lab11/signpost/case/media/solar_panel_on_signpost_ann_arbor.JPG

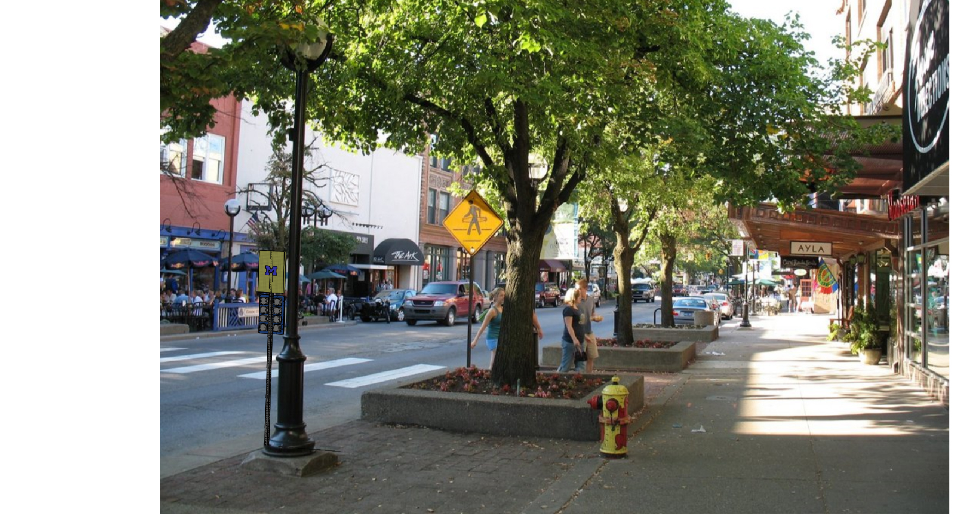
case/media/solar_panel_on_signpost_ann_arbor.JPG
