lab11/signpost/case/quotes/back_panel_quote_proto.JPG

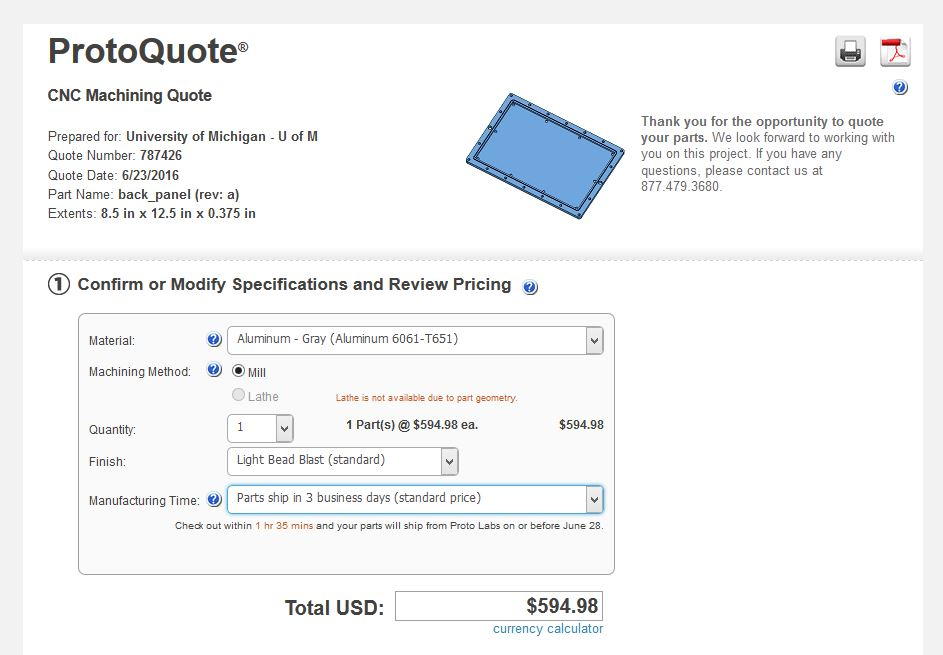
case/quotes/back_panel_quote_proto.JPG
