lab11/signpost/case/quotes/emachineshop.JPG

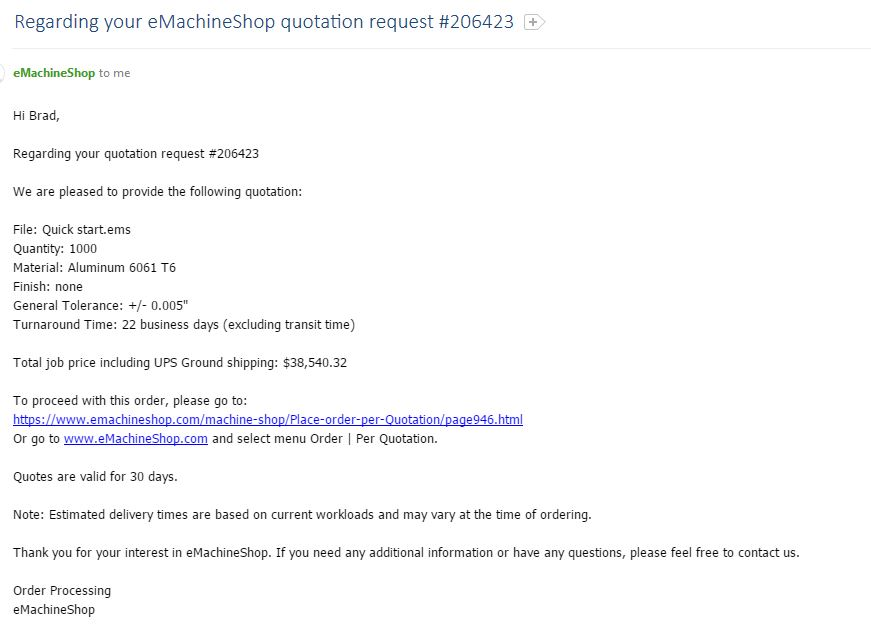
case/quotes/emachineshop.JPG
