lab11/signpost/case/quotes/quick_cut_gasket_oring_quote.jpg

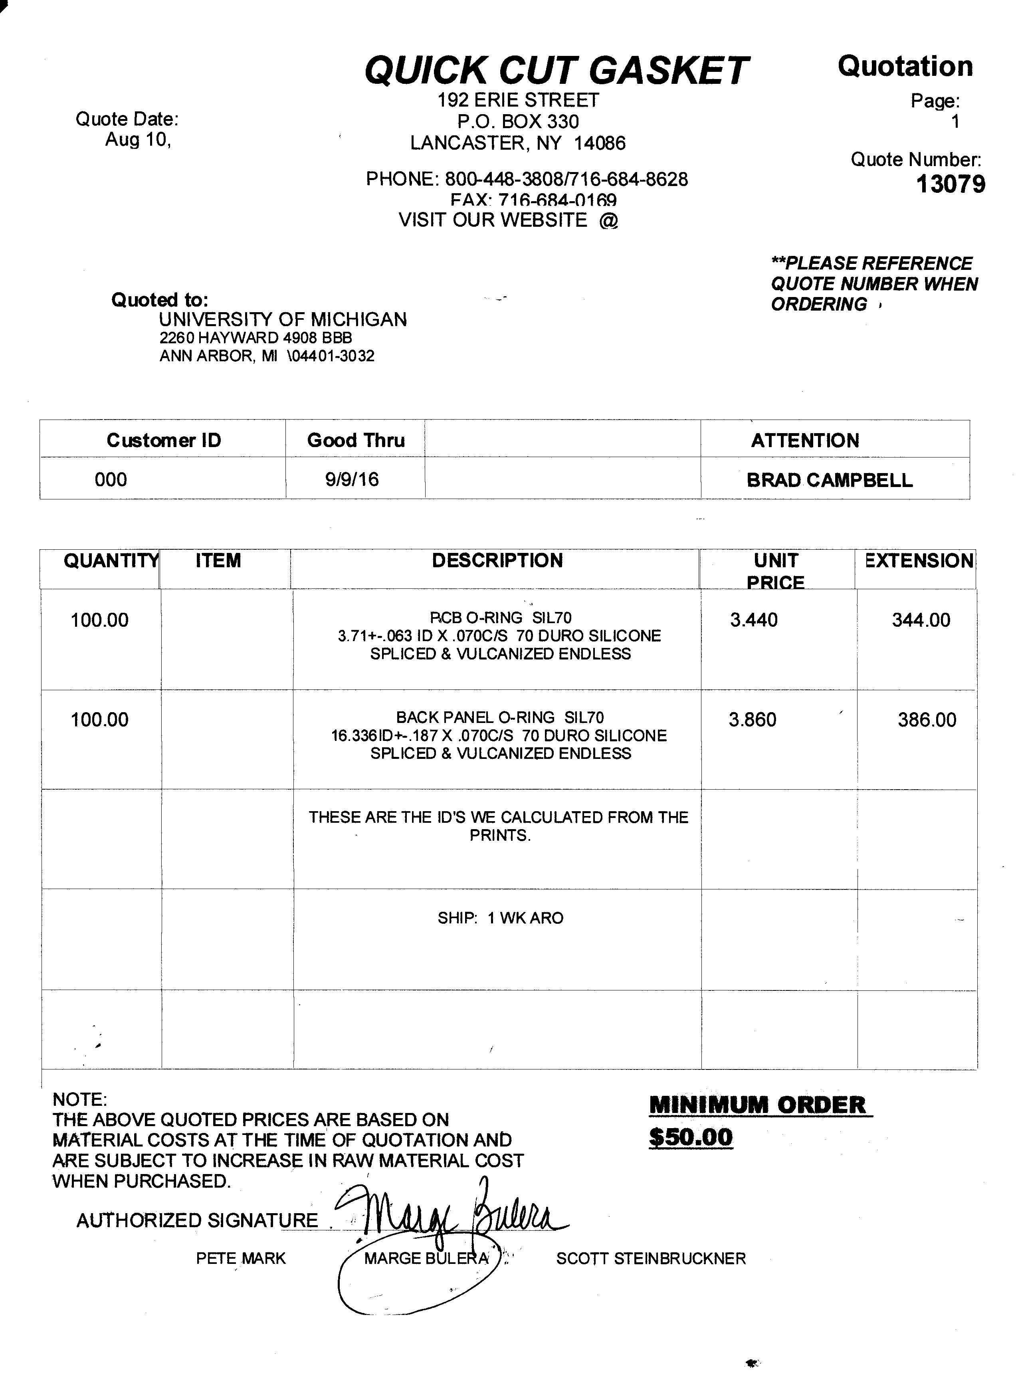
case/quotes/quick_cut_gasket_oring_quote.jpg
