lab11/signpost/case/quotes/xcentric.JPG

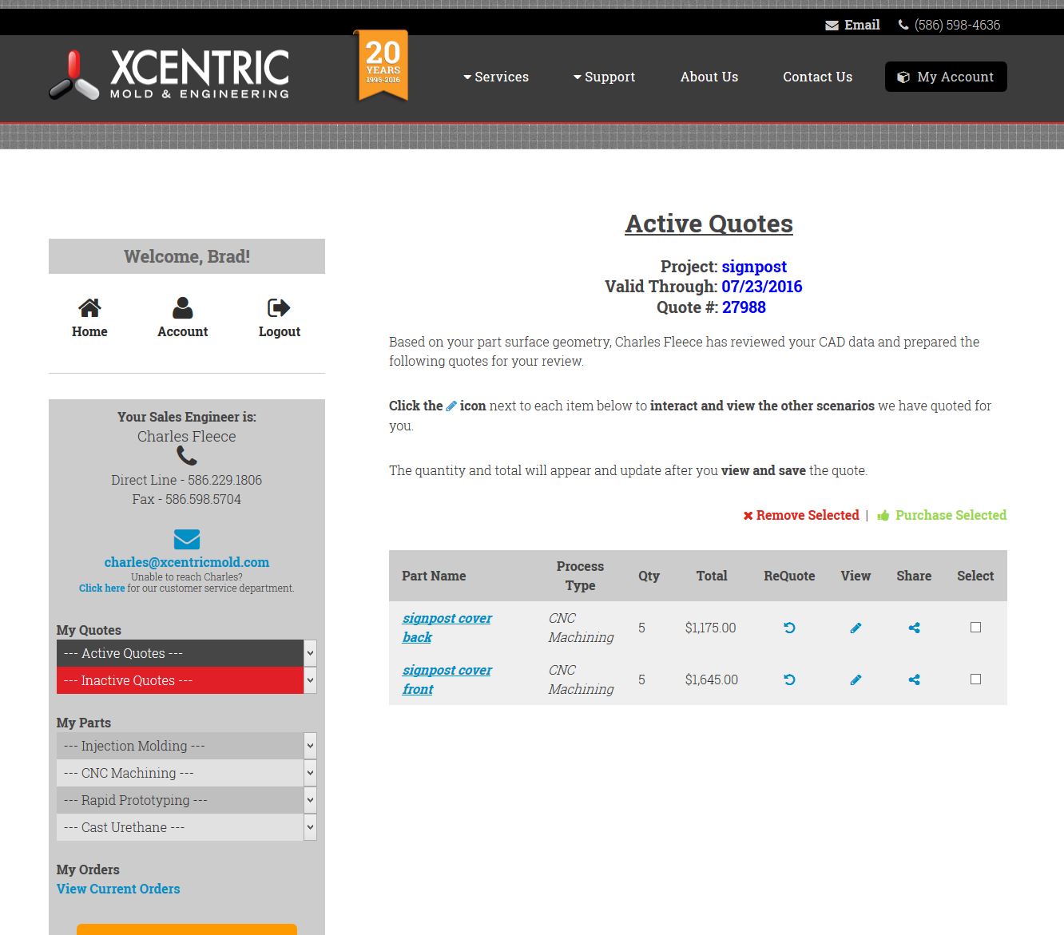
case/quotes/xcentric.JPG
