lab11/signpost/case/quotes/xometry_quote.JPG

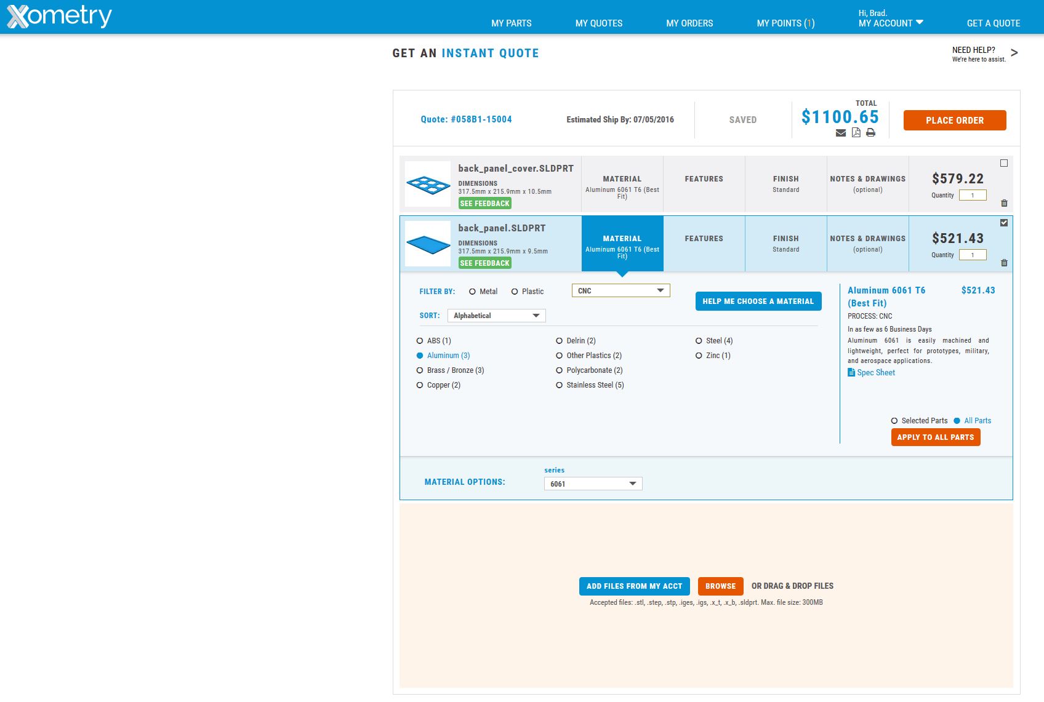
case/quotes/xometry_quote.JPG
