lab11/signpost/media/IntelDeployment.jpg

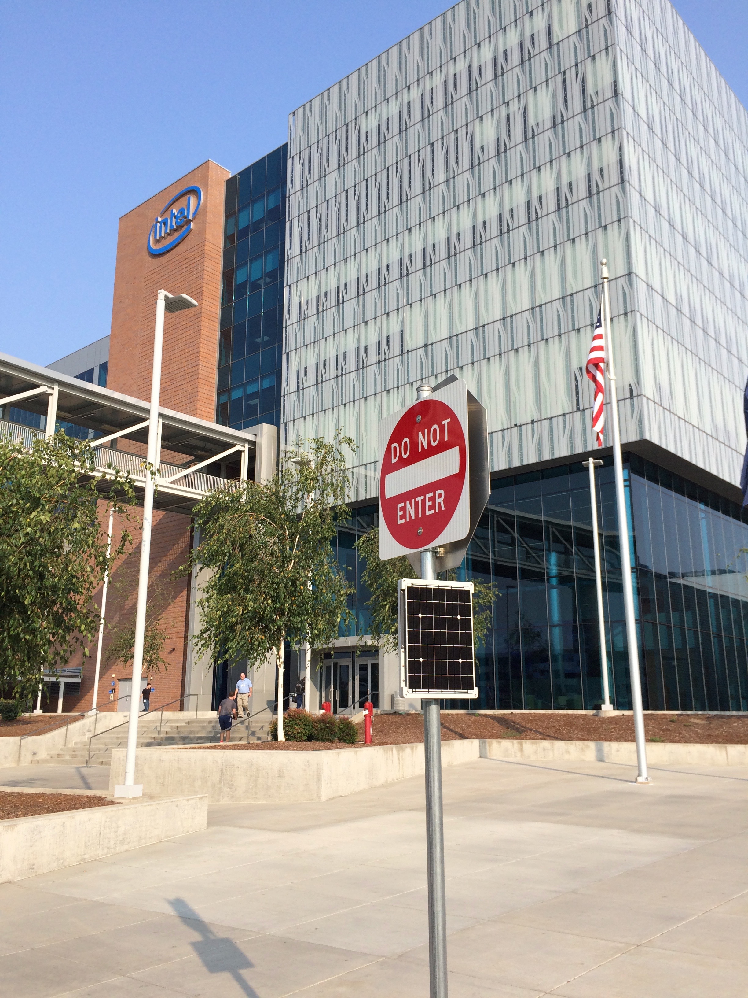
media/IntelDeployment.jpg
