lab11/signpost/media/signpost_case_cad_side_cutout.png

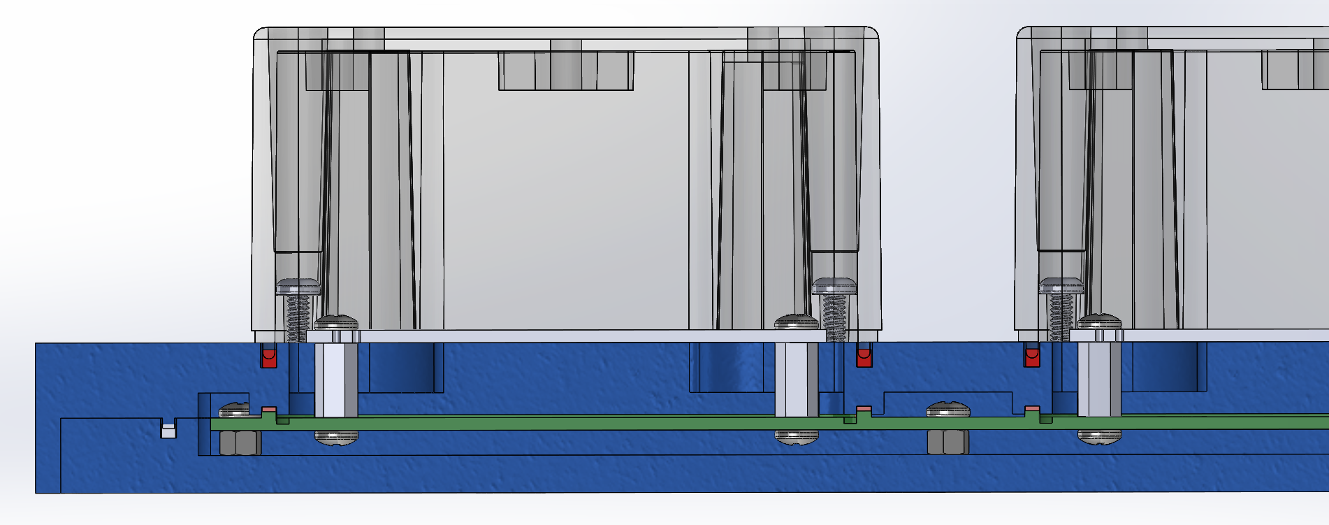
media/signpost_case_cad_side_cutout.png
