lab11/signpost/media/signpost_in_ann_arbor.jpg

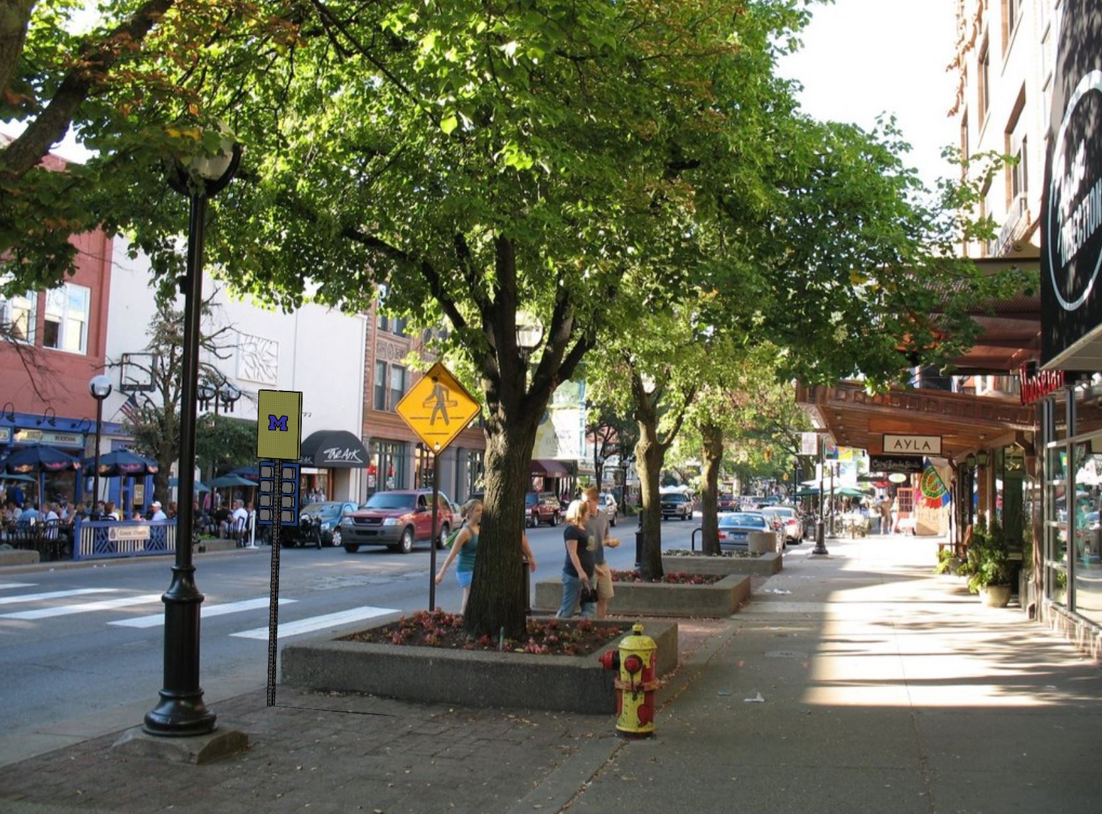
media/signpost_in_ann_arbor.jpg
