lab11/signpost/media/solar_panel_on_signpost6_cropped.jpg

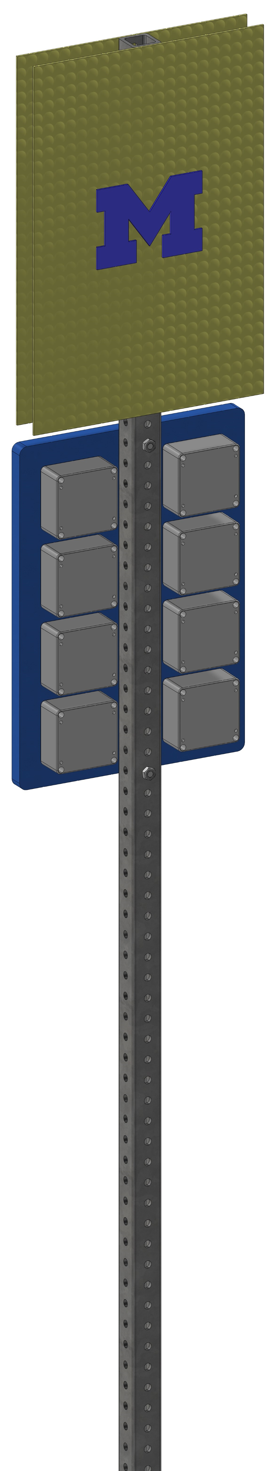
media/solar_panel_on_signpost6_cropped.jpg
