lab11/signpost/modules/ambient/rev_d/ambient.jpg

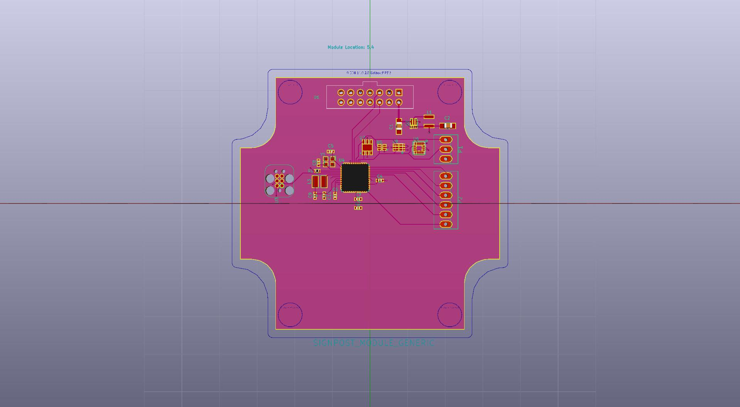
modules/ambient/rev_d/ambient.jpg
