lab11/signpost/hardware/debug_backplane/rev_b/debug_backplane_bom.txt

# Bill of Materials
# Converted from debug_backplane_bom.xlsx
# Generated by bom_to_text.py
#
Part               Value                              Device                             Package                             Description                                                                   DIGIKEY                    DIGIKEY2  DIGIKEY3  DIGIKEY4  DNP  Notes
C1                 8pF                                CAPACITOR0603_CAP                  0603_CAP                            0402 Capacitor                                                                1276-2141-1-ND                                                
C2                 8pF                                CAPACITOR0603_CAP                  0603_CAP                            0402 Capacitor                                                                1276-2141-1-ND                                                
C3                 22pF                               CAPACITOR0603_CAP                  0603_CAP                            0402 Capacitor                                                                478-1167-1-ND                                                 
C4                 22pF                               CAPACITOR0603_CAP                  0603_CAP                            0402 Capacitor                                                                478-1167-1-ND                                                 
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
D5                 LED0603                            LED0603                            LED-0603                            LED                                                                           160-1446-1-ND                                                 
D6                 LED0603                            LED0603                            LED-0603                            LED                                                                           160-1446-1-ND                                                 
D7                 SN75240-TSSOP                      SN75240-TSSOP                      TSSOP-8                             TVS Diodes [suggested for TI USB Hub] (2 array)                               296-6596-1-ND                                                 
D8                 SN75240-TSSOP                      SN75240-TSSOP                      TSSOP-8                             TVS Diodes [suggested for TI USB Hub] (2 array)                               296-6596-1-ND                                                 
D9                 LED0603                            LED0603                            LED-0603                            LED                                                                           160-1446-1-ND                                                 
FB1                600R                               FERRITE_BEAD0603                   0603_CAP                                                                                                          732-1593-1-ND                                                 
FB2                600R                               FERRITE_BEAD0603                   0603_CAP                                                                                                          732-1593-1-ND                                                 
FB3                600R                               FERRITE_BEAD0603                   0603_CAP                                                                                                          732-1593-1-ND                                                 
FB4                600R                               FERRITE_BEAD0603                   0603_CAP                                                                                                          732-1593-1-ND                                                 
FB5                600R                               FERRITE_BEAD0603                   0603_CAP                                                                                                          732-1593-1-ND                                                 
FB6                1.5kR                              FERRITE_BEAD0603                   0603_CAP                                                                                                          490-5216-1-ND                                                 
J1                 BACKPLANE_CONTROLLER_MODULE_DEBUG  BACKPLANE_CONTROLLER_MODULE_DEBUG  BACKPLANE_MODULE_20PIN_10PIN_DEBUG  Control module for signpost, with debug headers                               S9197-ND                   S9194-ND  S7072-ND  S7072-ND       
J2                 BACKPLANE_GENERIC_MODULE_DEBUG     BACKPLANE_GENERIC_MODULE_DEBUG     BACKPLANE_MODULE_14PIN_8PIN         A backplane header for the debug module                                       S9195-ND                   S7072-ND                           
J3                 BACKPLANE_GENERIC_MODULE_DEBUG     BACKPLANE_GENERIC_MODULE_DEBUG     BACKPLANE_MODULE_14PIN_8PIN         A backplane header for the debug module                                       S9195-ND                   S7072-ND                           
J4                 MICRO_USB_B_HIROSE_ZX62R-B-5P      MICRO_USB_B_HIROSE_ZX62R-B-5P      USB_MICRO_B-HIROSE-ZX62R-B-5P       USB Micro B Connector                                                         H11574CT-ND                                                   
J5                 MICRO_USB_B_HIROSE_ZX62R-B-5P      MICRO_USB_B_HIROSE_ZX62R-B-5P      USB_MICRO_B-HIROSE-ZX62R-B-5P       USB Micro B Connector                                                         H11574CT-ND                                                   
J6                 MICRO_USB_B_HIROSE_ZX62R-B-5P      MICRO_USB_B_HIROSE_ZX62R-B-5P      USB_MICRO_B-HIROSE-ZX62R-B-5P       USB Micro B Connector                                                         H11574CT-ND                                                   
J7                 MICRO_USB_B_HIROSE_ZX62R-B-5P      MICRO_USB_B_HIROSE_ZX62R-B-5P      USB_MICRO_B-HIROSE-ZX62R-B-5P       USB Micro B Connector                                                         H11574CT-ND                                                   
J8                 MICRO_USB_B_HIROSE_ZX62R-B-5P      MICRO_USB_B_HIROSE_ZX62R-B-5P      USB_MICRO_B-HIROSE-ZX62R-B-5P       USB Micro B Connector                                                         H11574CT-ND                                                   
J9                 MICRO_USB_B_HIROSE_ZX62R-B-5P      MICRO_USB_B_HIROSE_ZX62R-B-5P      USB_MICRO_B-HIROSE-ZX62R-B-5P       USB Micro B Connector                                                         H11574CT-ND                                                   
J10                                                   ML20                               ML20                                HARTING                                                                       S9172-ND                                                      
J11                PJ-102AH                           PJ-102AH                           PJ-102AH                            DC Power Jack                                                                 CP-102AH-ND                                                   
J12                Debug Header                       2x5 - 0.1" header                  2x5 - 0.1" header                                                                                                 609-3243-ND                                                   
J13                Debug Header                       2x5 - 0.1" header                  2x5 - 0.1" header                                                                                                 609-3243-ND                                                   
J14                Debug Header                       2x5 - 0.1" header                  2x5 - 0.1" header                                                                                                 609-3243-ND                                                   
J15                Debug Header                       2x5 - 0.1" header                  2x5 - 0.1" header                                                                                                 609-3243-ND                                                   
J16                Debug Header                       1x3 - 0.1" Header                  1x3 - 0.1" Header                                                                                                 3M9448-ND                                                     
J17                Debug Header                       1x3 - 0.1" Header                  1x3 - 0.1" Header                                                                                                 3M9448-ND                                                     
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
S8                 B3U-1000P                          B3U-1000P                          B3U-1000P                           Switch                                                                        SW1020CT-ND                                                   
S9                 NC7SZ157                           NC7SZ157                           SC70-6                              MUX                                                                           NC7SZ157P6XCT-ND                                              
S10                NC7SZ157                           NC7SZ157                           SC70-6                              MUX                                                                           NC7SZ157P6XCT-ND                                              
S11                RM106772BCB                        RM106772BCB                        RM-SWITCH                           Rotary Switch 6 Position SP6T 500mA (DC) 24VDC Through Hole                   CKN10703-ND                                                   
S12                SIP3240X                           SIP3240X                           TDFN4                               High power (2.4 A) high-side switch                                           SIP32402ADNP-T1GE4CT-ND                                       
S13                SIP3240X                           SIP3240X                           TDFN4                               High power (2.4 A) high-side switch                                           SIP32402ADNP-T1GE4CT-ND                                       
S14                SN74AHC4066-RGY                    SN74AHC4066-RGY                    S-PVQFN-N14-3.5MM                                                                                                 296-15258-1-ND                                                
S15                SN74AHC4066-RGY                    SN74AHC4066-RGY                    S-PVQFN-N14-3.5MM                                                                                                 296-15258-1-ND                                                
S16                SN74AHC4066-RGY                    SN74AHC4066-RGY                    S-PVQFN-N14-3.5MM                                                                                                 296-15258-1-ND                                                
S17                SN74AHC4066-RGY                    SN74AHC4066-RGY                    S-PVQFN-N14-3.5MM                                                                                                 296-15258-1-ND                                                
S18                SN74AHC4066-RGY                    SN74AHC4066-RGY                    S-PVQFN-N14-3.5MM                                                                                                 296-15258-1-ND                                                
S19                TE_SSA12/SPDT                      TE_SSA12/SPDT                      TE_SSA12/SPDT                       SWITCH SLIDE SPDT 2POS SSA SER                                                450-1602-ND                                                   
TP_GND             TEST_POINT_0.040IN                 TEST_POINT_0.040IN                 TESTPOINT_0.040IN                   0.040in Test Point                                                            36-5001-ND                                                    As Labeled on board - under J11
TP_5V              TEST_POINT_0.040IN                 TEST_POINT_0.040IN                 TESTPOINT_0.040IN                   0.040in Test Point                                                            36-5000-ND                                                    As Labeled on board - under J12
TP_3V3             TEST_POINT_0.040IN                 TEST_POINT_0.040IN                 TESTPOINT_0.040IN                   0.040in Test Point                                                            36-5000-ND                                                    As Labeled on board - under J13
TP_Mod0_VCC        TEST_POINT_0.040IN                 TEST_POINT_0.040IN                 TESTPOINT_0.040IN                   0.040in Test Point                                                            36-5003-ND                                                    As Labeled on board - under J14
TP_Mod1_VCC        TEST_POINT_0.040IN                 TEST_POINT_0.040IN                 TESTPOINT_0.040IN                   0.040in Test Point                                                            36-5003-ND                                                    As Labeled on board - under J15
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
U5                 FT232RQ                            FT232RQ                            QFN32                               Source: http://www.ftdichip.com/Documents/DataSheets/DS_FT232R_v104.pdf       768-1307-ND                                                   
U6                 FXMA2102                           FXMA2102                           UMLP-8                              Dual Supply, 2-Bit Voltage Translator / Buffer / Repeater / Isolator for I2C  FXMA2102UMXCT-ND                                              
U7                 FXMA2102                           FXMA2102                           UMLP-8                              Dual Supply, 2-Bit Voltage Translator / Buffer / Repeater / Isolator for I2C  FXMA2102UMXCT-ND                                              
U8                 LTC2941                            LTC2941                            DFN-6-2MMX3MM                       I2C Battery Gas Gauge                                                         LTC2941IDCB#TRMPBFCT-ND                                       
U9                 LTC2941                            LTC2941                            DFN-6-2MMX3MM                       I2C Battery Gas Gauge                                                         LTC2941IDCB#TRMPBFCT-ND                                       
U10                LTC2941                            LTC2941                            DFN-6-2MMX3MM                       I2C Battery Gas Gauge                                                         LTC2941IDCB#TRMPBFCT-ND                                       
U11                LTC2941                            LTC2941                            DFN-6-2MMX3MM                       I2C Battery Gas Gauge                                                         LTC2941IDCB#TRMPBFCT-ND                                       
U12                MAX8887EZK33+T                     MAX8887EZK33+T                     SOT-23-5                            IC REG LDO 3.3V 0.3A TSOT23-5                                                 MAX8887EZK33+TCT-ND                                           
U13                MCP23008QFN                        MCP23008QFN                        QFN-20-4MM                          GPIO Extender via I2C - 8 Pin                                                 MCP23008-E/ML-ND                                              
U14                MCP23008QFN                        MCP23008QFN                        QFN-20-4MM                          GPIO Extender via I2C - 8 Pin                                                 MCP23008-E/ML-ND                                              
U15                PCA9544AQFN-N20                    PCA9544AQFN-N20                    QFN-N20                             1-4 I2C/SMBUS Multiplexer with interrupt for power supply coulomb counters    296-20960-1-ND                                                
U16                SAM4LC8AA                          SAM4LC8AA                          QFN-48-7MM                          Atmel SAM4L microcontroller. ARM Cortex M4 with 512 KB Flash and 64 KB RAM    ATSAM4LC8AA-MU-ND                                             
U17                SN74LVC2T45                        SN74LVC2T45                        VFSOP-8                             Bidirectional Buffer / Level Converter 2 Circuits                             296-17014-1-ND                                                
U18                SN74LVC2T45                        SN74LVC2T45                        VFSOP-8                             Bidirectional Buffer / Level Converter 2 Circuits                             296-17014-1-ND                                                
U19                SN74LVC2T45                        SN74LVC2T45                        VFSOP-8                             Bidirectional Buffer / Level Converter 2 Circuits                             296-17014-1-ND                                                
U20                SN74LVC2T45                        SN74LVC2T45                        VFSOP-8                             Bidirectional Buffer / Level Converter 2 Circuits                             296-17014-1-ND                                                
U21                TS3USB30E                          TS3USB30E                          UQFN-10                             USB Mux with OE control and ESD                                               296-24684-1-ND                                                
U22                TS3USB30E                          TS3USB30E                          UQFN-10                             USB Mux with OE control and ESD                                               296-24684-1-ND                                                
U23                TS3USB30E                          TS3USB30E                          UQFN-10                             USB Mux with OE control and ESD                                               296-24684-1-ND                                                
U24                TUSB2077A                          TUSB2077A                          LQFP-48                             Full Speed USB Hub - 7 Port                                                   296-37871-1-ND                                                
U25                LTC4360                            LTC4360                            SC70-8                              An overvoltage protection IC. Clamps at 5.5V                                  LTC4360CSC8-1#TRMPBFCT-ND                                     
X1                 16MHz                              FH1600015                          FHXXX                               Pericom Type FH 16 MHz 2.5 x 2.0 mm                                           FH1600015CT-ND                                                
Y1                 ABMM                               ABMM                               ABMM                                Low-Profile SMD crystal                                                       535-10156-1-ND
