lab11/signpost/hardware/debug_backplane/rev_b/debug_backplane_bom_digikey.txt

# Bill of Materials
# Converted from debug_backplane_bom_digikey.xlsx
# Generated by bom_to_text.py
#
# Part List           Digikey Part Number        QTY
C1-2                 1276-2141-1-ND             2
C11                  490-1313-1-ND              1
C12-15 45            478-1129-1-ND              5
C16-44 46-61         490-1532-1-ND              45
C3-4                 478-1167-1-ND              2
C5-10                399-8827-1-ND              6
C62-63               490-3296-1-ND              2
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
