lab11/signpost/case/parts/For_UM_Machine_Shop/back_panel_cover/2D/back_panel_cover.JPG

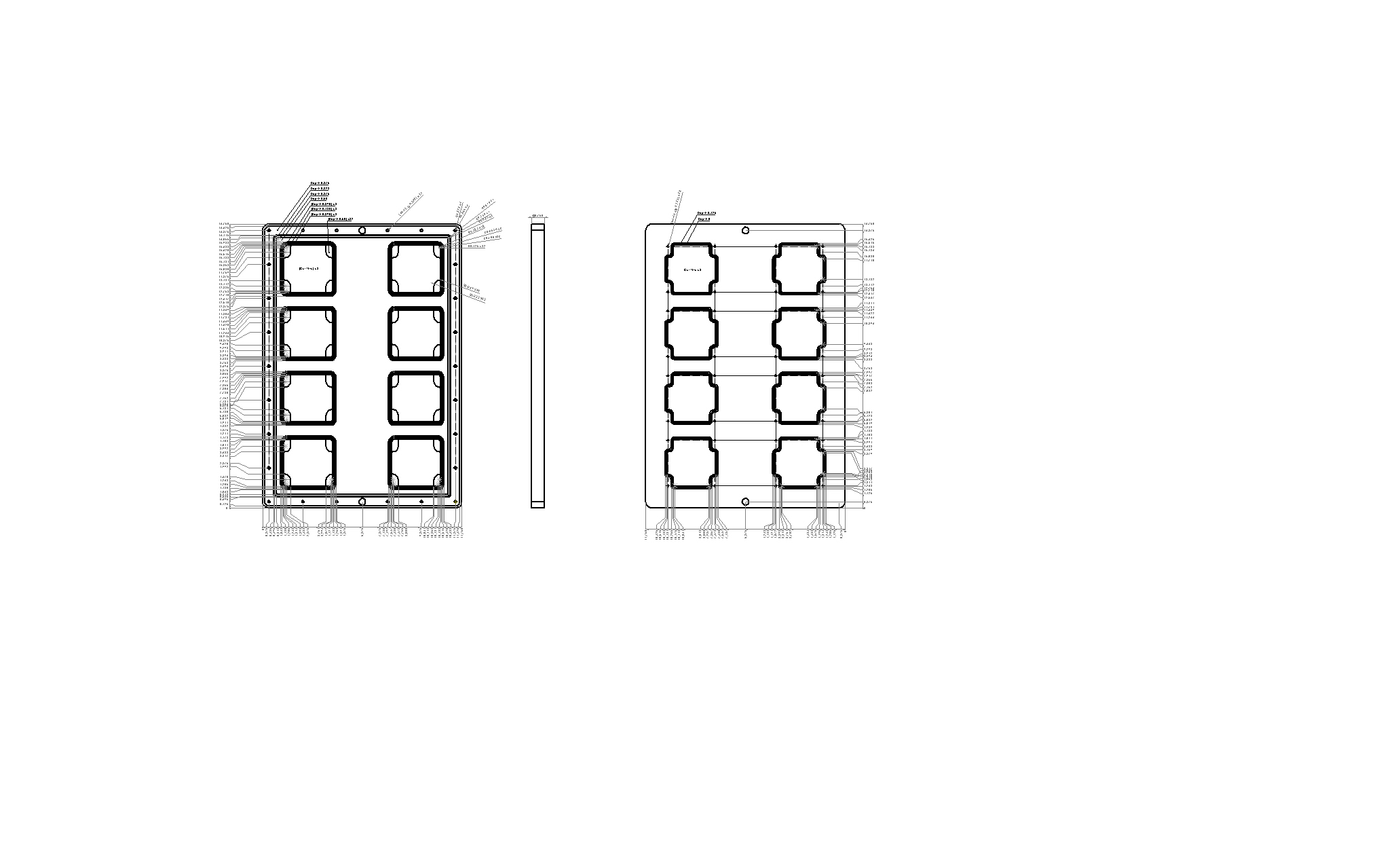
case/parts/For_UM_Machine_Shop/back_panel_cover/2D/back_panel_cover.JPG
