lab11/signpost/case/parts/For_UM_Machine_Shop/solar_mount/2D/solar_mount.JPG

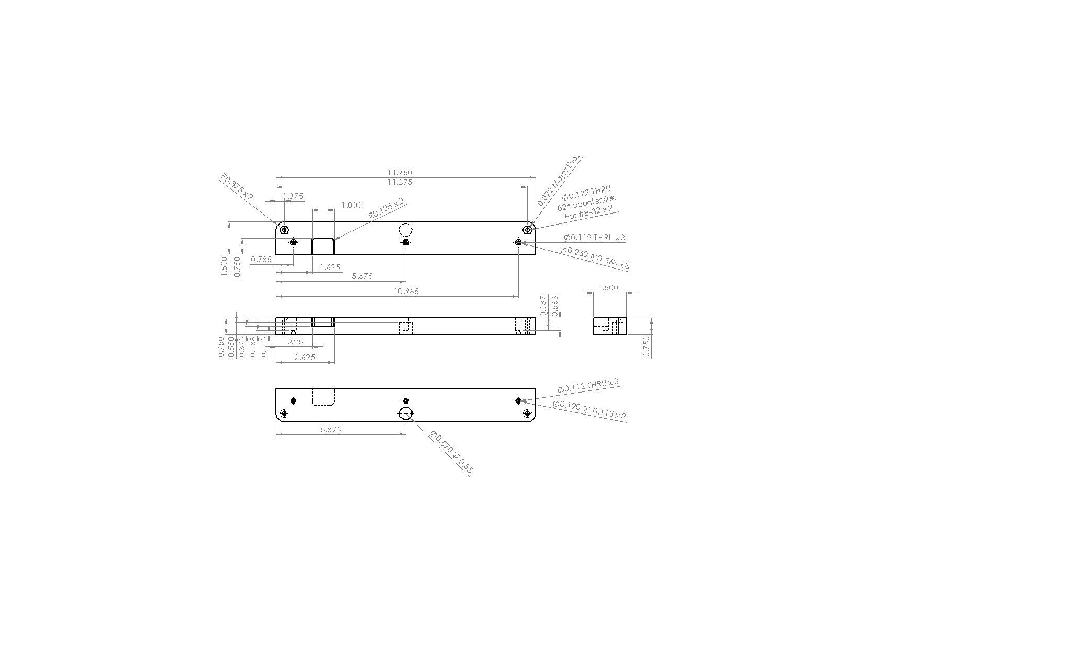
case/parts/For_UM_Machine_Shop/solar_mount/2D/solar_mount.JPG
