lab11/signpost/case/parts/Product_files/sunpe_04_28_2017/battery_case_top.STEP

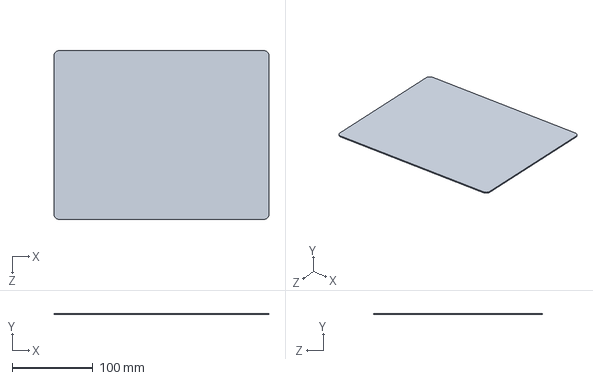
[picture p40: CAD file, 2017-05-03]
case/parts/Product_files/sunpe_04_28_2017/battery_case_top.STEP
266.7 x 1.59 x 209.4 mm
