lab11/signpost/case/parts/back_panel_cover.SLDPRT

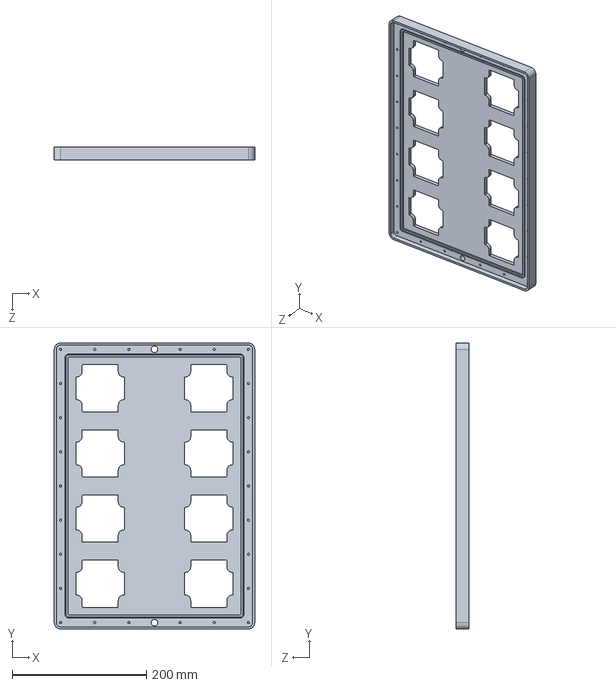
[picture p41: CAD file, 2017-04-20]
case/parts/back_panel_cover.SLDPRT
298.5 x 425.5 x 19.1 mm
