lab11/signpost/case/parts/battery_case_back.STEP

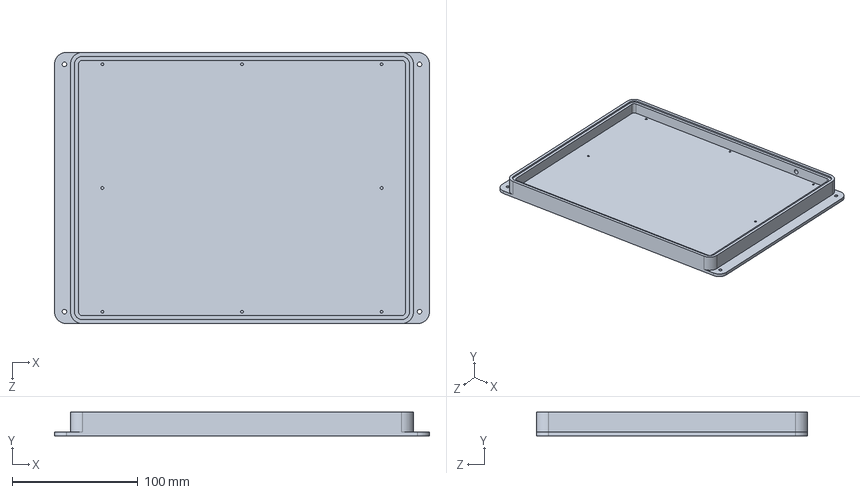
[picture p42: CAD file, 2017-02-01]
case/parts/battery_case_back.STEP
298.4 x 19.1 x 215.9 mm
