lab11/signpost/case/parts/COTS_hardware/round_sign_bracket.SLDPRT

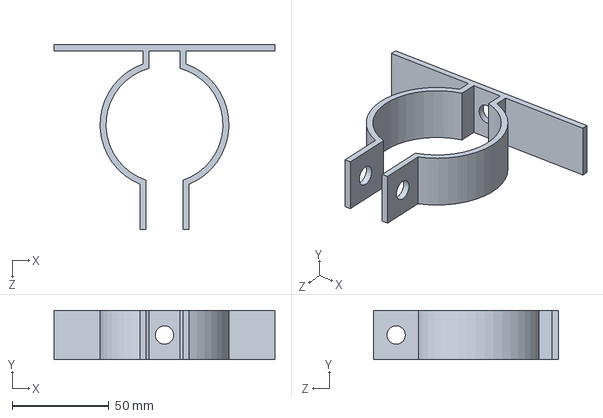
[picture p43: CAD file, 2017-01-26]
case/parts/COTS_hardware/round_sign_bracket.SLDPRT
114.3 x 25.4 x 95.5 mm
