lab11/signpost/case/parts/round_post.SLDPRT

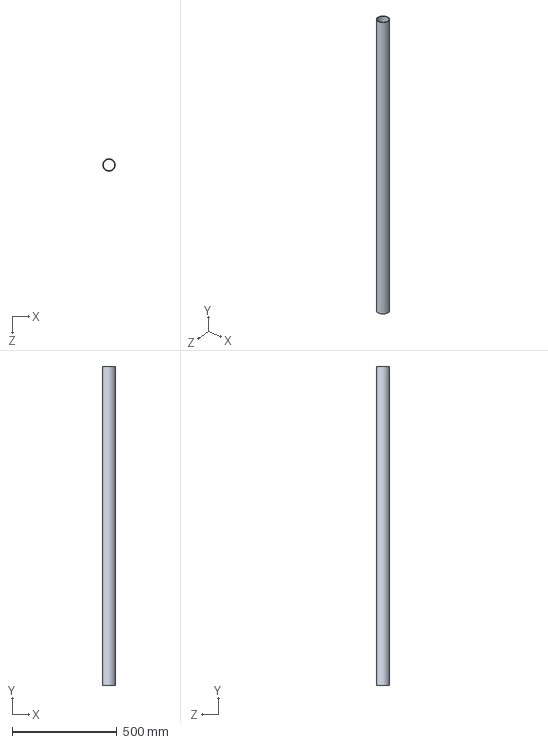
[picture p44: CAD file, 2017-01-26]
case/parts/round_post.SLDPRT
60.5 x 1524.0 x 60.5 mm
