lab11/signpost/case/parts/module_pcb.SLDPRT

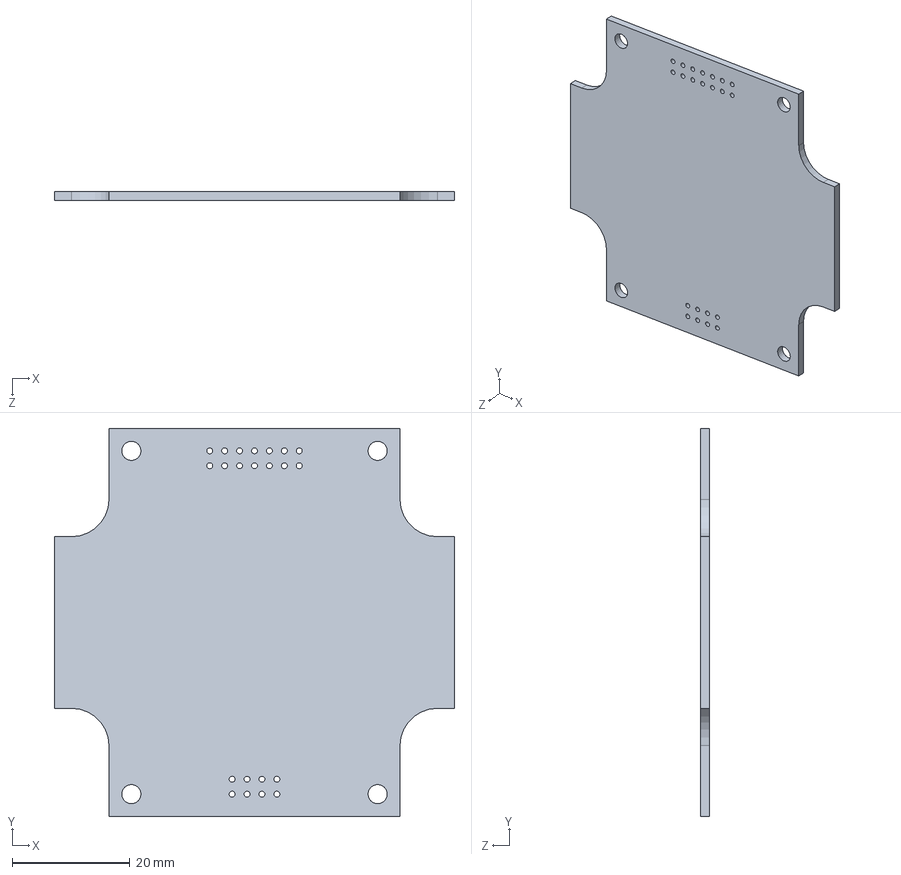
[picture p45: CAD file, 2017-01-19]
case/parts/module_pcb.SLDPRT
68.1 x 66.0 x 1.59 mm
