lab11/signpost/case/parts/batter_pack_pcb.SLDPRT

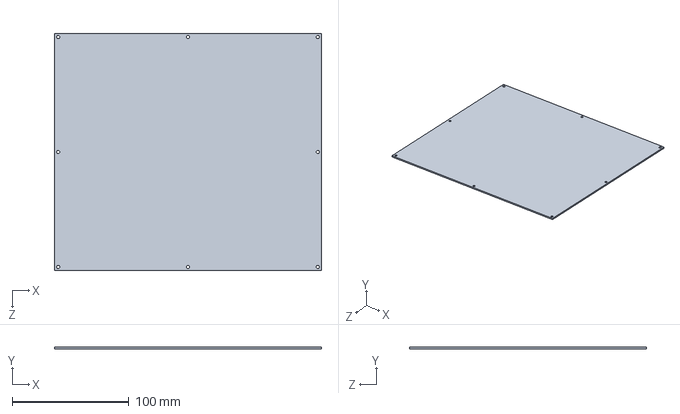
[picture p46: CAD file, 2017-01-08]
case/parts/batter_pack_pcb.SLDPRT
228.6 x 1.59 x 203.2 mm
