lab11/signpost/case/parts/battery_cell.SLDPRT

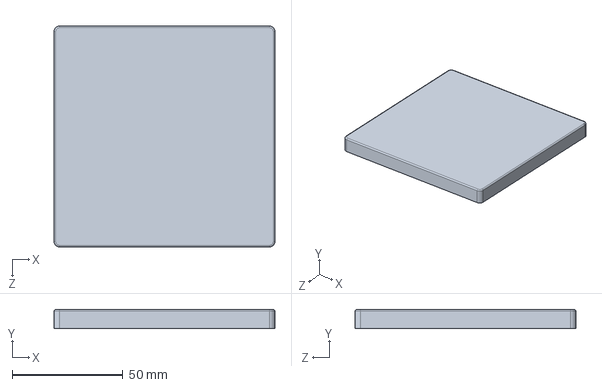
[picture p47: CAD file, 2017-01-08]
case/parts/battery_cell.SLDPRT
100.0 x 8.60 x 100.0 mm
