lab11/signpost/case/parts/battery_case_front.SLDPRT

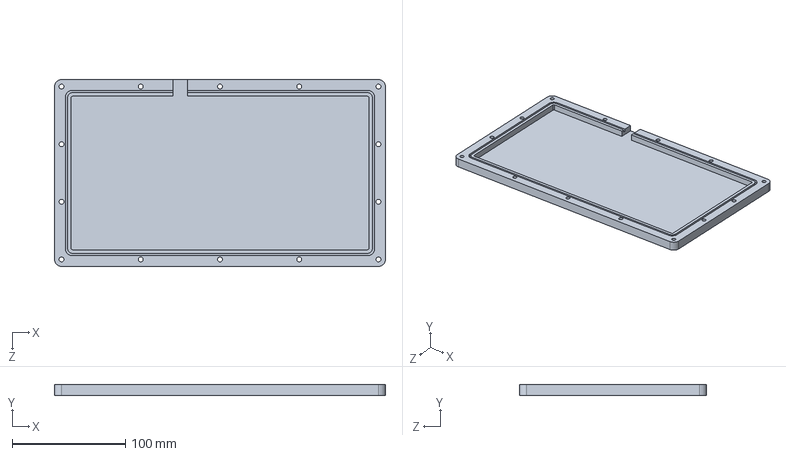
[picture p48: CAD file, 2016-09-11]
case/parts/battery_case_front.SLDPRT
291.8 x 9.53 x 164.8 mm
