lab11/signpost/case/parts/17W Panel.SLDPRT

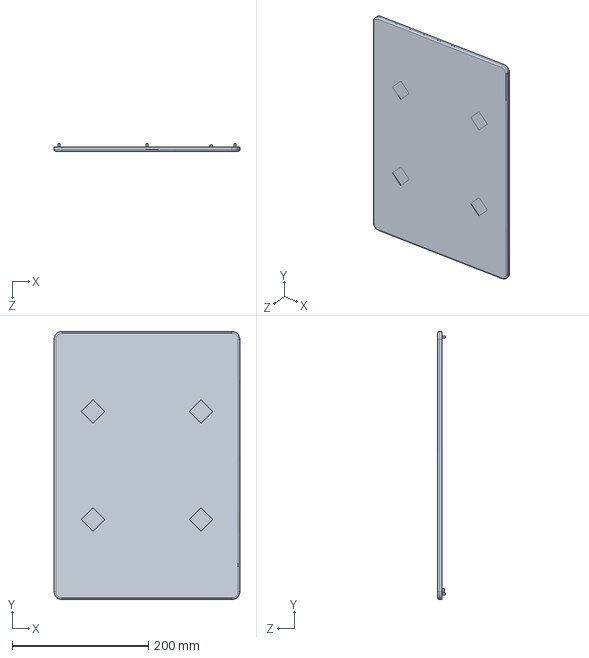
[picture p49: CAD file, 2016-09-11]
case/parts/17W Panel.SLDPRT
273.1 x 393.7 x 11.0 mm
