lab11/signpost/case/parts/gold_sign.SLDPRT

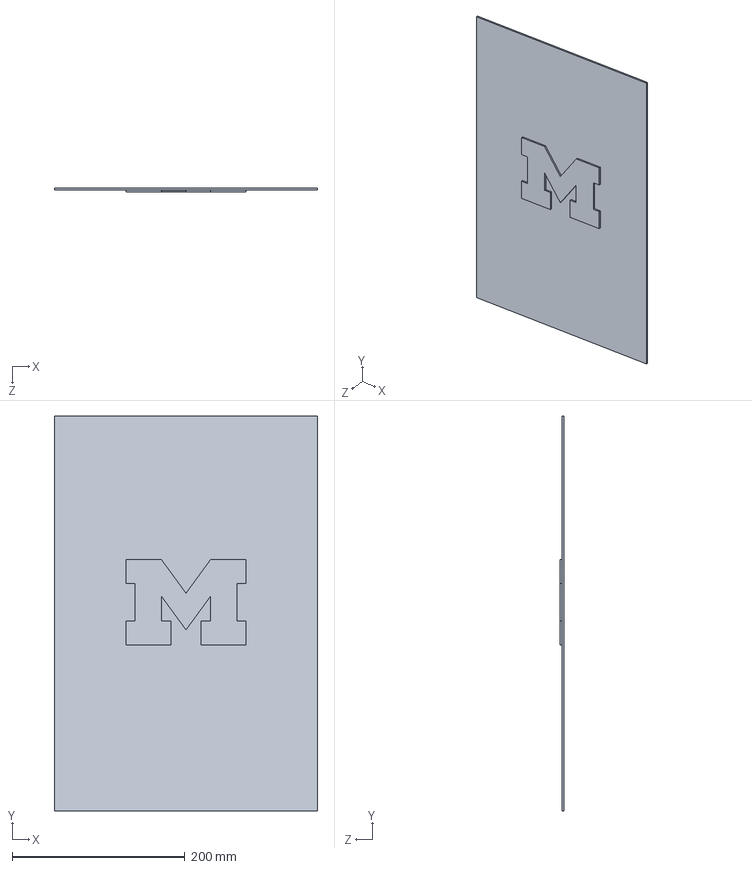
[picture p50: CAD file, 2016-08-11]
case/parts/gold_sign.SLDPRT
304.8 x 457.2 x 5.08 mm
