lab11/signpost/case/parts/SFH11-P_ _C-D07-ST-_ _.SLDPRT

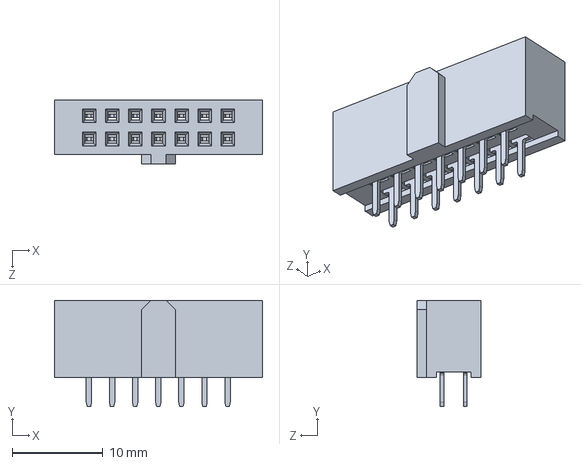
[picture p51: CAD file, 2016-08-09]
case/parts/SFH11-P_ _C-D07-ST-_ _.SLDPRT
22.9 x 11.7 x 7.00 mm
