lab11/signpost/case/parts/COTS_hardware/1-8-ips-3-4-long.SLDPRT

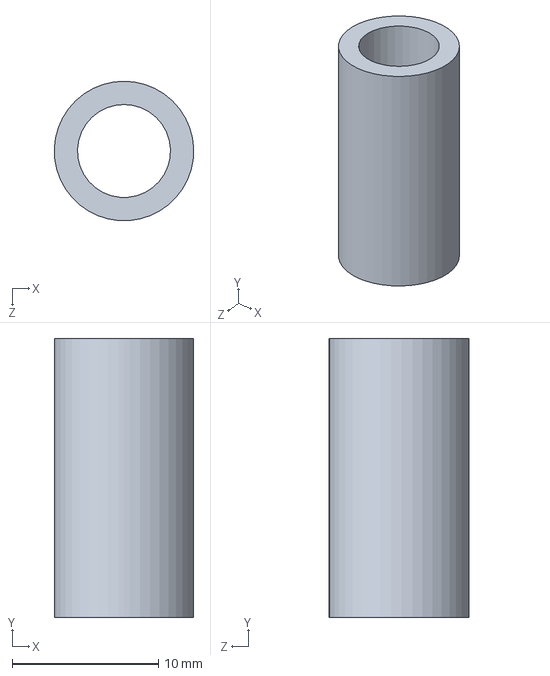
[picture p52: CAD file, 2016-09-11]
case/parts/COTS_hardware/1-8-ips-3-4-long.SLDPRT
9.52 x 19.1 x 9.53 mm
