lab11/signpost/case/parts/voltaic_17w_solar_panel_mount.SLDPRT

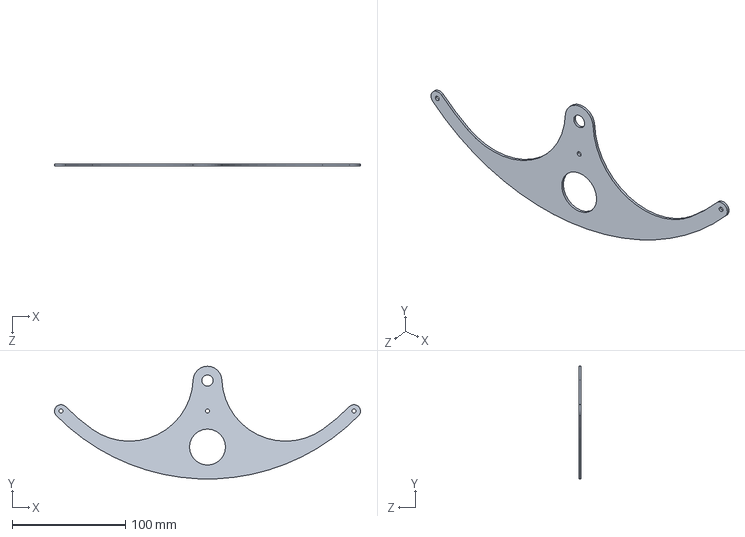
[picture p53: CAD file, 2016-08-08]
case/parts/voltaic_17w_solar_panel_mount.SLDPRT
270.0 x 99.4 x 1.90 mm
