lab11/signpost/case/parts/back_panel_oring.SLDPRT

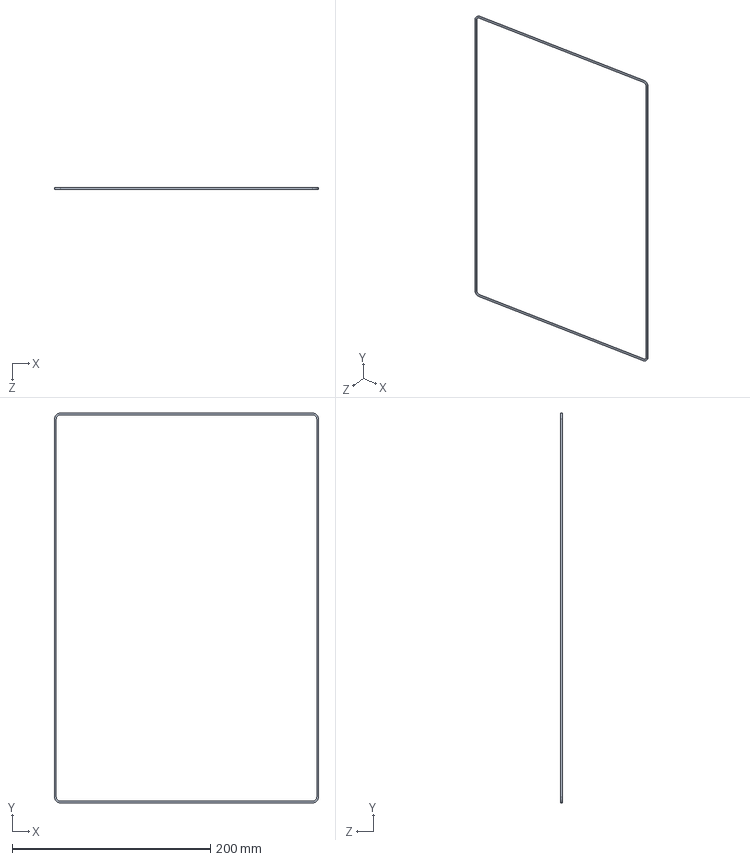
[picture p54: CAD file, 2016-08-08]
case/parts/back_panel_oring.SLDPRT
266.4 x 393.4 x 1.78 mm
