lab11/signpost/case/parts/module_pcb_oring.SLDPRT

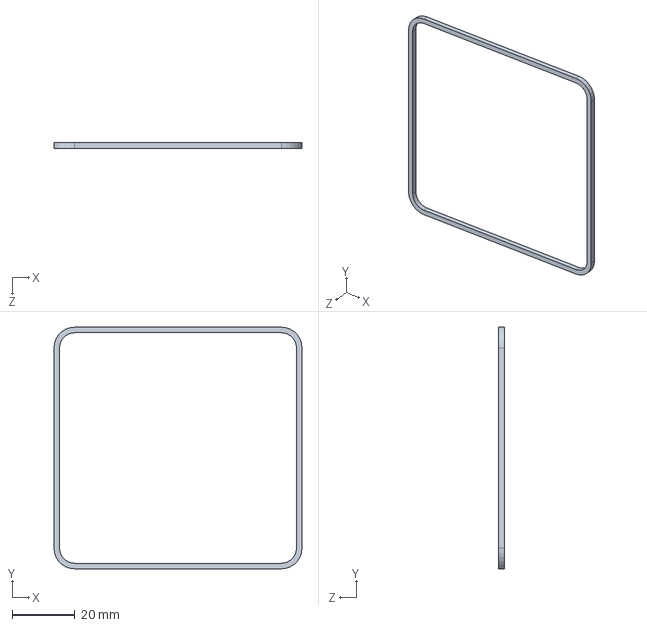
[picture p55: CAD file, 2016-08-08]
case/parts/module_pcb_oring.SLDPRT
79.3 x 77.3 x 1.78 mm
