lab11/signpost/case/parts/post.SLDPRT

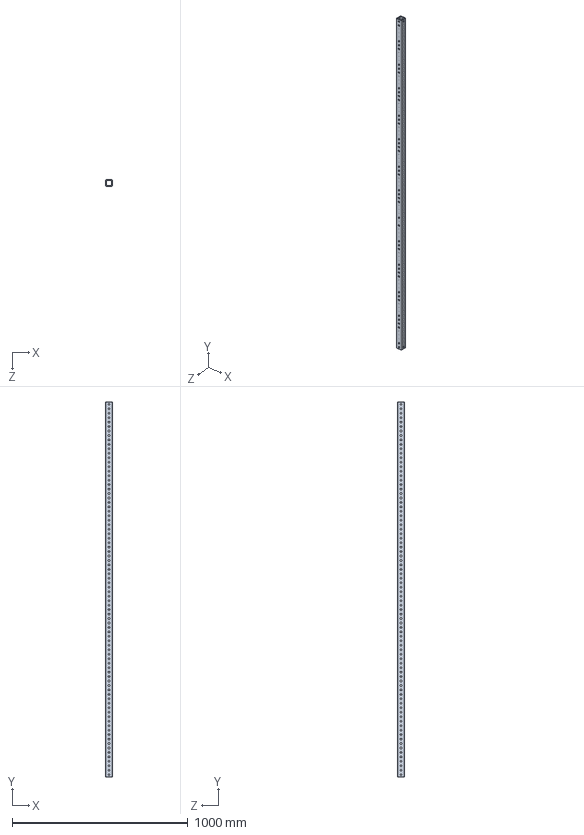
[picture p56: CAD file, 2016-07-01]
case/parts/post.SLDPRT
38.1 x 2133.6 x 38.1 mm
