lab11/signpost/case/parts/COTS_hardware/plug.SLDPRT

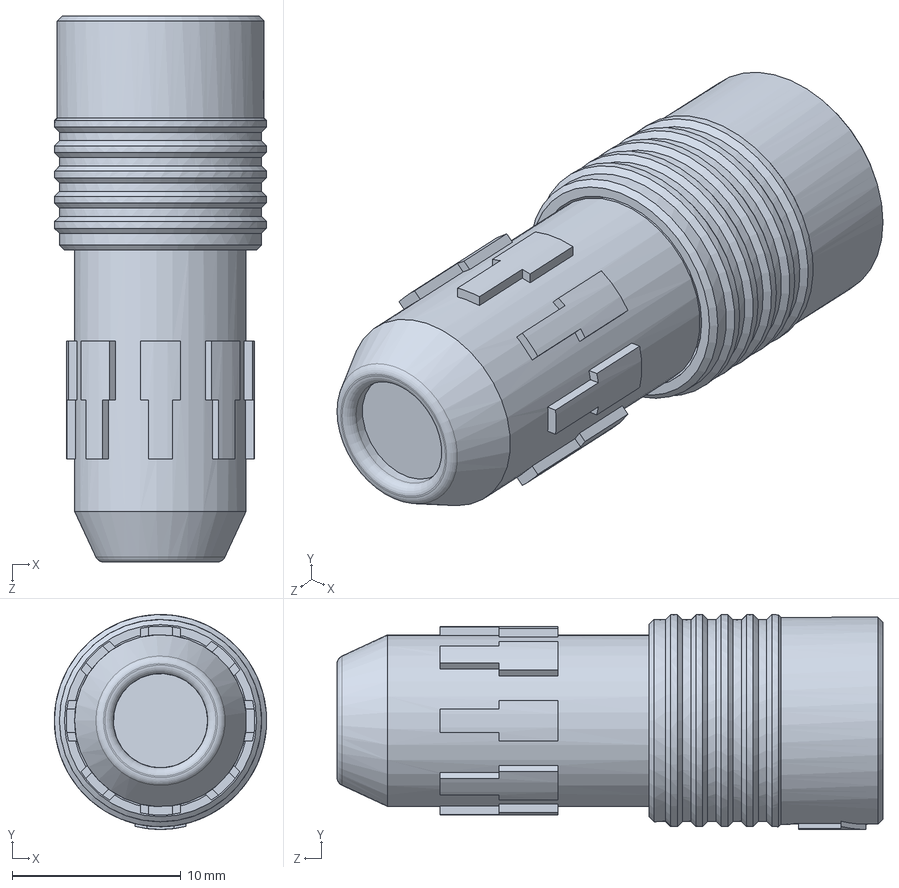
[picture p57: CAD file, 2016-09-11]
case/parts/COTS_hardware/plug.SLDPRT
12.6 x 12.8 x 32.4 mm
