lab11/signpost/case/parts/o_ring.SLDPRT

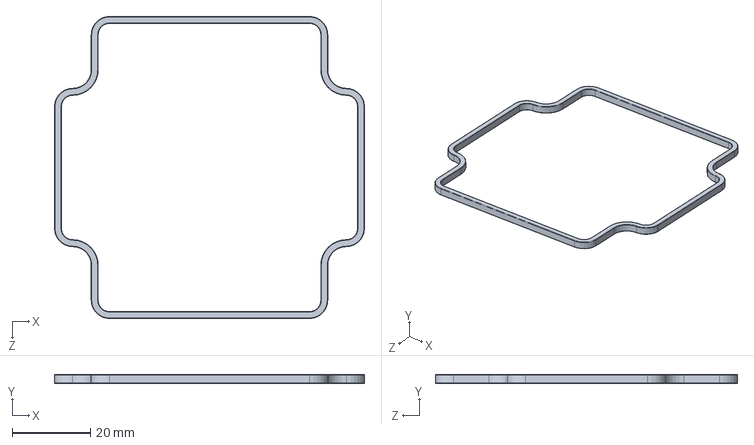
[picture p58: CAD file, 2016-06-20]
case/parts/o_ring.SLDPRT
79.3 x 2.29 x 77.3 mm
