lab11/signpost/case/parts/voltaic_9w_solar_panel_mount.SLDPRT

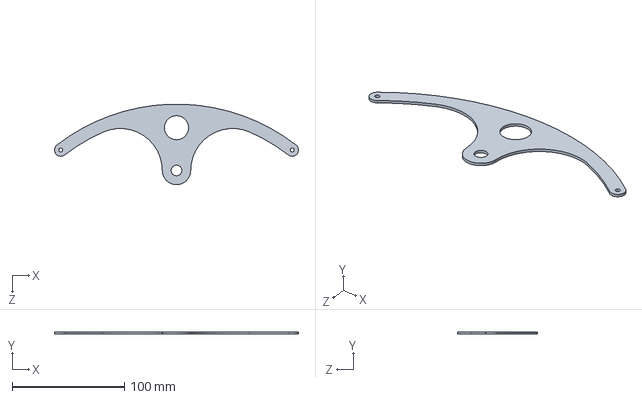
[picture p59: CAD file, 2016-06-20]
case/parts/voltaic_9w_solar_panel_mount.SLDPRT
217.5 x 1.90 x 71.7 mm
