lab11/signpost/case/parts/COTS_hardware/recepticale.SLDPRT

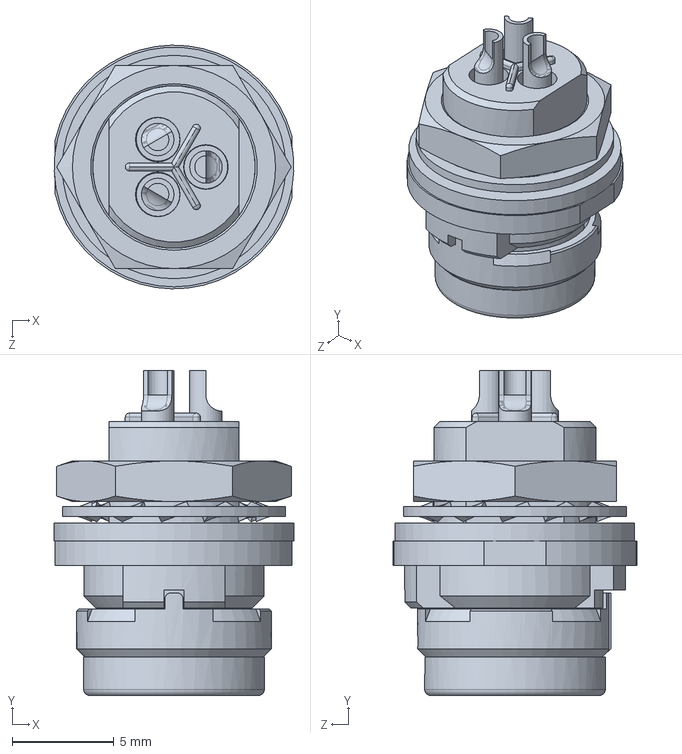
[picture p60: CAD file, 2016-09-11]
case/parts/COTS_hardware/recepticale.SLDPRT
11.8 x 16.0 x 12.0 mm
