lab11/signpost/case/parts/solar_panel.SLDPRT

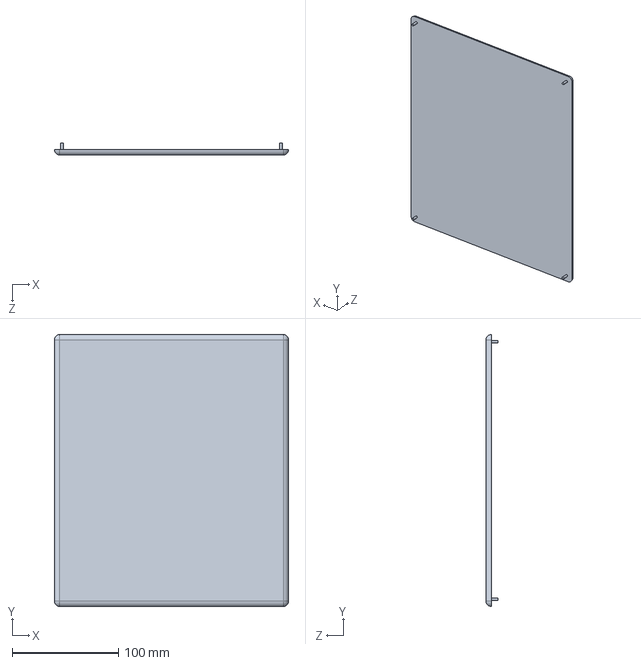
[picture p61: CAD file, 2016-06-20]
case/parts/solar_panel.SLDPRT
221.0 x 256.5 x 11.4 mm
