lab11/signpost/case/parts/box_top.SLDPRT

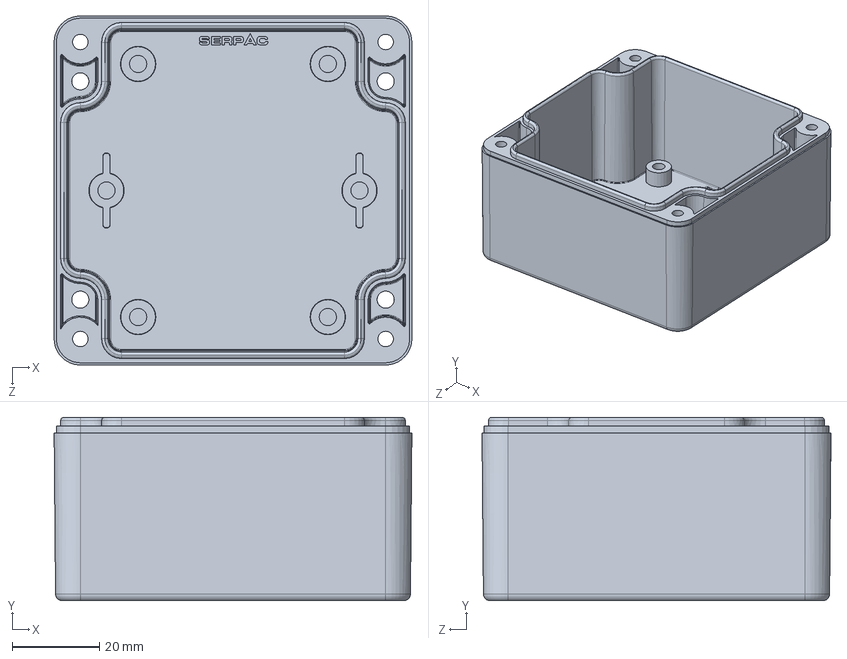
[picture p62: CAD file, 2016-06-20]
case/parts/box_top.SLDPRT
82.0 x 42.0 x 80.0 mm
