lab11/signpost/case/parts/COTS_hardware/keystone_1892_0375_#4_standoff.SLDPRT

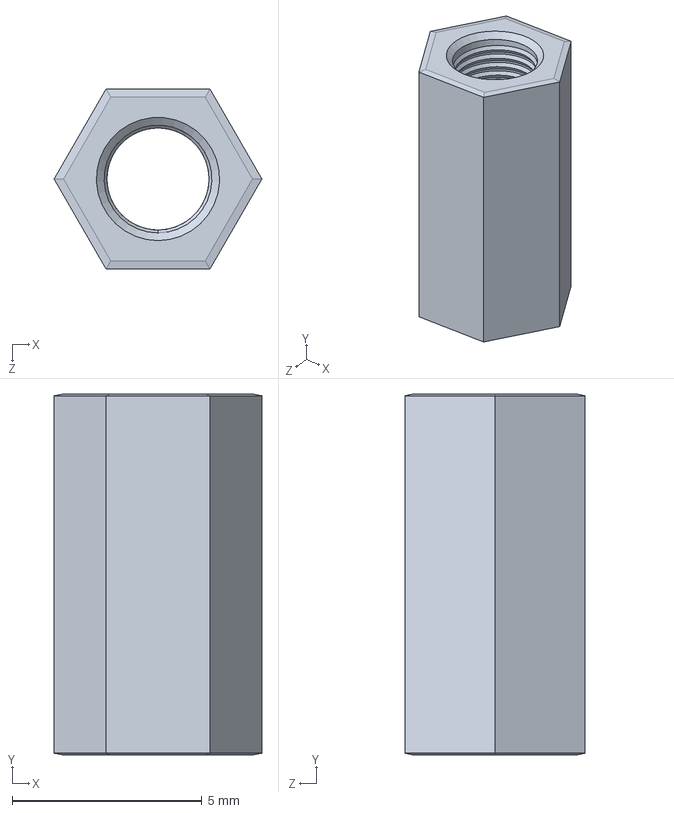
[picture p63: CAD file, 2016-08-08]
case/parts/COTS_hardware/keystone_1892_0375_#4_standoff.SLDPRT
5.48 x 9.53 x 4.75 mm
