lab11/signpost/case/parts/COTS_hardware/8-32_press_in.SLDPRT

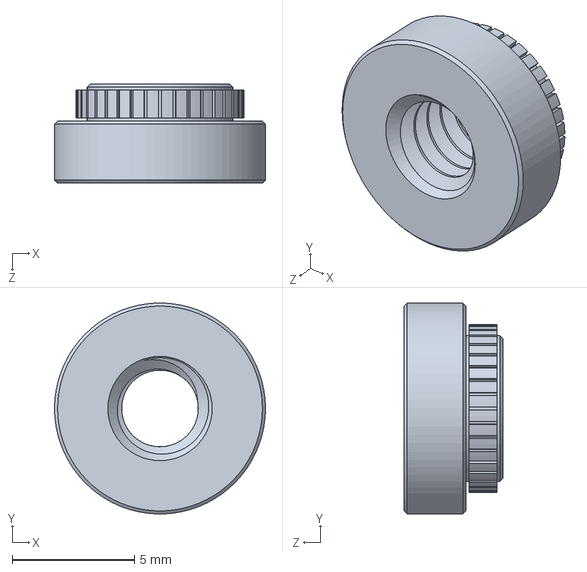
[picture p64: CAD file, 2016-06-20]
case/parts/COTS_hardware/8-32_press_in.SLDPRT
8.64 x 8.63 x 4.06 mm
