lab11/signpost/case/parts/COTS_hardware/10-32_heat_set.SLDPRT

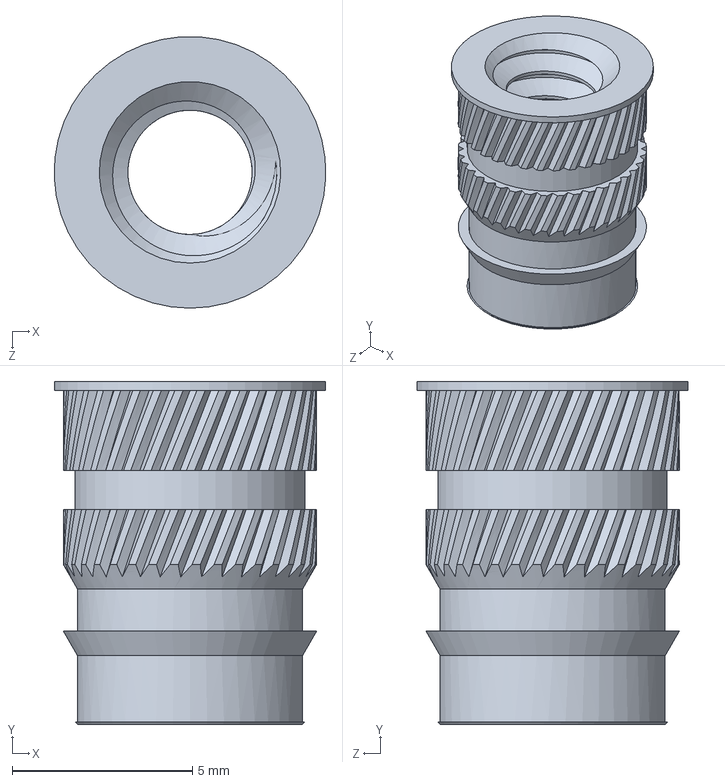
[picture p65: CAD file, 2016-06-20]
case/parts/COTS_hardware/10-32_heat_set.SLDPRT
7.54 x 9.53 x 7.53 mm
