lab11/signpost/modules/spectrum154/ieee802154_grafana_channel11usage.csv

Time | channel_11 | channel_12 | channel_13 | channel_14 | channel_15 | channel_16 | channel_17 | channel_18 | channel_19 | channel_20 | channel_21 | channel_22 | channel_23 | channel_24 | channel_25 | channel_26
2016-08-08T17:42:36.340Z | -95 | -87 | -96 | -96 | -94 | -89 | -83 | -96 | -97 | -102 | -99 | -95 | -95 | -97 | -100 | -100
2016-08-08T17:42:38.987Z | -88 | -83 | -93 | -91 | -95 | -86 | -94 | -94 | -99 | -100 | -98 | -97 | -98 | -97 | -100 | -98
2016-08-08T17:42:41.636Z | -95 | -51 | -51 | -94 | -97 | -100 | -98 | -98 | -95 | -102 | -98 | -100 | -100 | -100 | -101 | -100
2016-08-08T17:42:44.284Z | -95 | -94 | -90 | -93 | -94 | -98 | -97 | -91 | -99 | -102 | -94 | -94 | -98 | -101 | -99 | -99
2016-08-08T17:42:46.932Z | -98 | -93 | -89 | -96 | -90 | -94 | -89 | -94 | -98 | -100 | -99 | -96 | -94 | -99 | -101 | -96
2016-08-08T17:42:49.581Z | -94 | -86 | -90 | -86 | -98 | -85 | -97 | -98 | -91 | -97 | -99 | -99 | -96 | -94 | -100 | -99
2016-08-08T17:42:52.229Z | -94 | -90 | -95 | -99 | -95 | -94 | -99 | -100 | -101 | -100 | -97 | -98 | -99 | -102 | -100 | -98
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
