lab11/signpost/modules/spectrum154/ieee802154_grafana_channel11usage.jpg

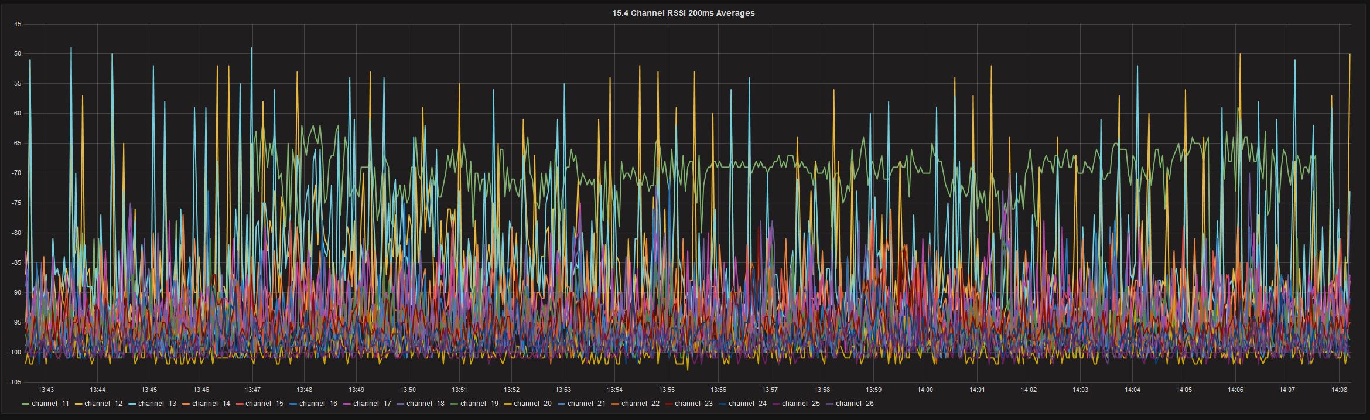
modules/spectrum154/ieee802154_grafana_channel11usage.jpg
