lab11/signpost/test/edison_crypto_test/data/raw/ecdsa_384/ECDHE-ECDSA-AES128-GCM-SHA256.CSV

Model | DPO2024B
Firmware Version | 1.56
Point Format | Y
Horizontal Units | S
Horizontal Scale | 1
Sample Interval | 8e-05
Filter Frequency | 2e+08
Record Length | 125000
Gating | 0.0% to 100.0%
Probe Attenuation | 10
Vertical Units | V
Vertical Offset | 0
Vertical Scale | 0.5
Label
TIME | CH1 | CH1 Peak Detect
-5.00000e+00 | 0.32 | 0.38
-4.99992e+00 | 0.32 | 0.26
-4.99984e+00 | 0.28 | 0.4
-4.99976e+00 | 0.3 | 0.26
-4.99968e+00 | 0.3 | 0.38
-4.99960e+00 | 0.32 | 0.26
-4.99952e+00 | 0.3 | 0.36
-4.99944e+00 | 0.3 | 0.24
-4.99936e+00 | 0.3 | 0.36
-4.99928e+00 | 0.3 | 0.24
-4.99920e+00 | 0.32 | 0.38
-4.99912e+00 | 0.3 | 0.24
-4.99904e+00 | 0.32 | 0.36
-4.99896e+00 | 0.32 | 0.24
-4.99888e+00 | 0.32 | 0.38
-4.99880e+00 | 0.32 | 0.24
-4.99872e+00 | 0.36 | 0.36
-4.99864e+00 | 0.34 | 0.26
-4.99856e+00 | 0.3 | 0.4
-4.99848e+00 | 0.3 | 0.26
-4.99840e+00 | 0.34 | 0.4
-4.99832e+00 | 0.32 | 0.26
-4.99824e+00 | 0.3 | 0.38
-4.99816e+00 | 0.34 | 0.26
-4.99808e+00 | 0.34 | 0.4
-4.99800e+00 | 0.3 | 0.24
-4.99792e+00 | 0.3 | 0.38
-4.99784e+00 | 0.32 | 0.26
-4.99776e+00 | 0.32 | 0.4
-4.99768e+00 | 0.32 | 0.26
-4.99760e+00 | 0.36 | 0.38
-4.99752e+00 | 0.32 | 0.26
-4.99744e+00 | 0.32 | 0.4
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
