lab11/signpost/media/module_debug_pcb_dim.PNG

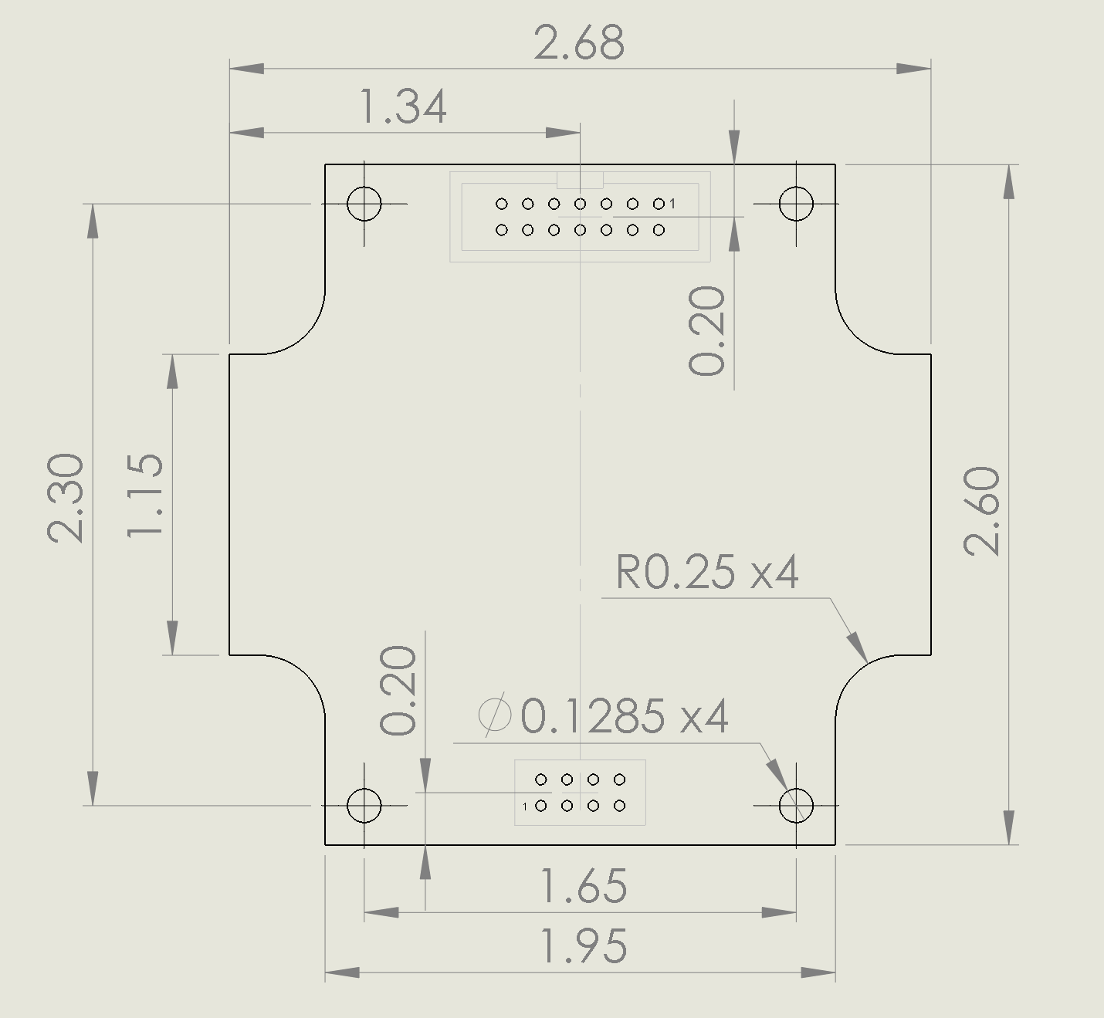
media/module_debug_pcb_dim.PNG
