lab11/signpost/test/solar_panel_test/data/plots/6-15-2016-6-15-2016-16deg-south.pdf

8 06/15

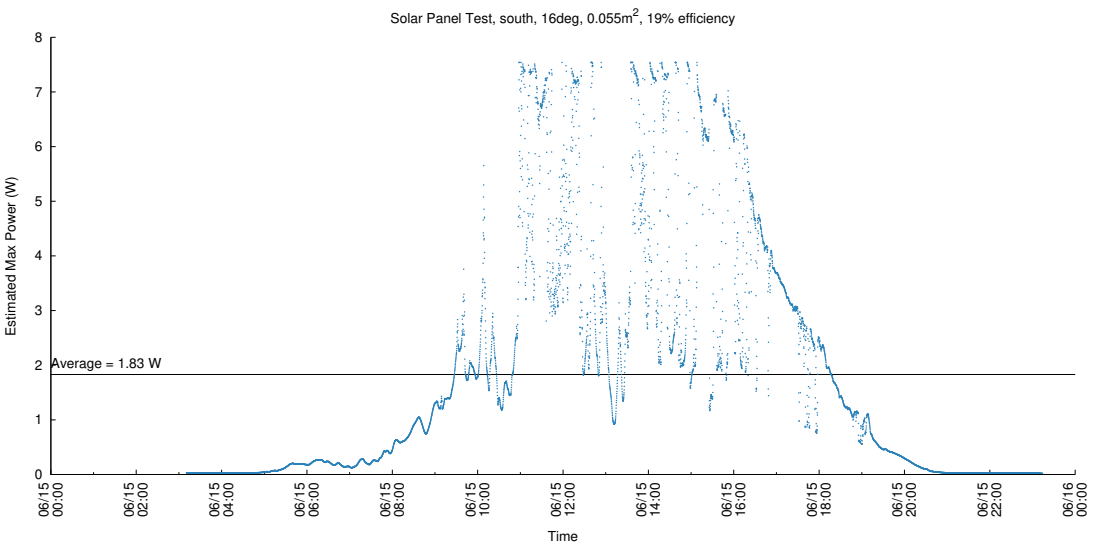
[picture p115: page 1]
Average = 1.83 W; Time; , 19% efficiency

Solar Panel Test, south, 16deg, 0.055m²

Estimated Max Power (W)
