lab11/signpost/test/solar_panel_test/data/plots/6-16-2016-6-16-2016-vertical-east.pdf

7 06/16

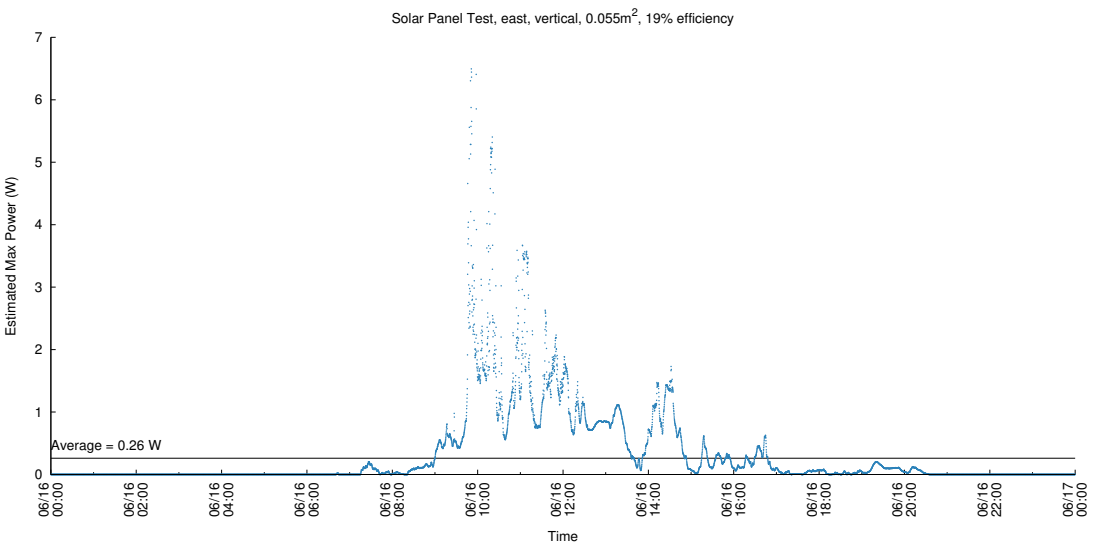
[picture p116: page 1]
Average = 0.26 W; Time; , 19% efficiency

Solar Panel Test, east, vertical, 0.055m²

Estimated Max Power (W)
