lab11/signpost/test/solar_panel_test/data/plots/6-16-2016-6-16-2016-vertical-south.pdf

3 06/16

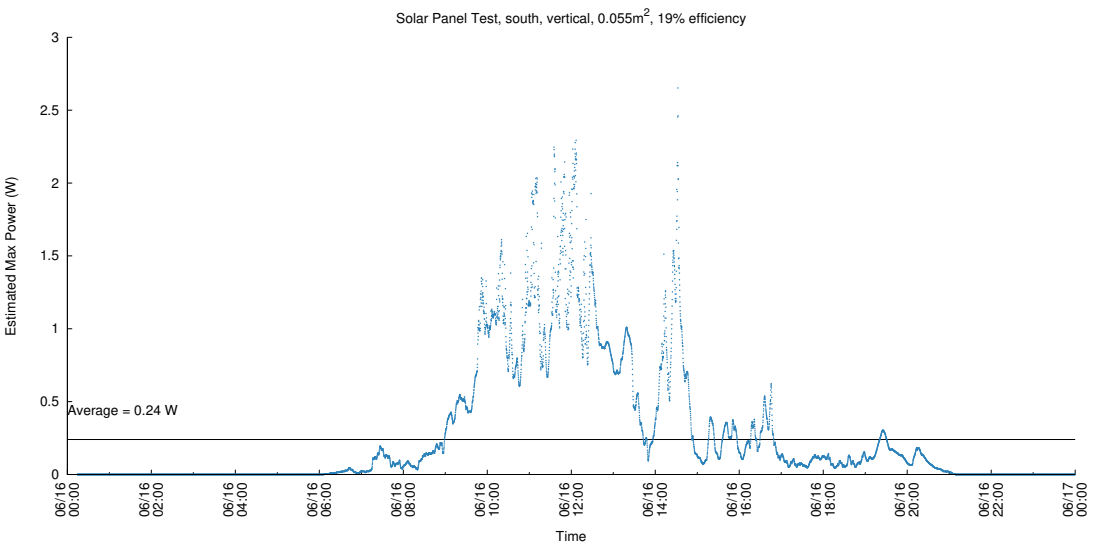
[picture p117: page 1]
Average = 0.24 W; Time; , 19% efficiency

Solar Panel Test, south, vertical, 0.055m²

Estimated Max Power (W)
