lab11/signpost/test/solar_panel_test/data/plots/6-16-2016-6-16-2016-vertical-west.pdf

2.5 06/16

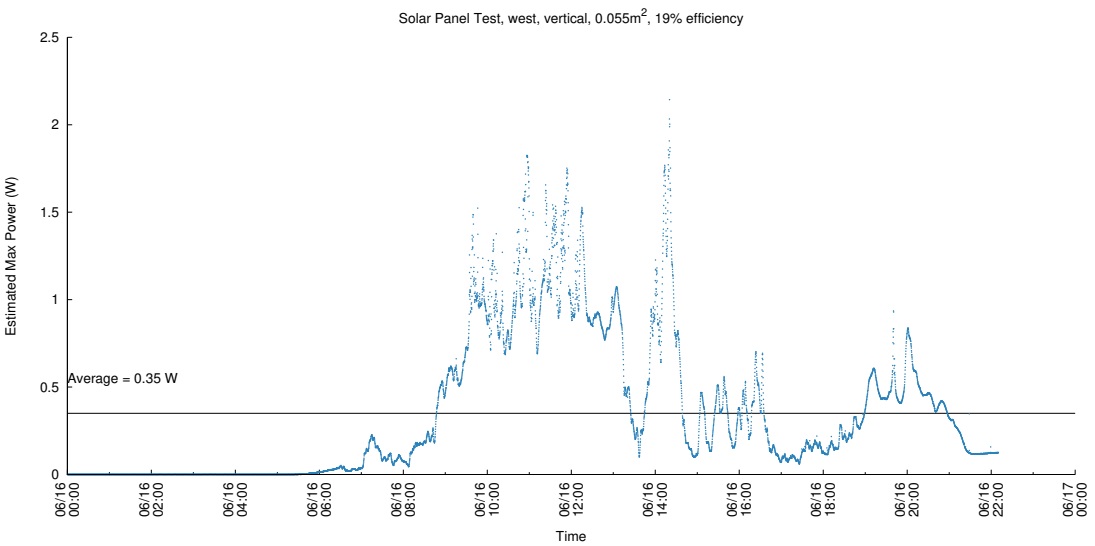
[picture p118: page 1]
Average = 0.35 W; Time; , 19% efficiency

Solar Panel Test, west, vertical, 0.055m²

Estimated Max Power (W)
