lab11/signpost/test/solar_panel_test/data/plots/6-23-2016-6-24-2016-vertical-west.pdf

6 06/23

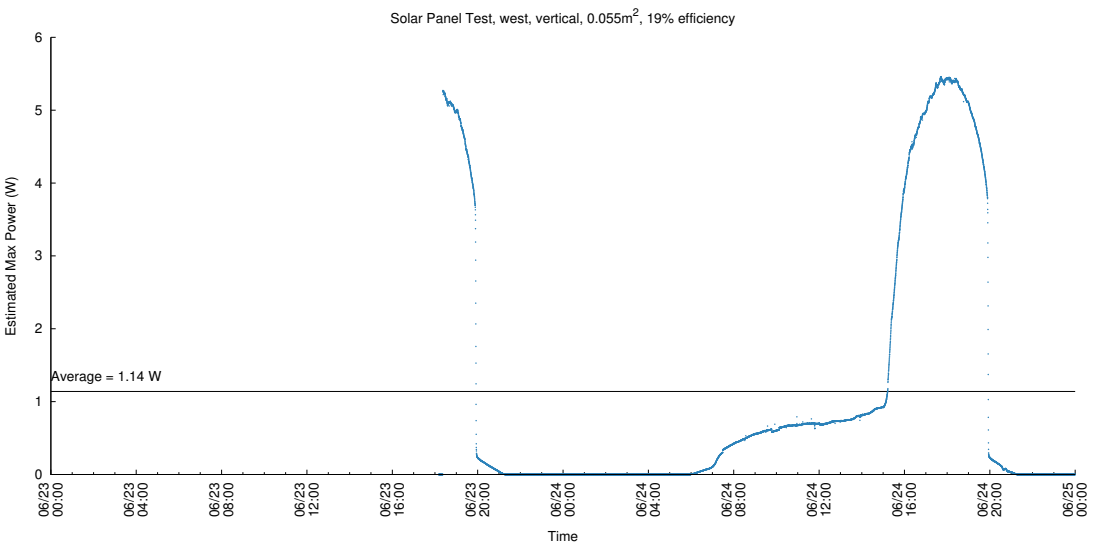
[picture p119: page 1]
Average = 1.14 W; Time; , 19% efficiency

Solar Panel Test, west, vertical, 0.055m²

Estimated Max Power (W)
