lab11/signpost/test/solar_panel_test/data/plots/6-24-2016-6-24-2016-vertical-east.pdf

6 06/24

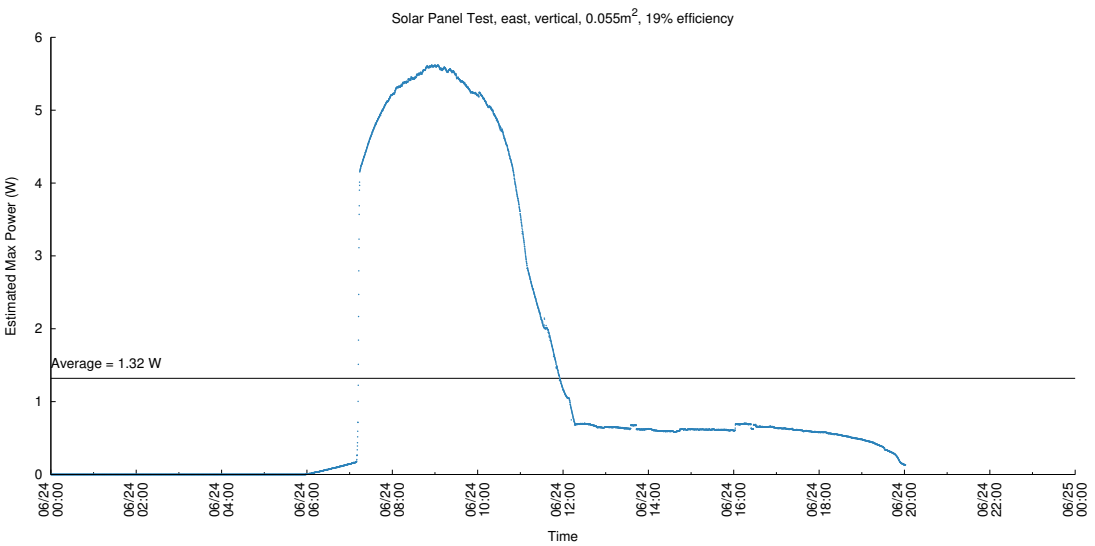
[picture p120: page 1]
Average = 1.32 W; Time; , 19% efficiency

Solar Panel Test, east, vertical, 0.055m²

Estimated Max Power (W)
