lab11/signpost/test/solar_panel_test/data/plots/6-29-2016-6-30-2016-vertical-south.pdf

2.5 06/29

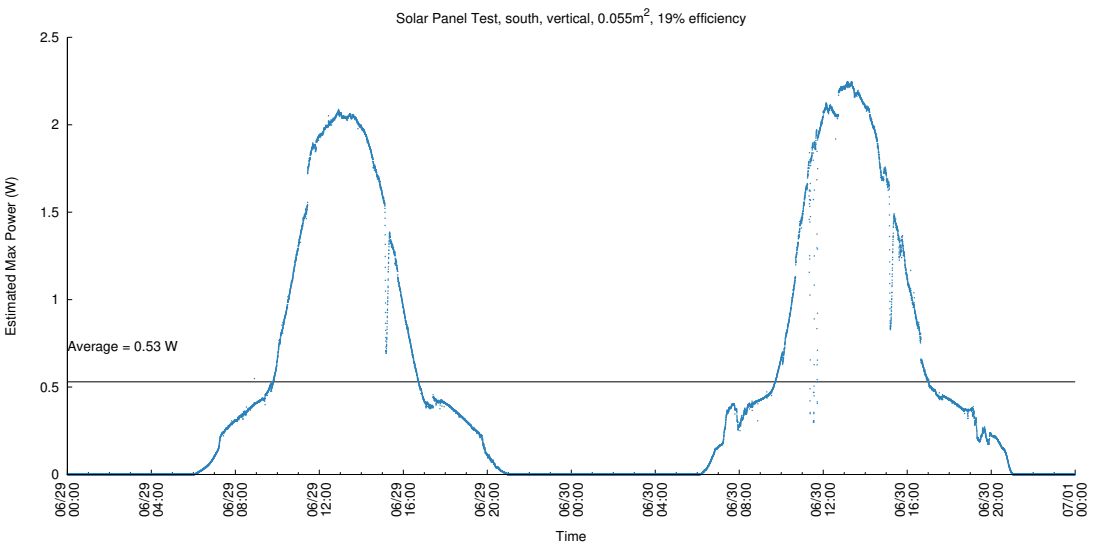
[picture p121: page 1]
Average = 0.53 W; Time; , 19% efficiency

Solar Panel Test, south, vertical, 0.055m²

Estimated Max Power (W)
