lab11/signpost/case/parts/For_UM_Machine_Shop/back_panel_cover/2D/back_panel_cover.PDF

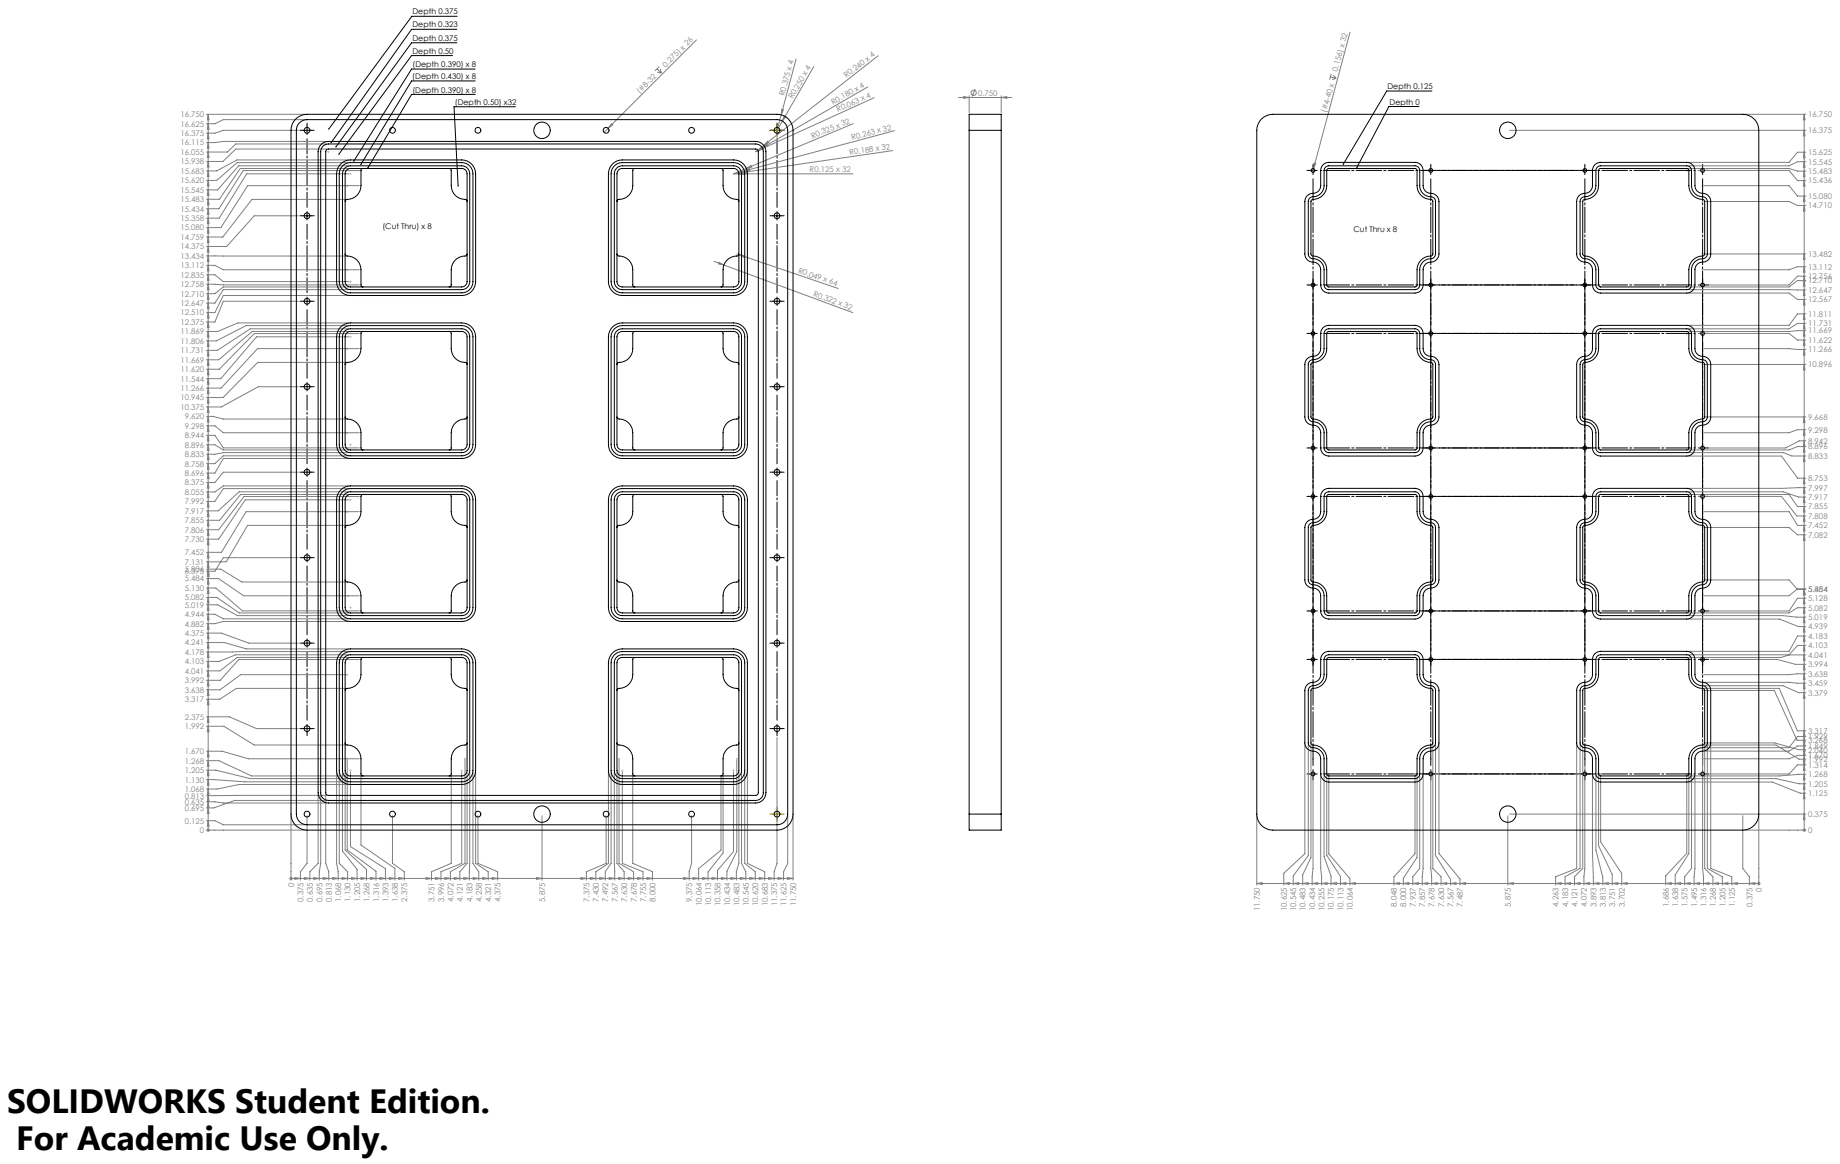
[picture p122: page 1]
Depth 0.375 Depth 0.323 Depth 0.375 Depth 0.50 (Depth 0.390) x 8 (Depth 0.430) x 8 (Depth 0.390) x 8 (Depth 0.50) x32; (Cut Thru) x 8; Depth 0.125 Depth 0; Cut Thru x 8

SOLIDWORKS Student Edition.
For Academic Use Only.
