lab11/signpost/case/parts/For_UM_Machine_Shop/solar_mount/2D/solar_mount.PDF

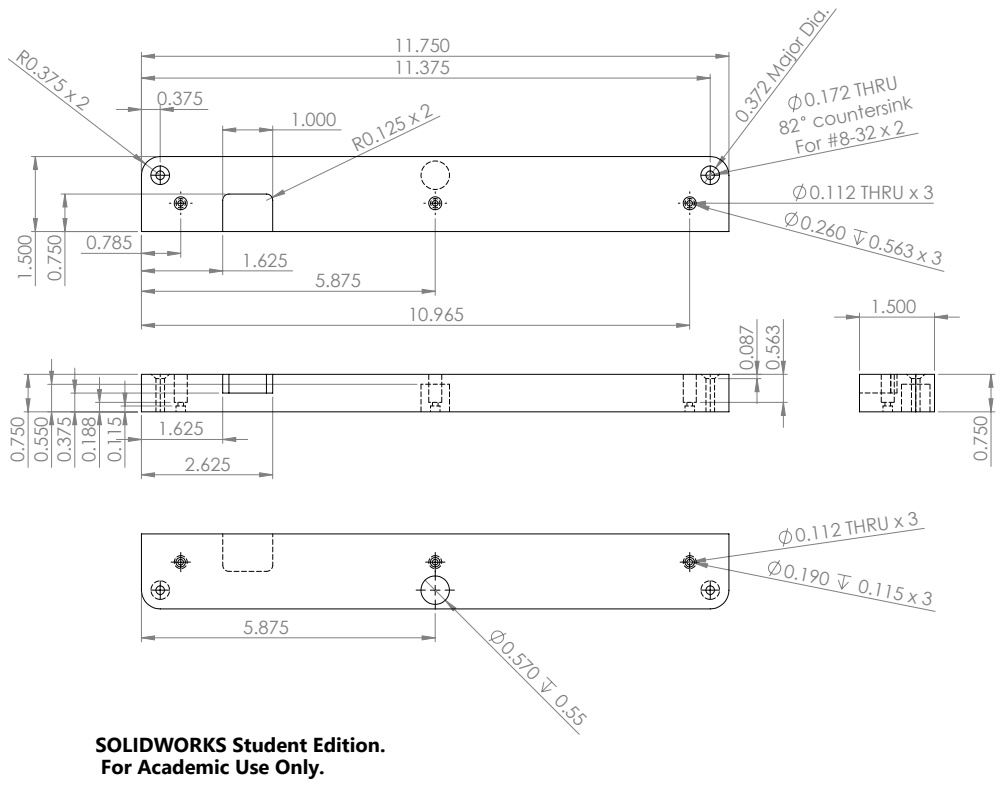
[picture p129: page 1]
0.112 THRU x 3 0.260 0.563 x 3; 0.172 THRU 82 countersink For #8-32 x 2; 0.372 Major Dia.; 0.112 THRU x 3

SOLIDWORKS Student Edition.
For Academic Use Only.
