lab11/signpost/case/parts/For_UM_Machine_Shop/back_panel/2D/back_panel.PDF

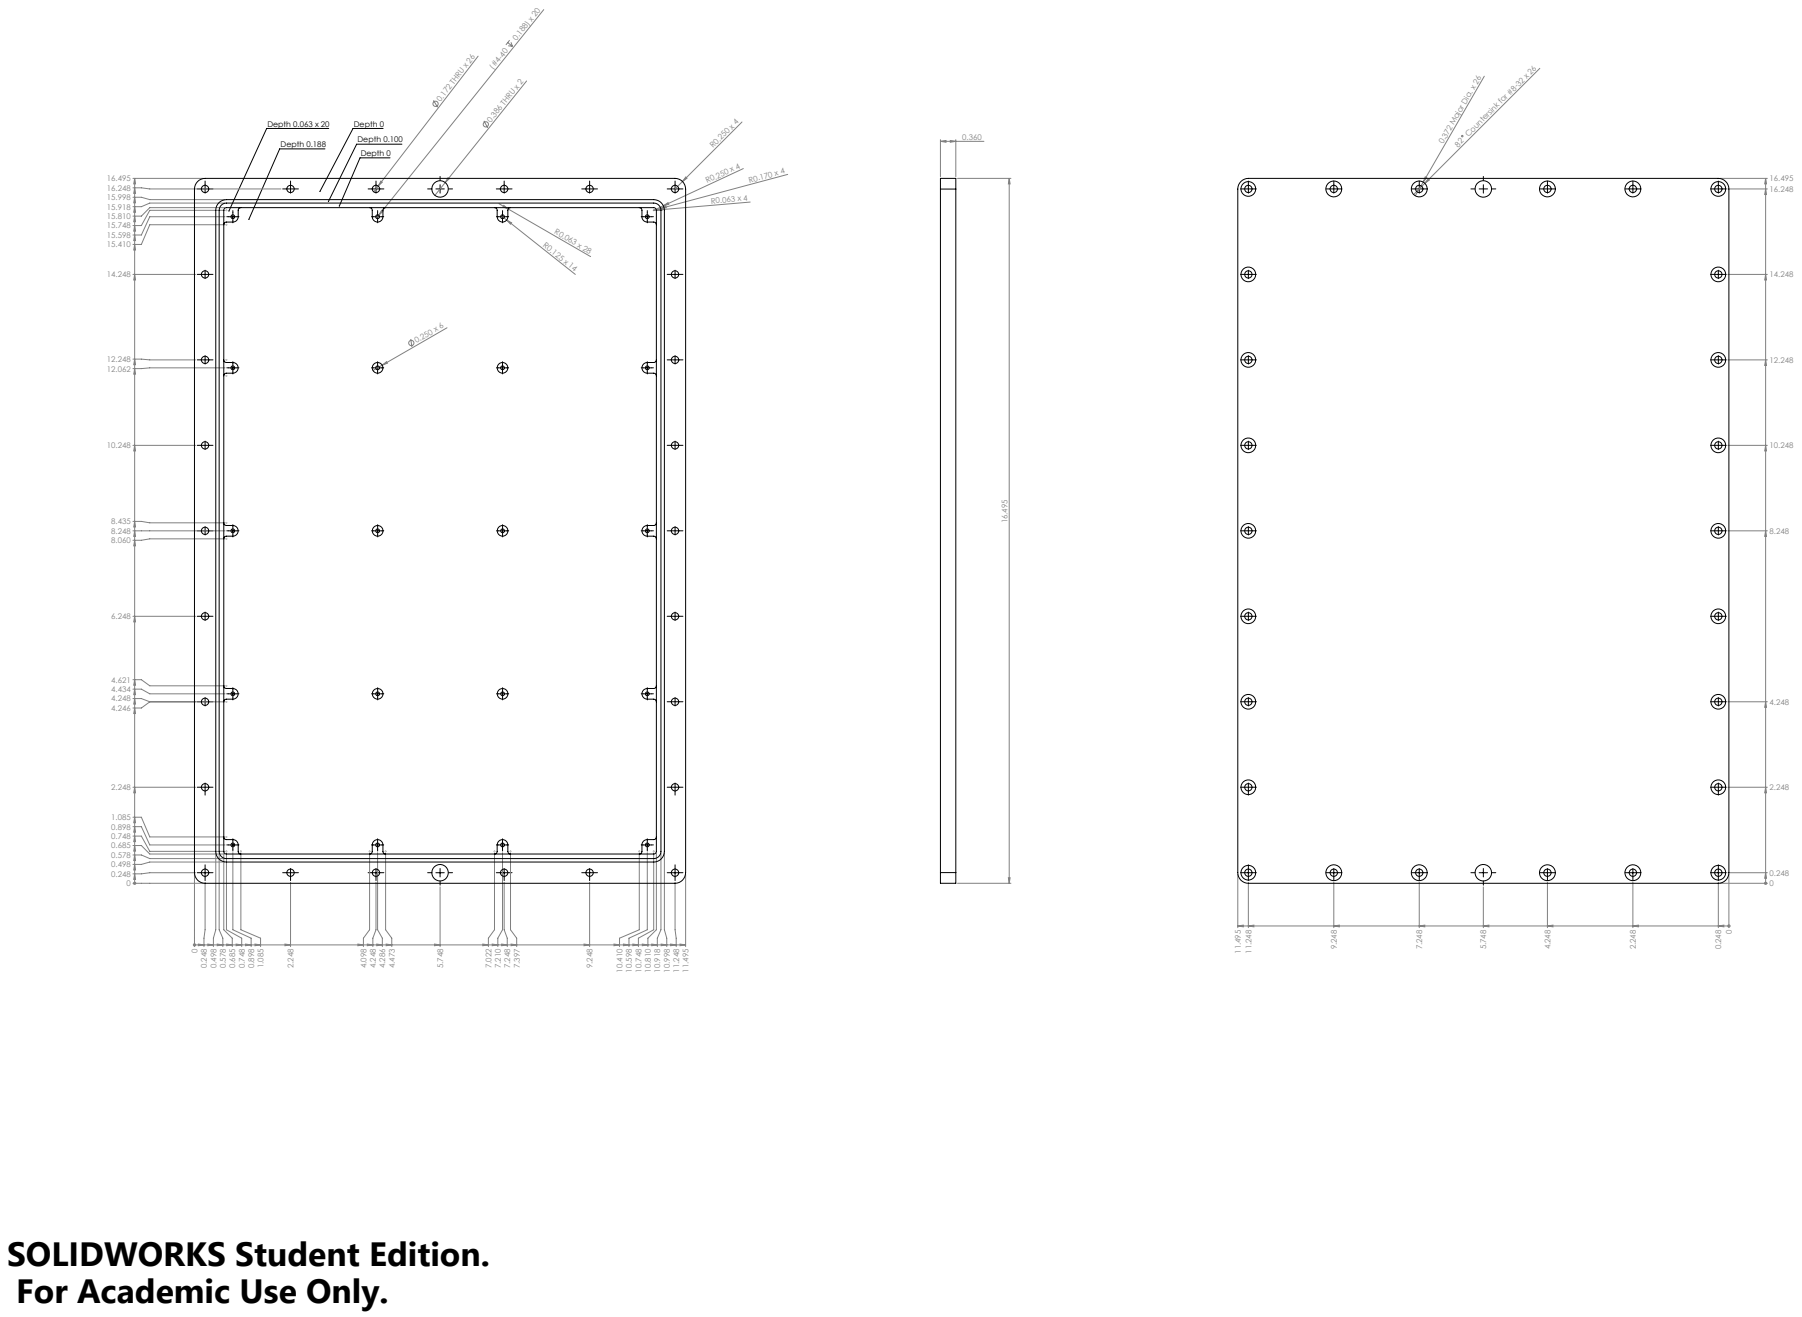
[picture p130: page 1]
0.386 THRU x 2; 0.172 THRU x 26; Depth 0 Depth 0.100 Depth 0; Depth 0.063 x 20; Depth 0.188; 82 Countersink for #8-32 x 26 0.372 Major Dia. x 26

SOLIDWORKS Student Edition.
For Academic Use Only.
