lab11/signpost/modules/ambient/rev_d/pdfs/board.pdf

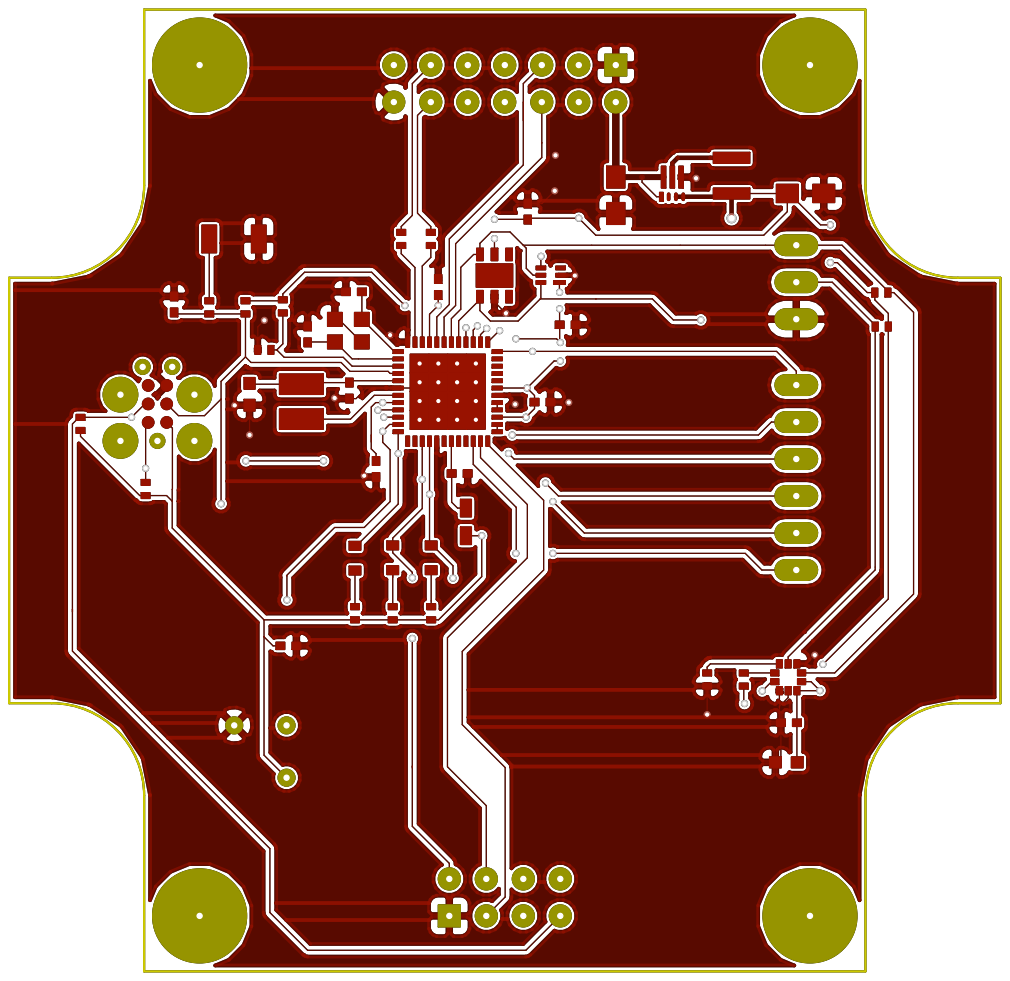
[picture p131: page 1]

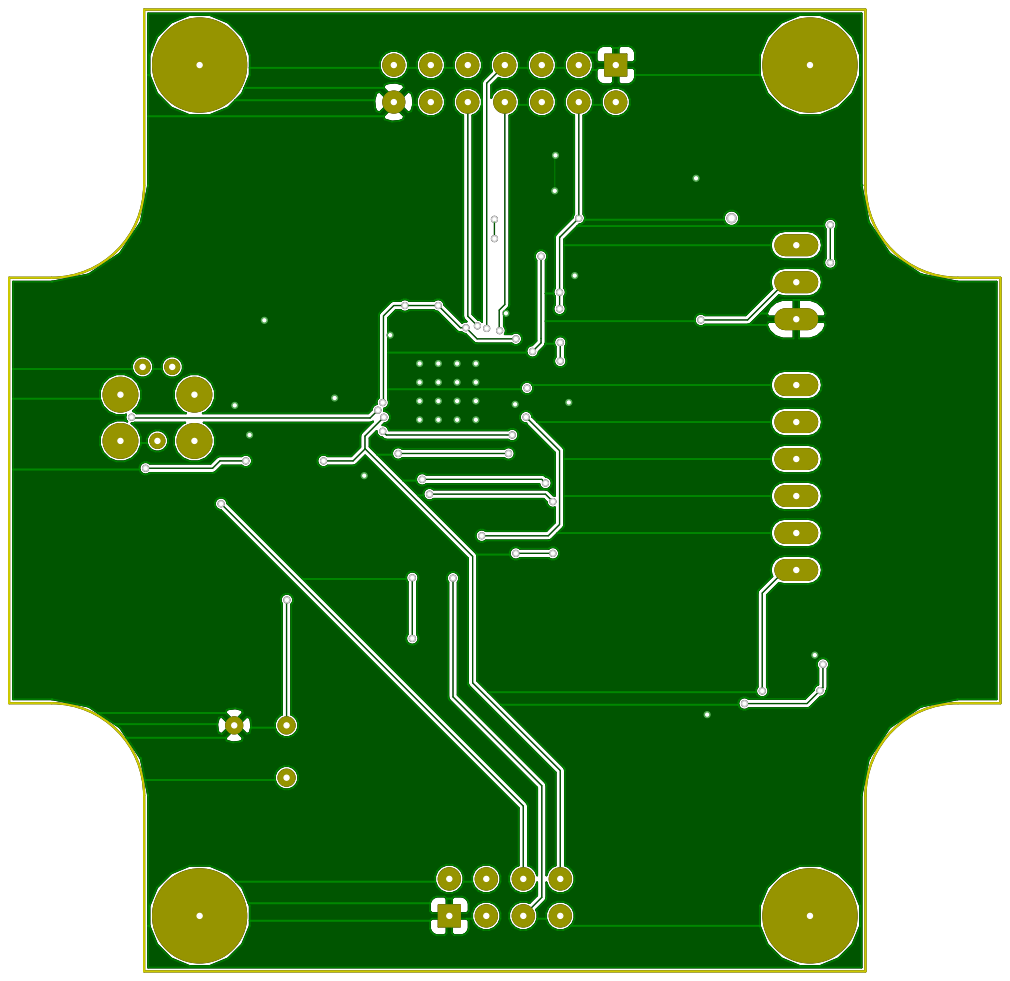
[picture p132: page 2]

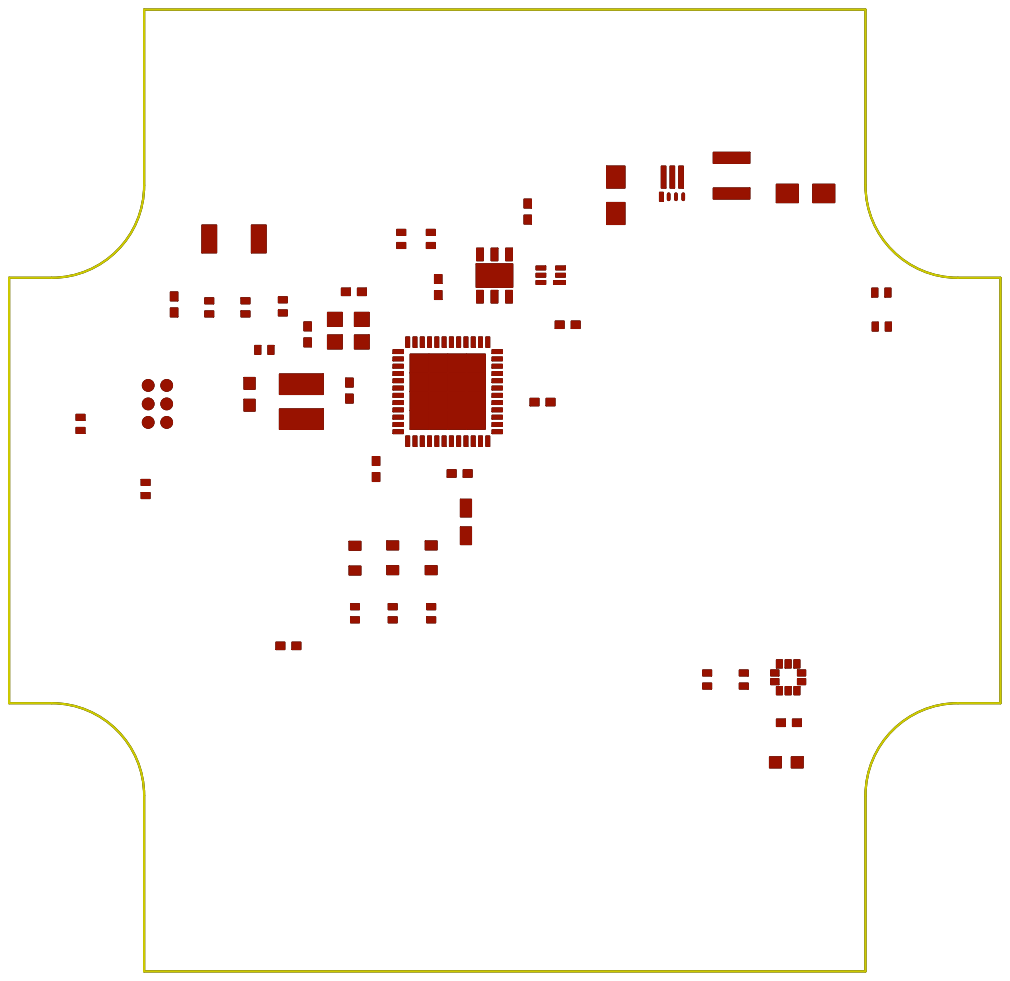
[picture p133: page 3]

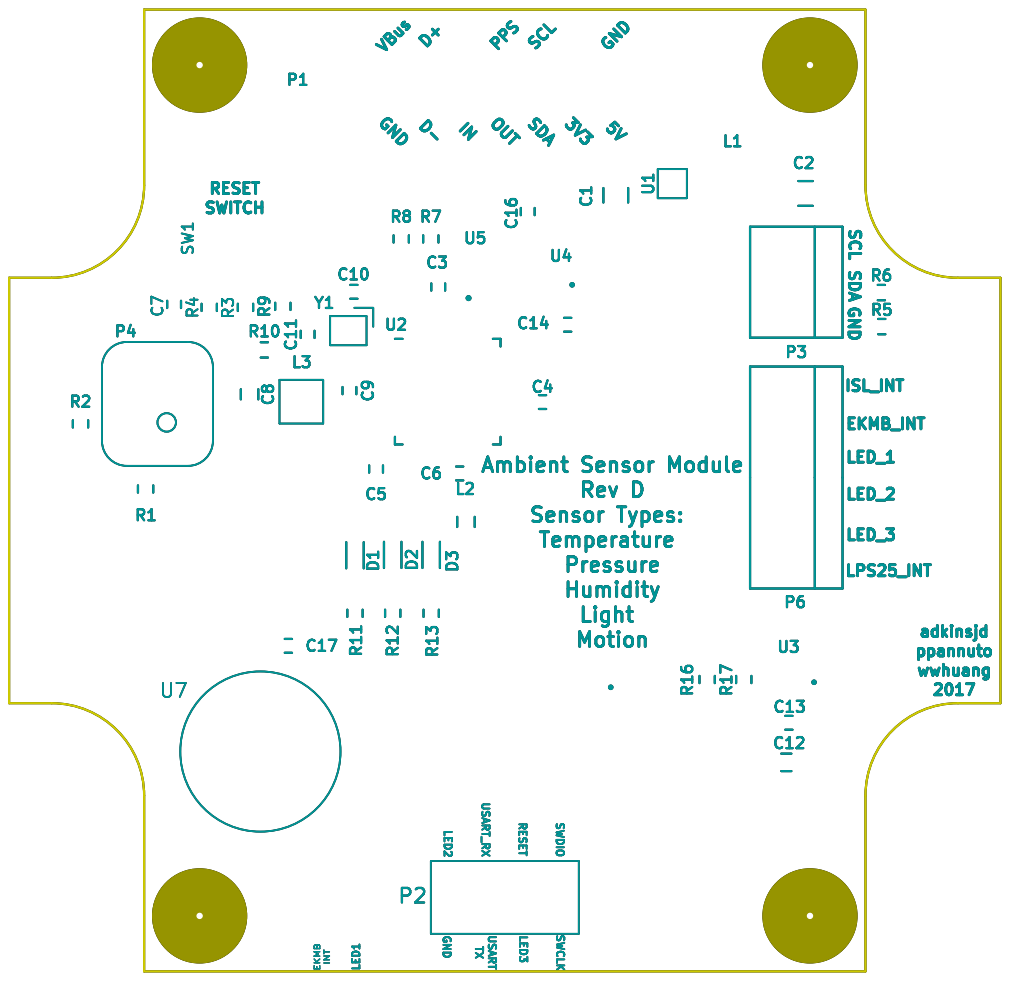
[picture p134: page 4]

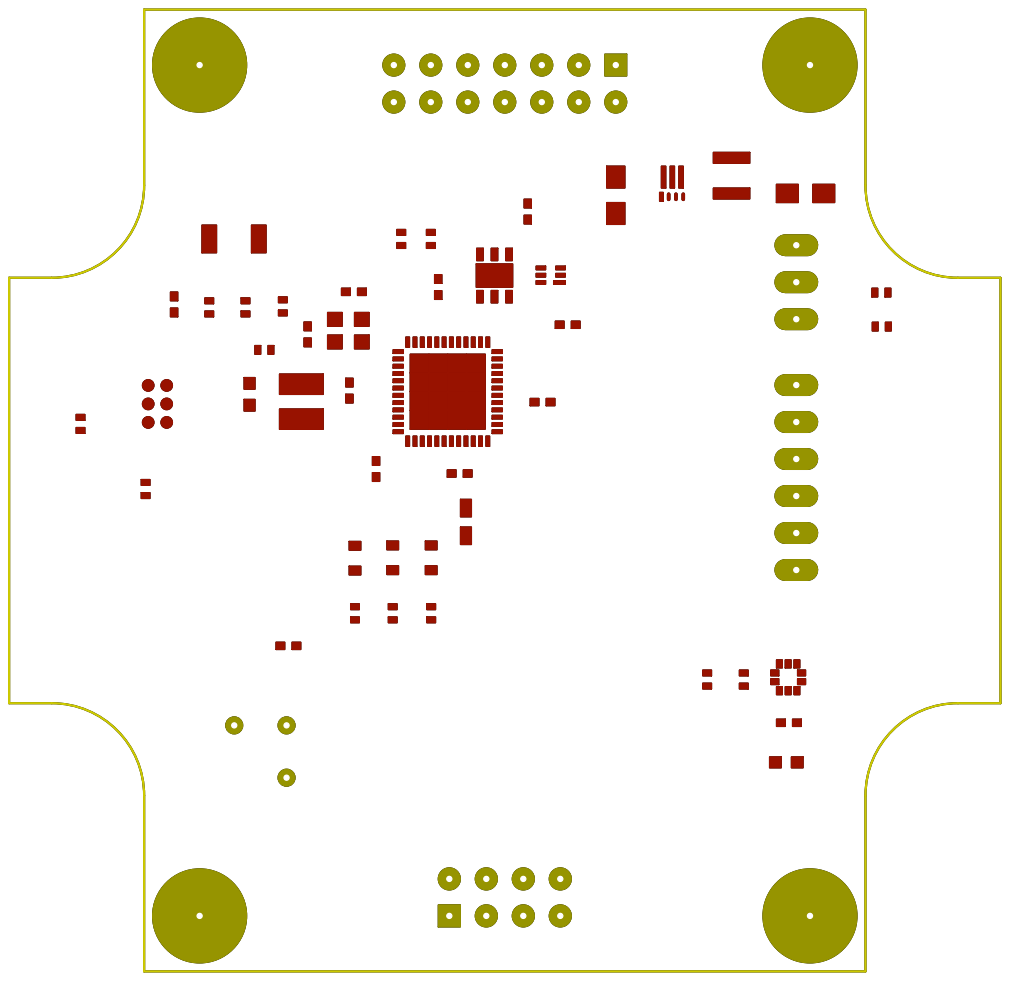
[picture p135: page 5]

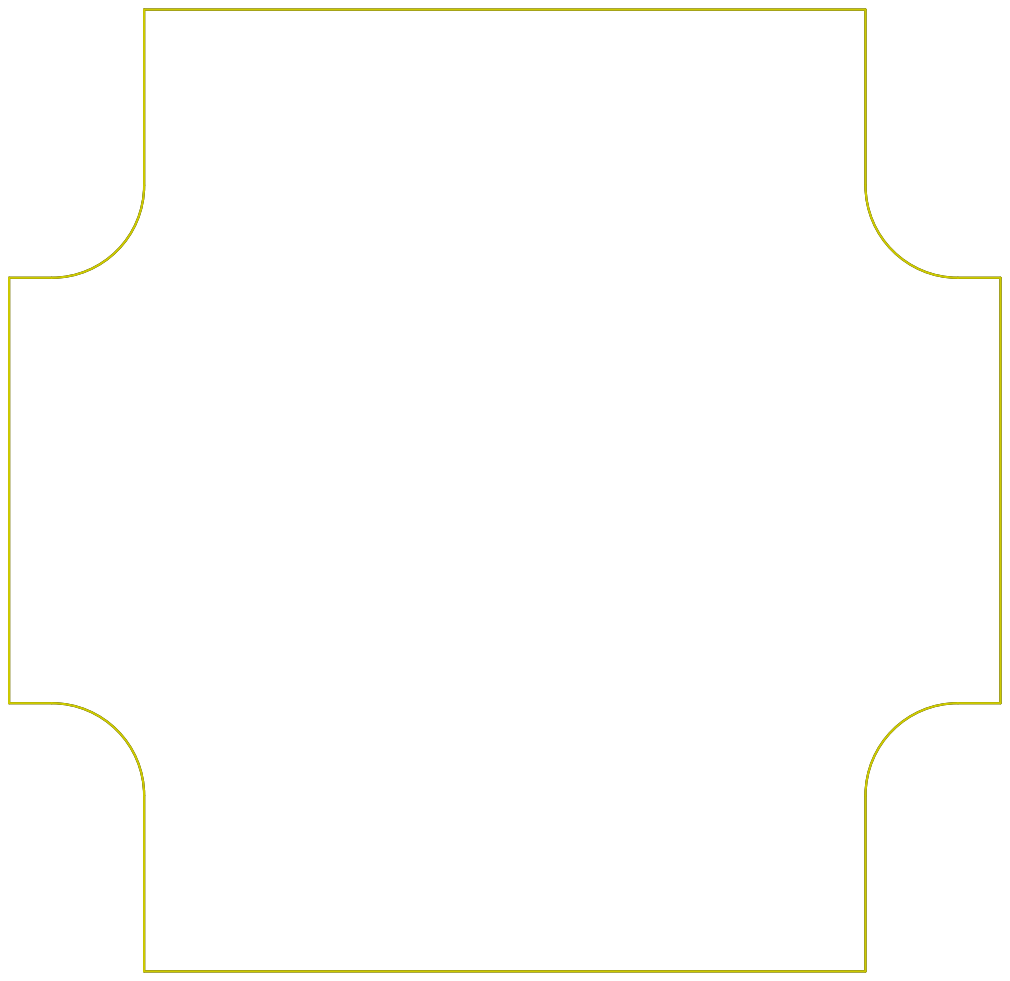
[picture p136: page 6]
