lab11/signpost/hardware/debug_backplane/rev_c/quotes/Quickturn U&I.pdf

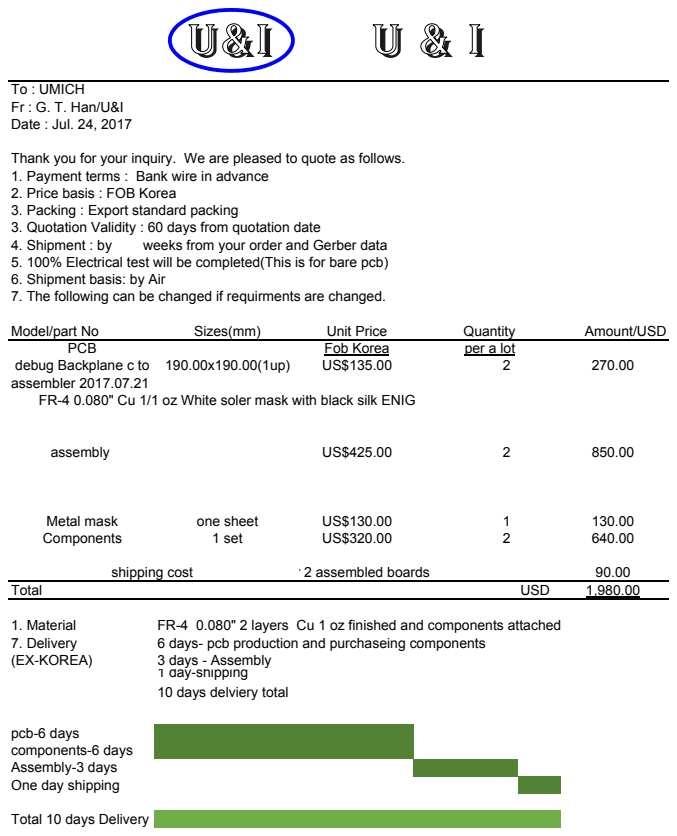
[picture p137: page 1]
To : UMICH Fr : G. T. Han/U&I Date : Jul. 24, 2017; 4. Shipment : by; weeks from your order and Gerber data; Model/part No; Sizes(mm); Unit Price; Quantity; Amount/USD; PCB; Fob Korea; per a lot; debug Backplane c to 190.00x190.00(1up); assembly; Metal mask; one sheet; Components; 1 set; for 2 assembled boards; Total; USD; 1. Material 7. Delivery; (EX-KOREA); 3 days - Assembly; shipping cost

Thank you for your inquiry. We are pleased to quote as follows.
1. Payment terms : Bank wire in advance
2. Price basis : FOB Korea
3. Packing : Export standard packing
3. Quotation Validity : 60 days from quotation date
5. 100% Electrical test will be completed(This is for bare pcb)
6. Shipment basis: by Air
7. The following can be changed if requirments are changed.

assembler 2017.07.21
FR-4 0.080" Cu 1/1 oz White soler mask with black silk ENIG

FR-4 0.080" 2 layers Cu 1 oz finished and components attached
6 days- pcb production and purchaseing components

1 day-shipping
10 days delviery total

pcb-6 days
components-6 days
Assembly-3 days
One day shipping

Total 10 days Delivery
