lab11/signpost/hardware/power_supply_module/rev_e/power_supply_module.pdf

# Power Module Header

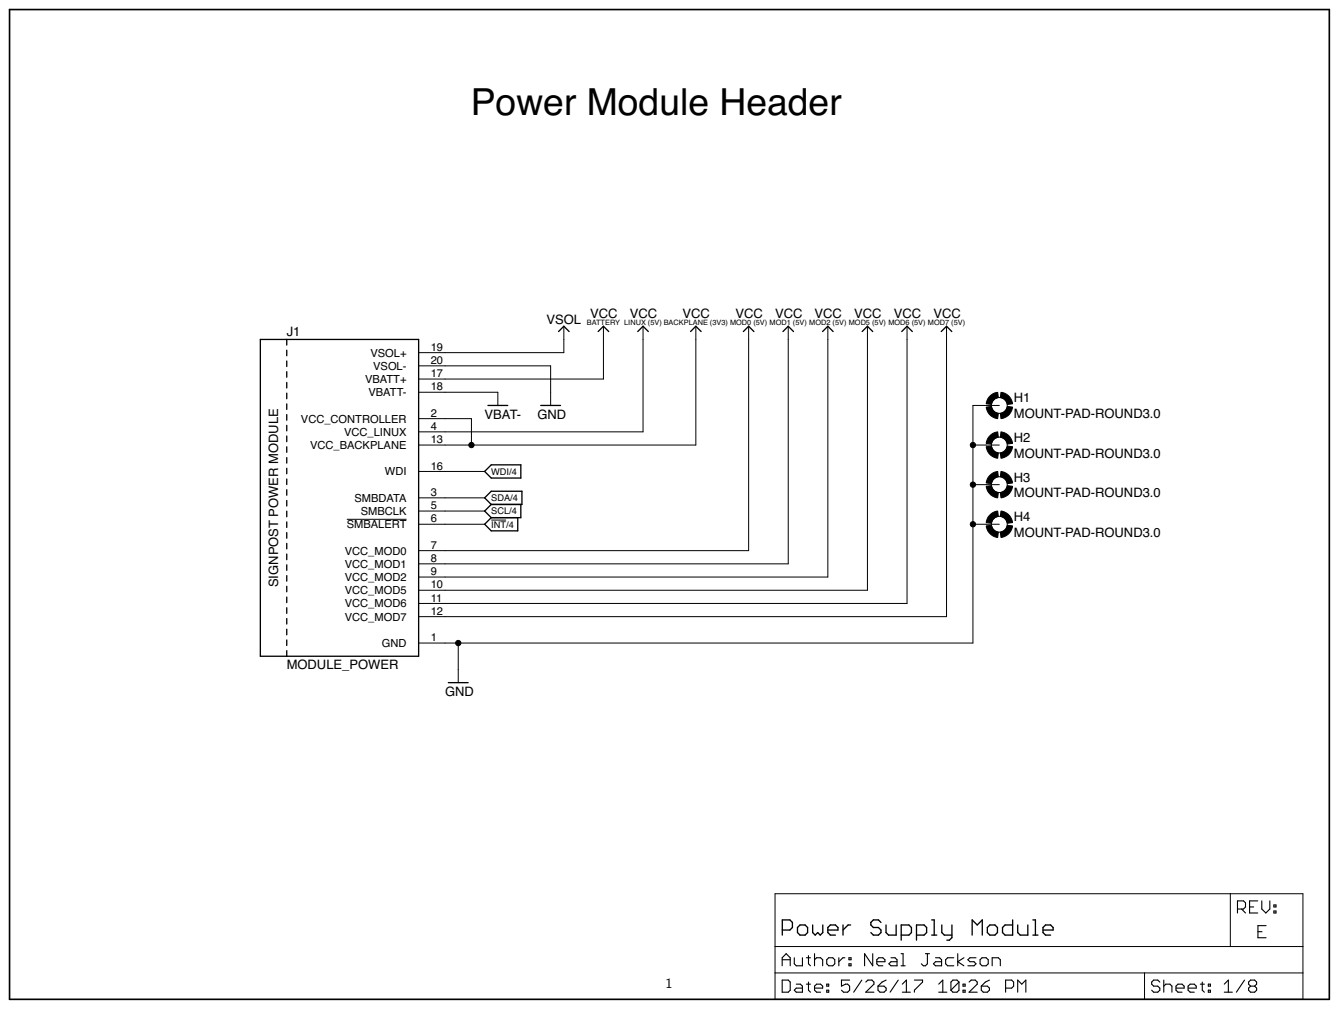
[picture p138: page 1]
SIGNPOST PO; WER M; ODULE; GND; MODULE_POWER; MOUNT-PAD-ROUND3.0; VBAT-; VSOL+; 19 VSOL-; 20 VBATT+; 17 VBATT-; VCC_CONTROLLER; 2 VCC_LINUX 4 VCC_BACKPLANE 13 SMBDATA; 3 SMBCLK 5 SMBALERT 6 VCC_MOD0; 7 VCC_MOD1 8 VCC_MOD2 9 VCC_MOD5 10 VCC_MOD6 11 VCC_MOD7 12; WDI; VCC MOD0 (5V) VCC MOD1 (5V) VCC MOD2 (5V) VCC MOD5 (5V) VCC MOD6 (5V) VCC VSOL; MOD7 (5V) VCC BATTERY; VCC BACKPLANE (3V3) VCC LINUX (5V); SDA/4 SCL/4; INT/4 WDI/4

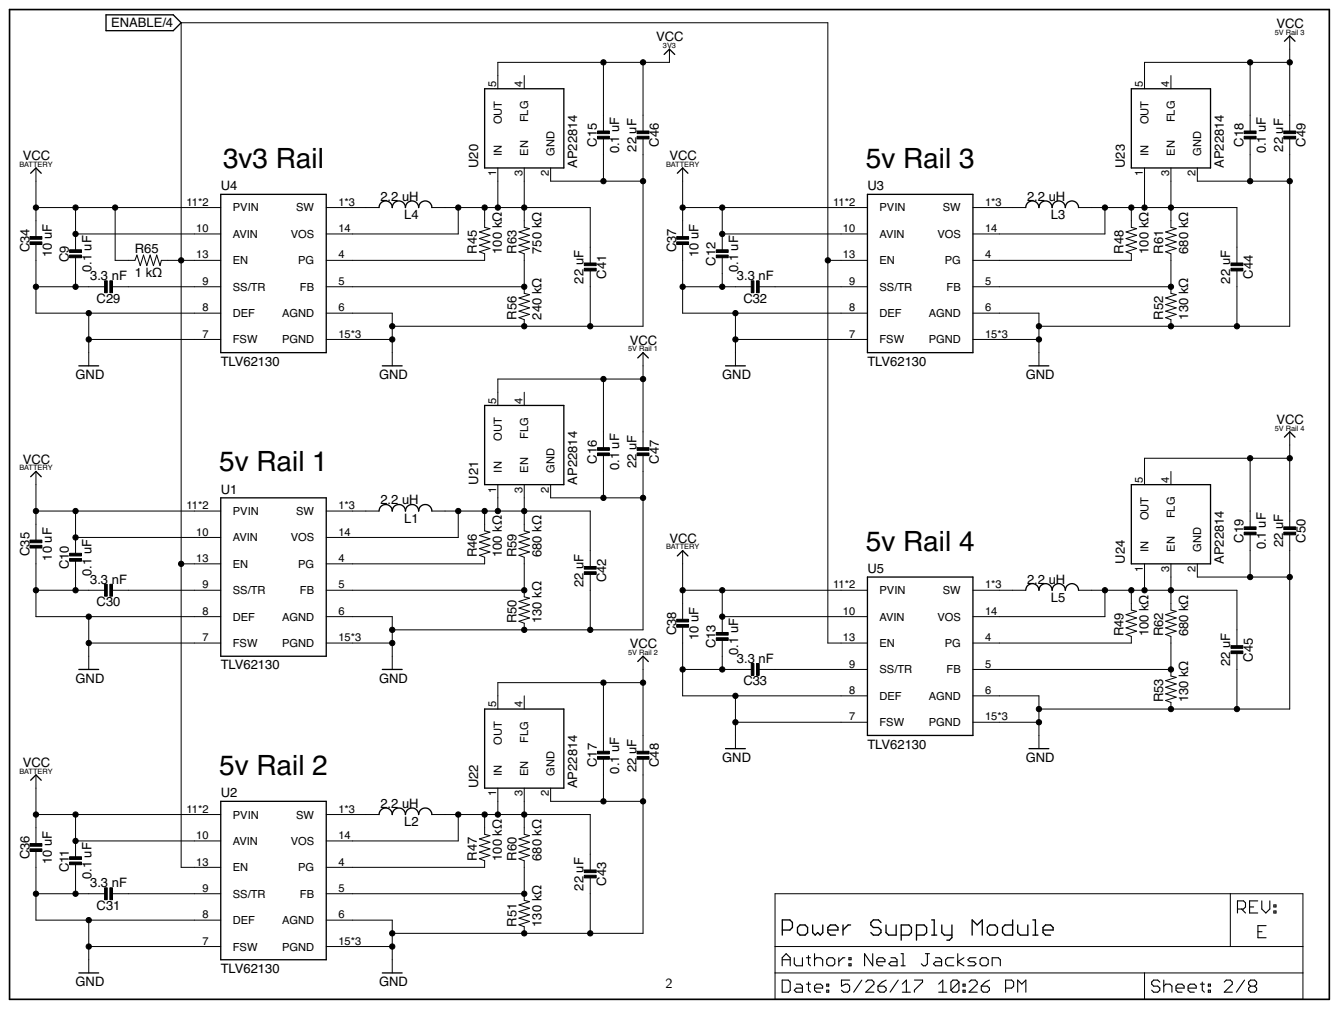
[picture p139: page 2]

# Solar Charger

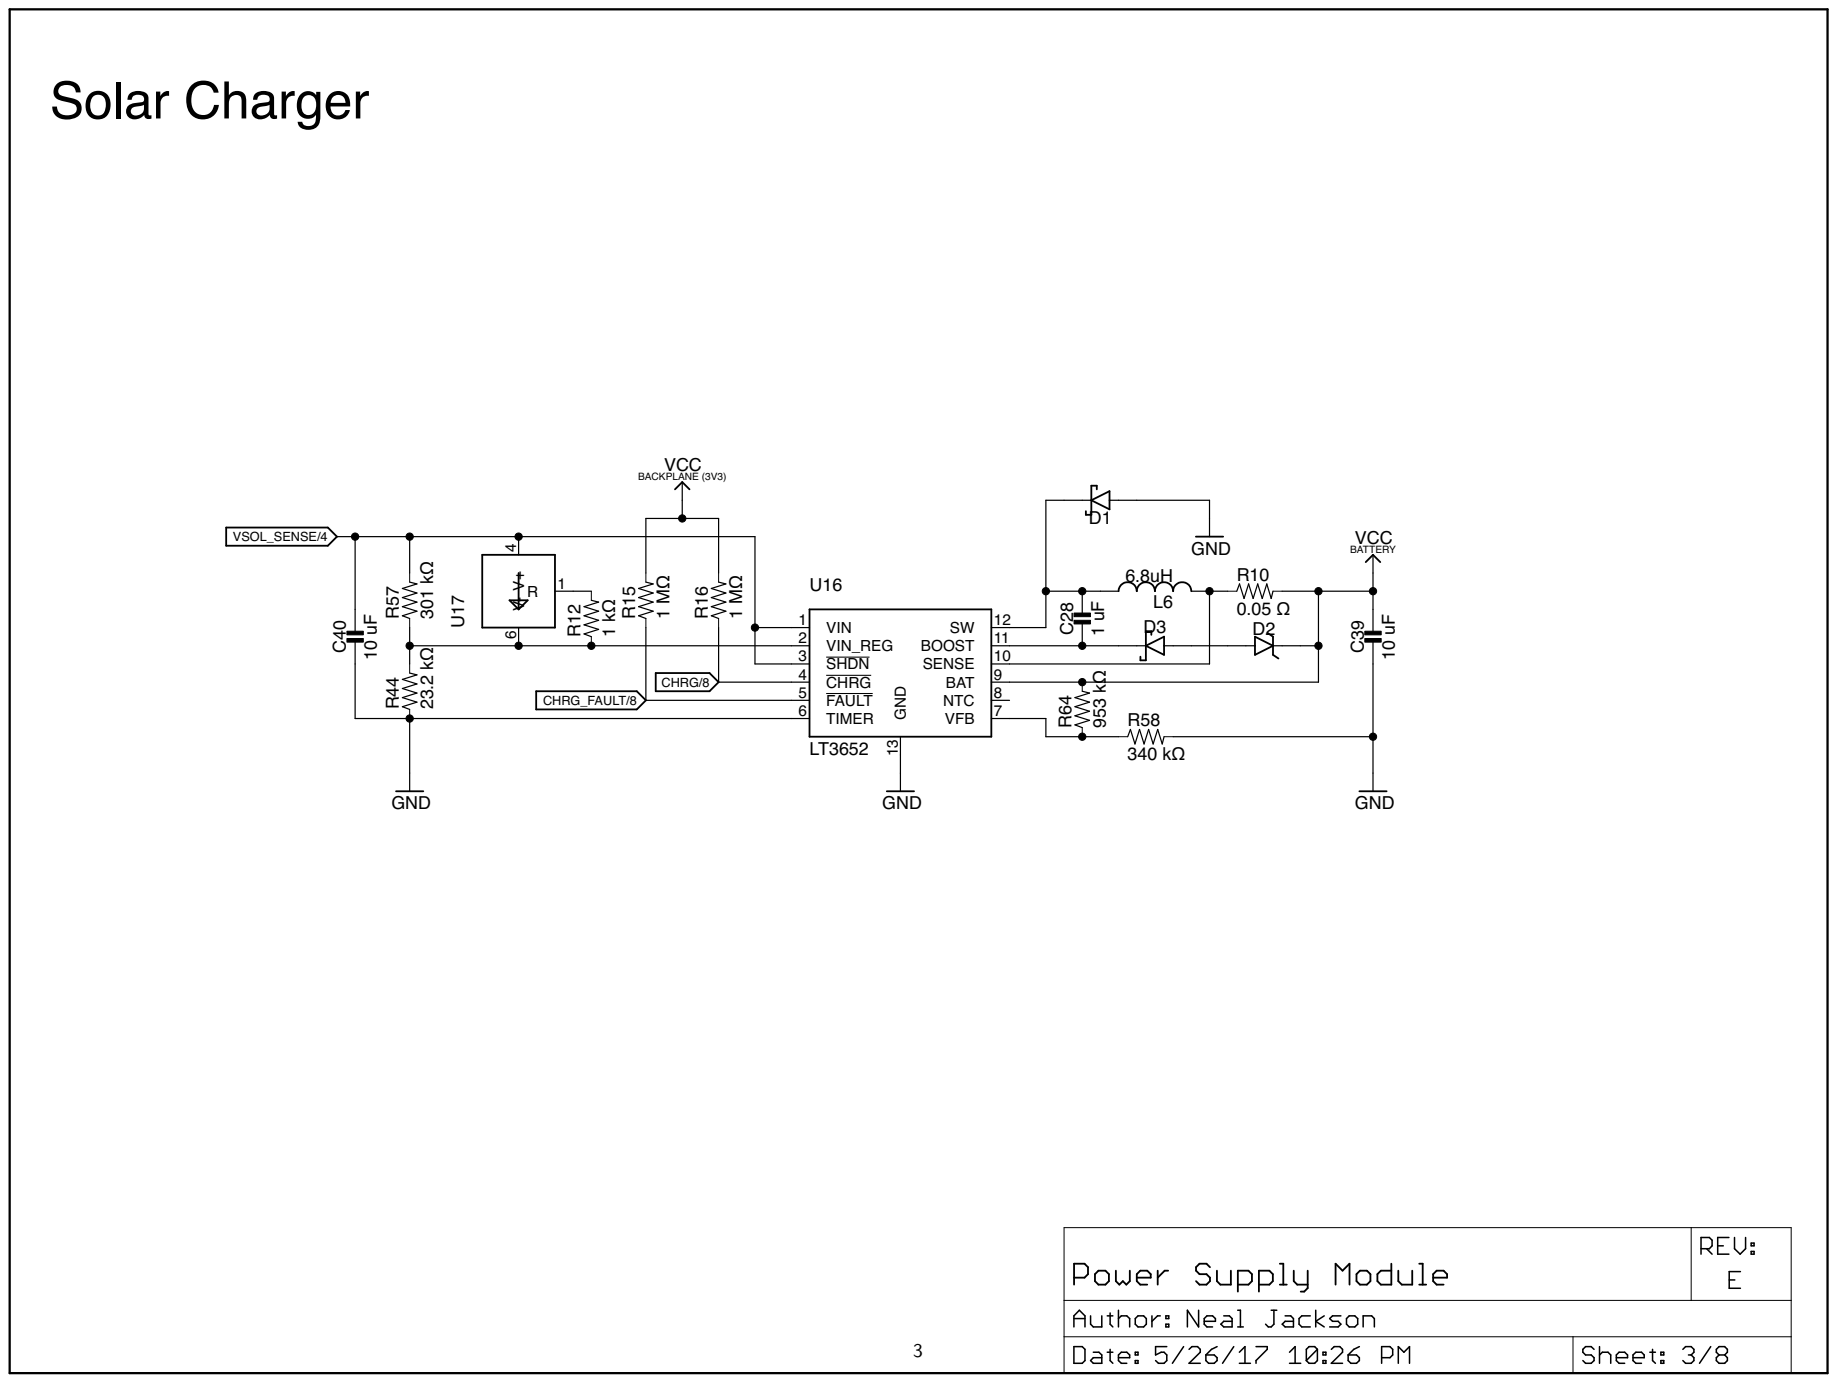
[picture p140: page 3]

# Monitors and Watchdog

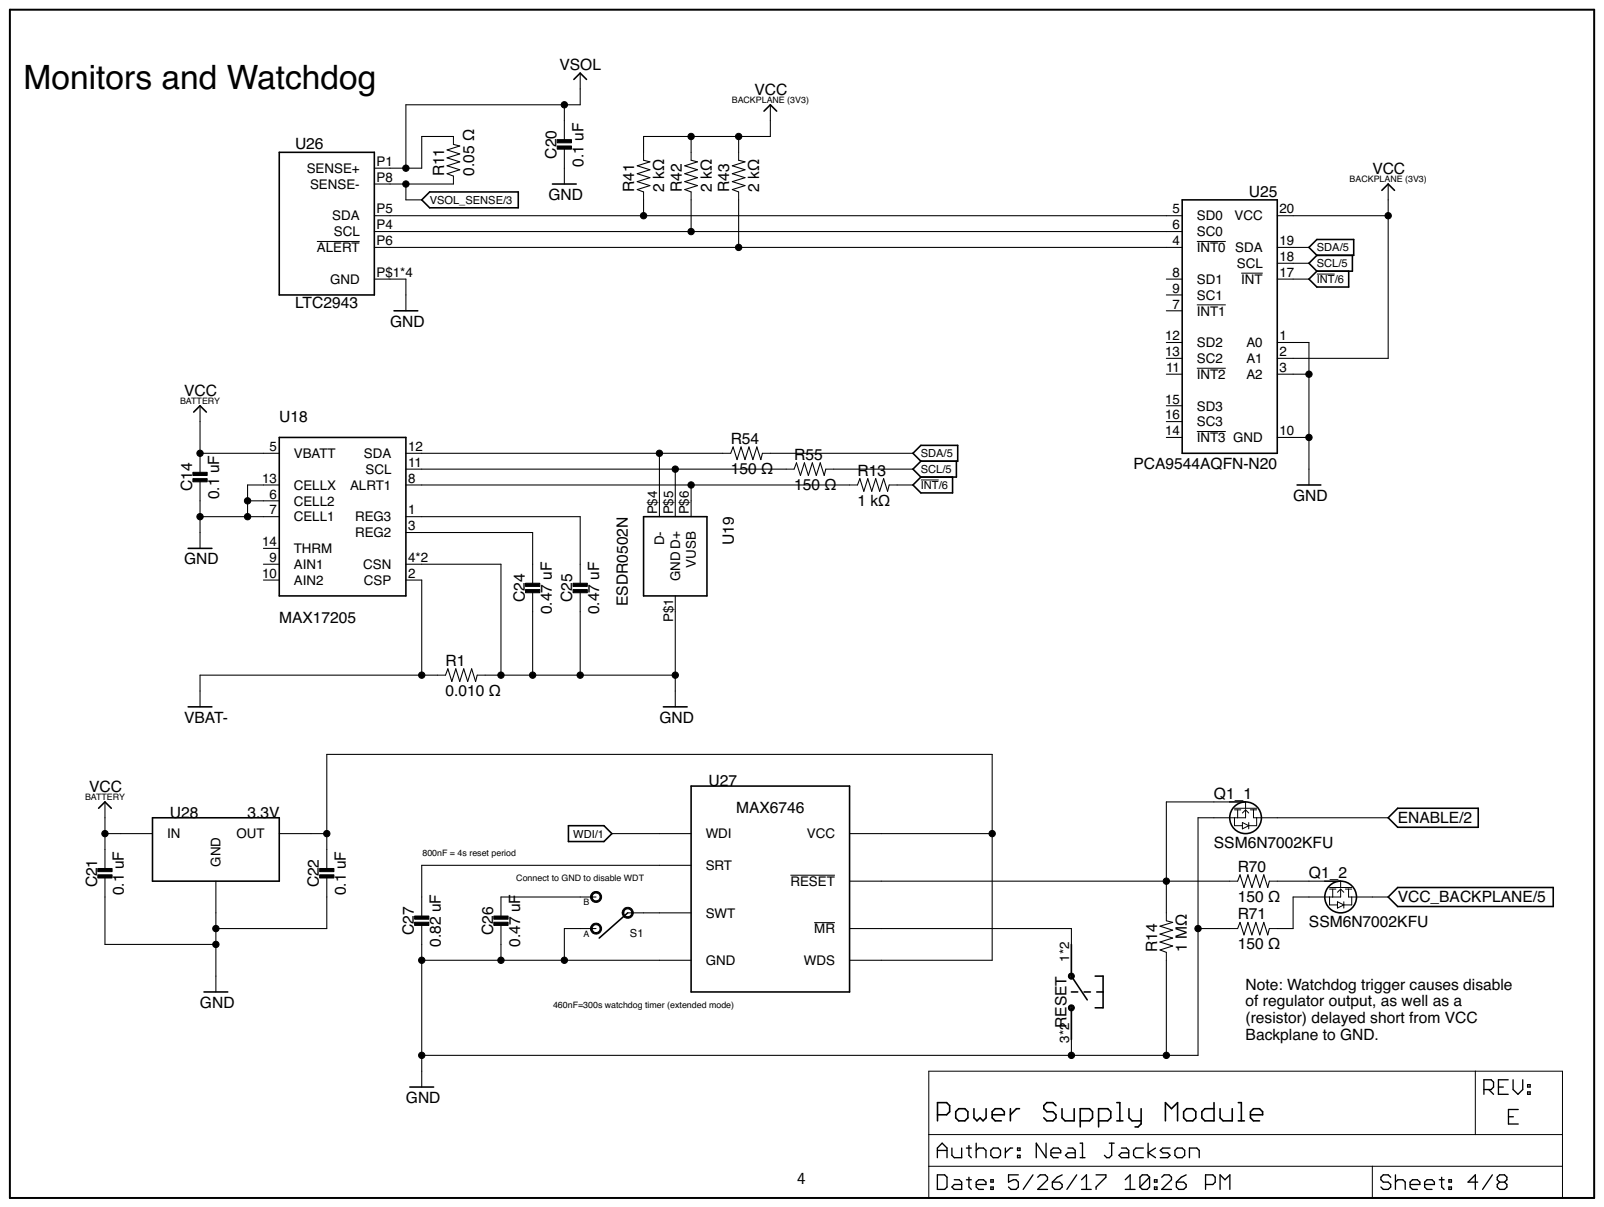
[picture p141: page 4]

of regulator output, as well as a
(resistor) delayed short from VCC
Backplane to GND.

460nF=300s watchdog timer (extended mode)

# EEPROM ID

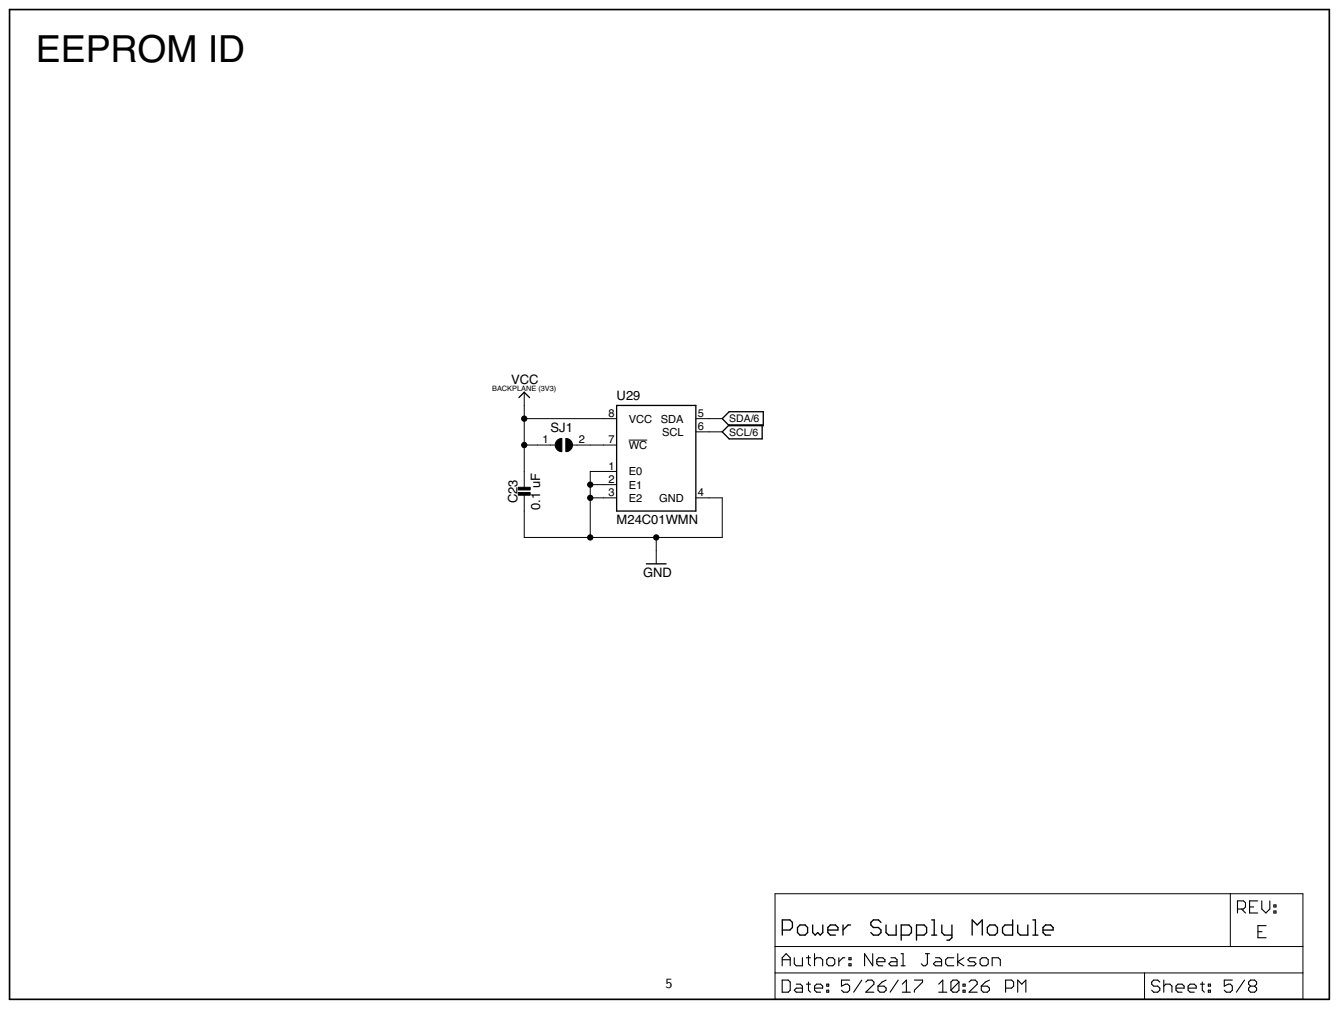
[picture p142: page 5]
M24C01WMN; GND; SDA; 5 SCL 6 VCC; 2 C²³ VCC BACKPLANE (3V3); SDA/6 SCL/6

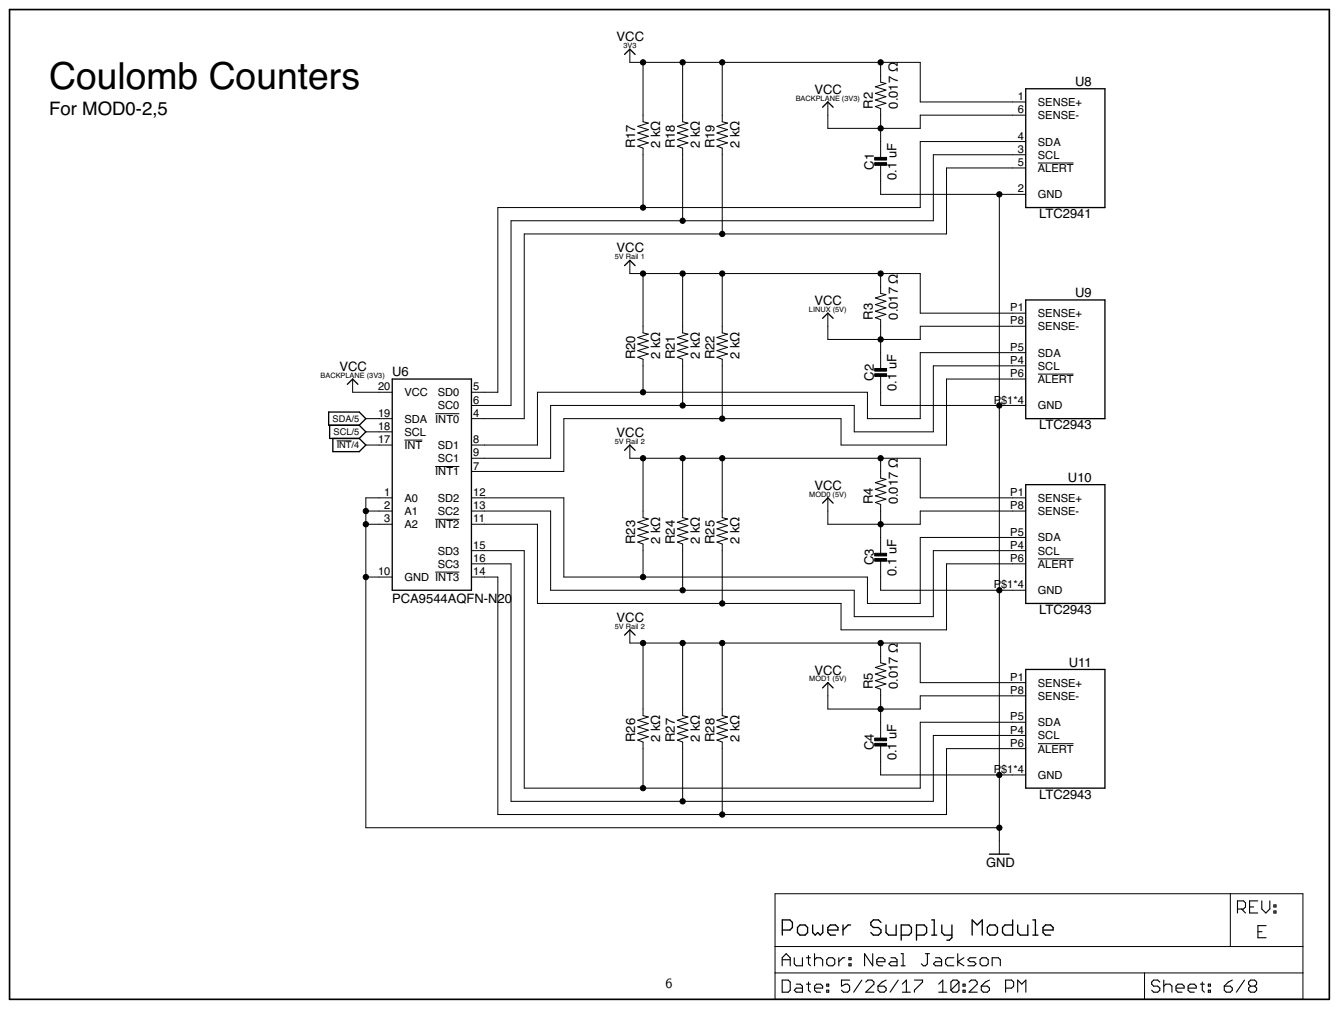
[picture p143: page 6]

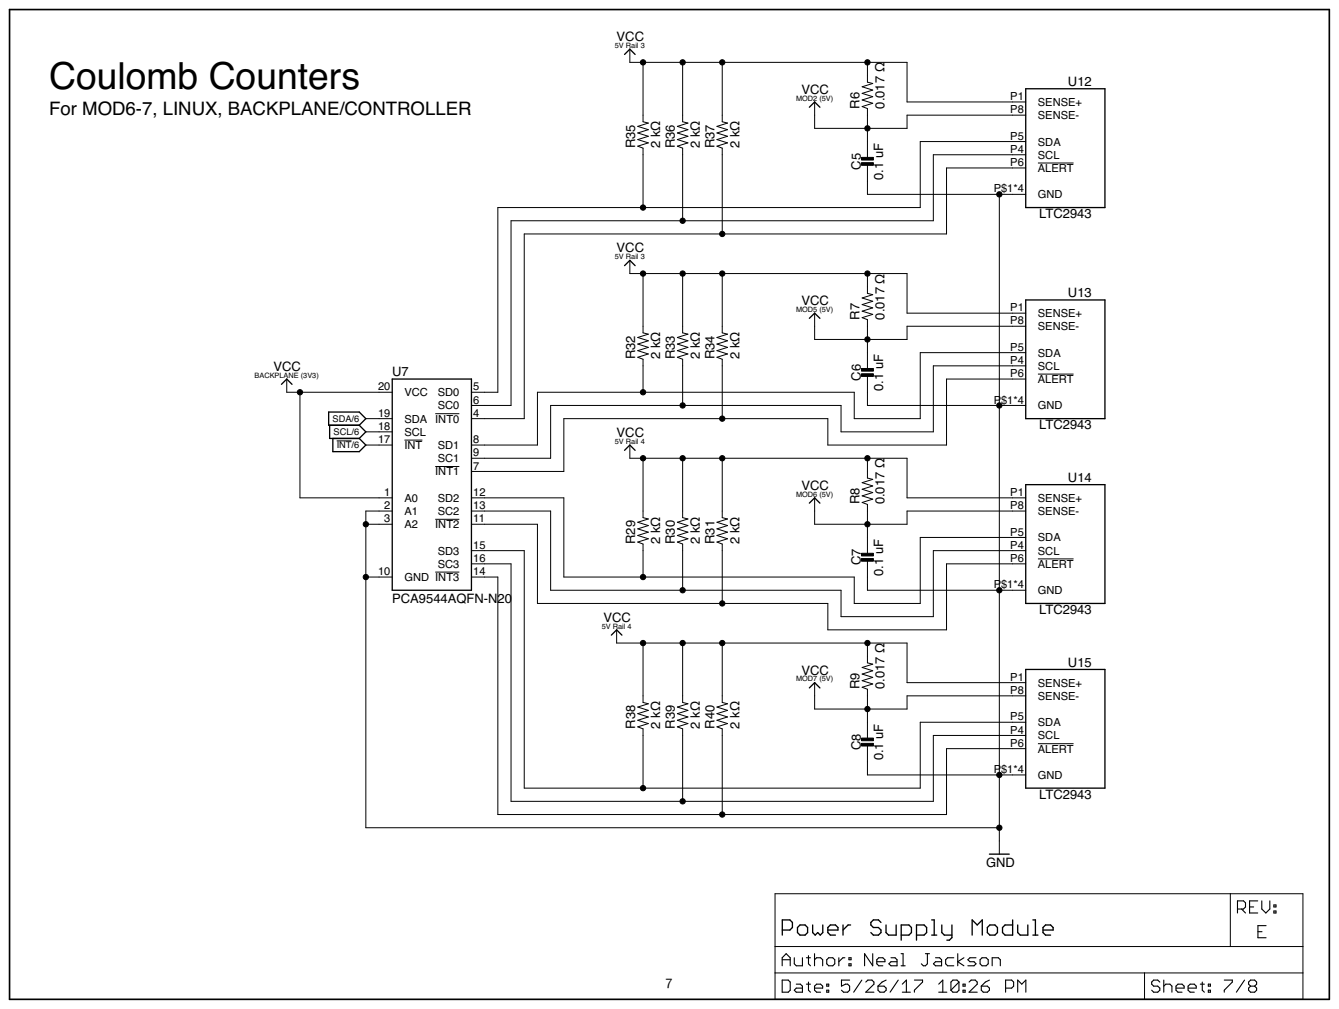
[picture p144: page 7]

# Debugging

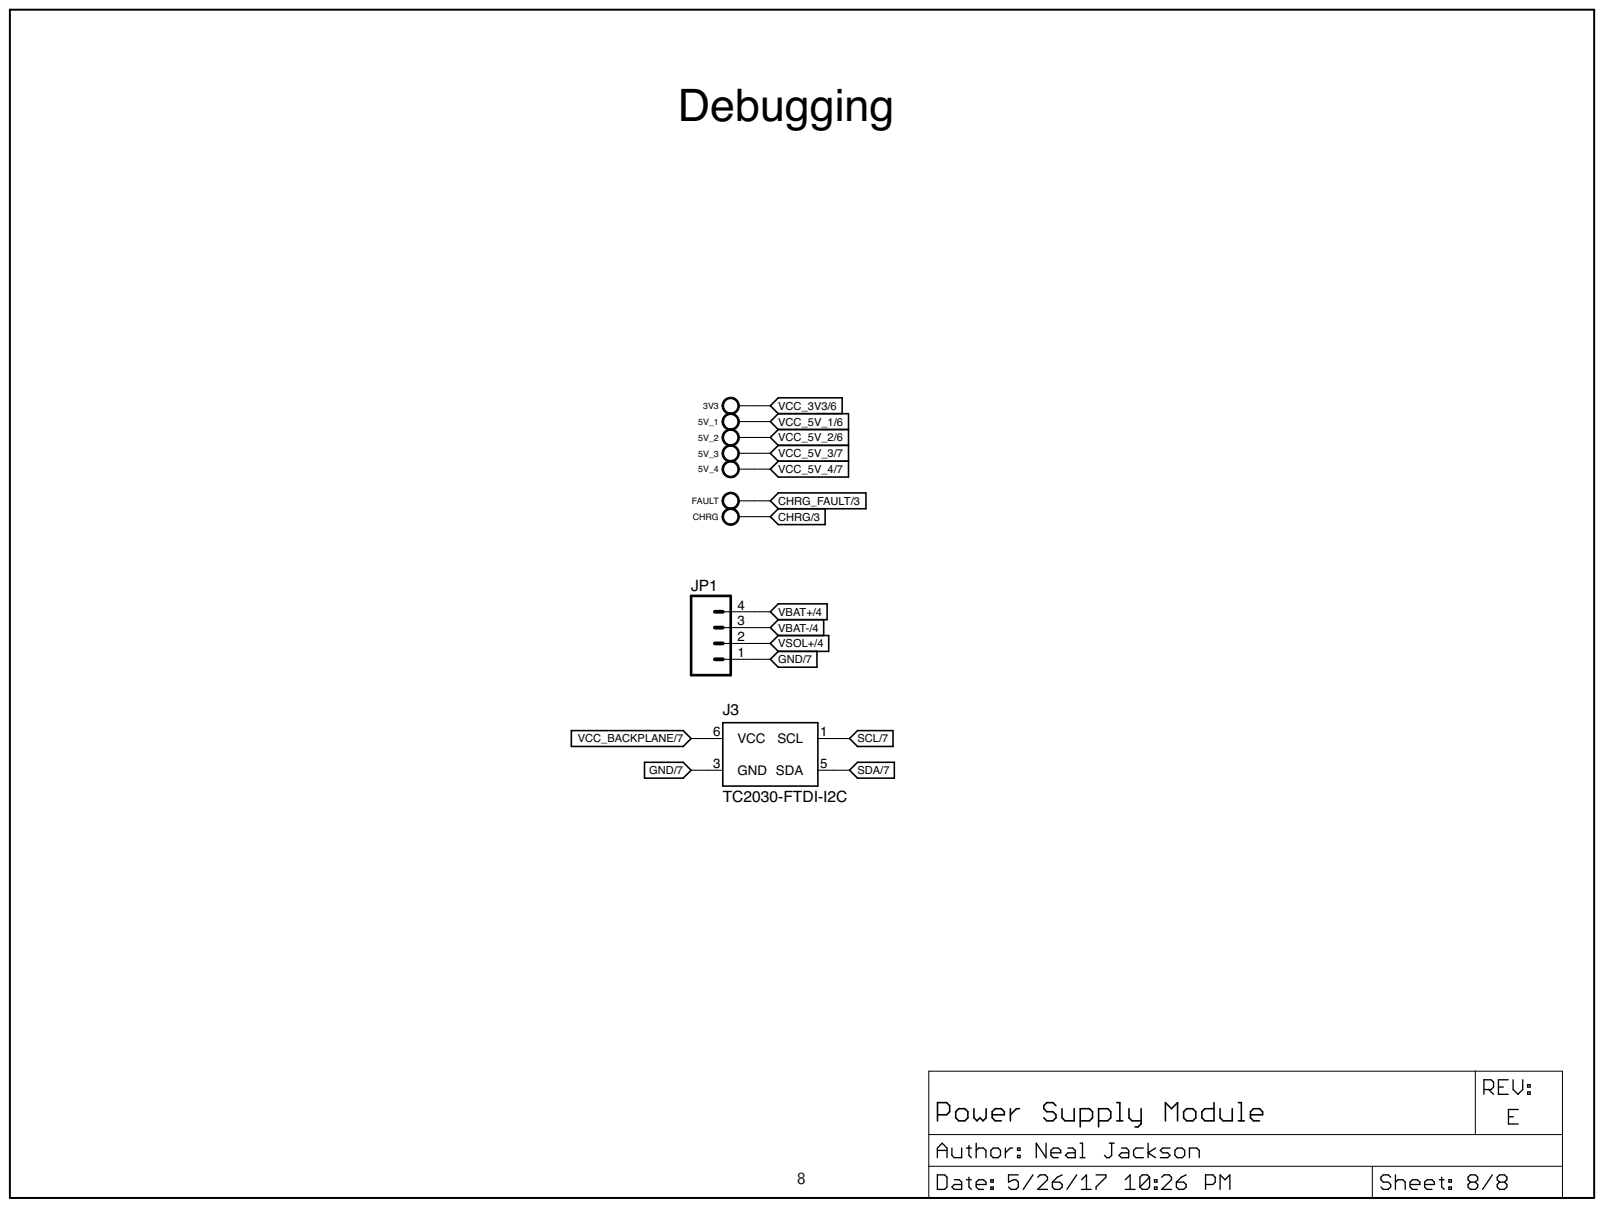
[picture p145: page 8]
VCC; GND; SCL; 1 SDA; TC2030-FTDI-I2C; FAULT CHRG; VCC_3V3/6 VCC_5V_1/6 VCC_5V_2/6 VCC_5V_3/7 VCC_5V_4/7; GND/7; CHRG_FAULT/3 CHRG/3; VCC_BACKPLANE/7; SCL/7 SDA/7

VBAT-/4 VSOL+/4 VBAT+/4

## Top and Bottom Layers

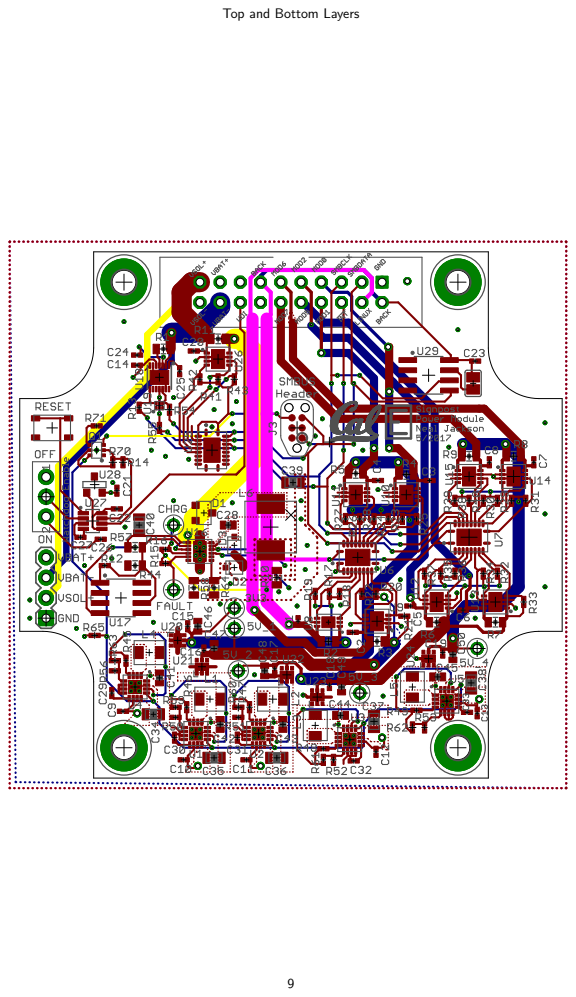
[picture p146: page 9]

## Top Layer

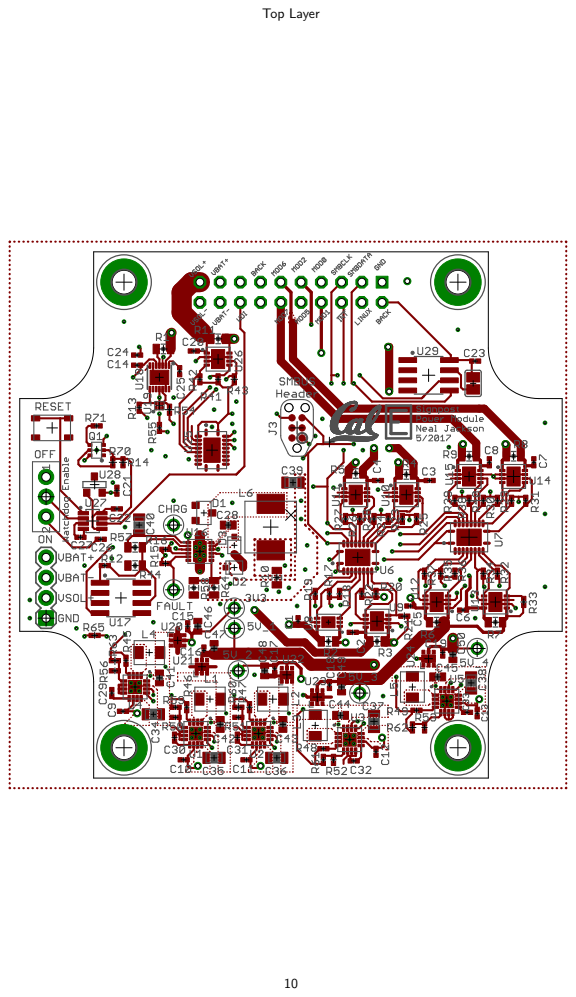
[picture p147: page 10]

## Bottom Layer

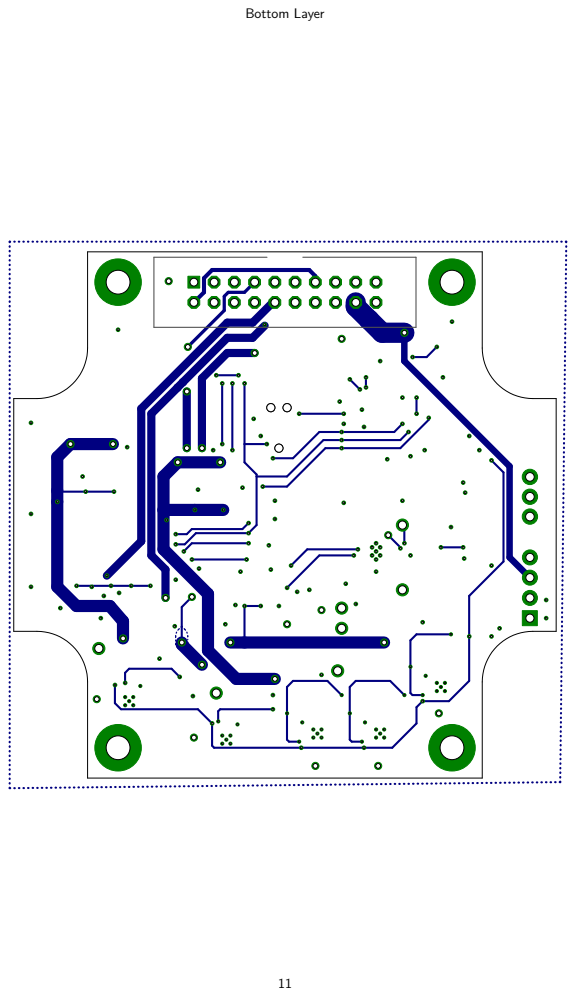
[picture p148: page 11]

## Top Copper Layer

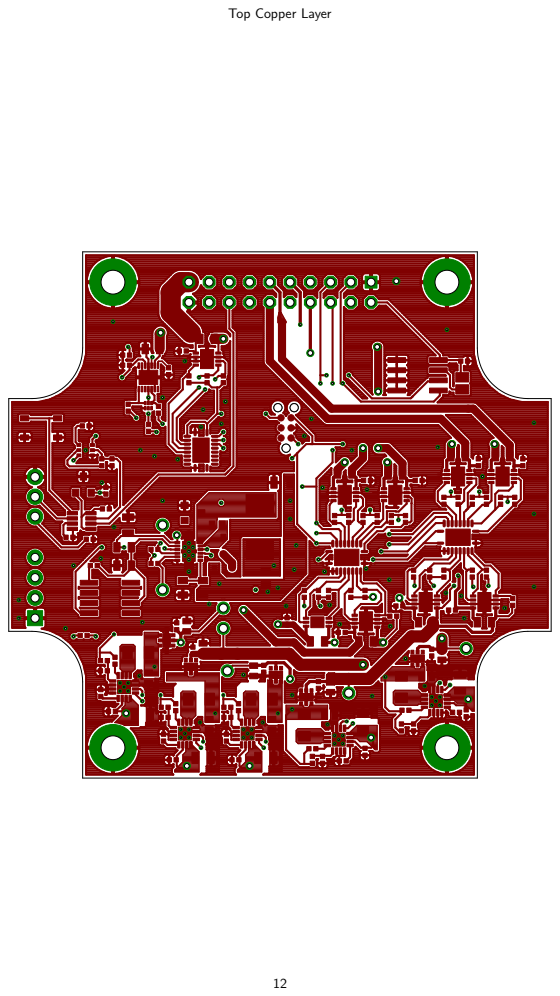
[picture p149: page 12]

## Layer 2 Copper

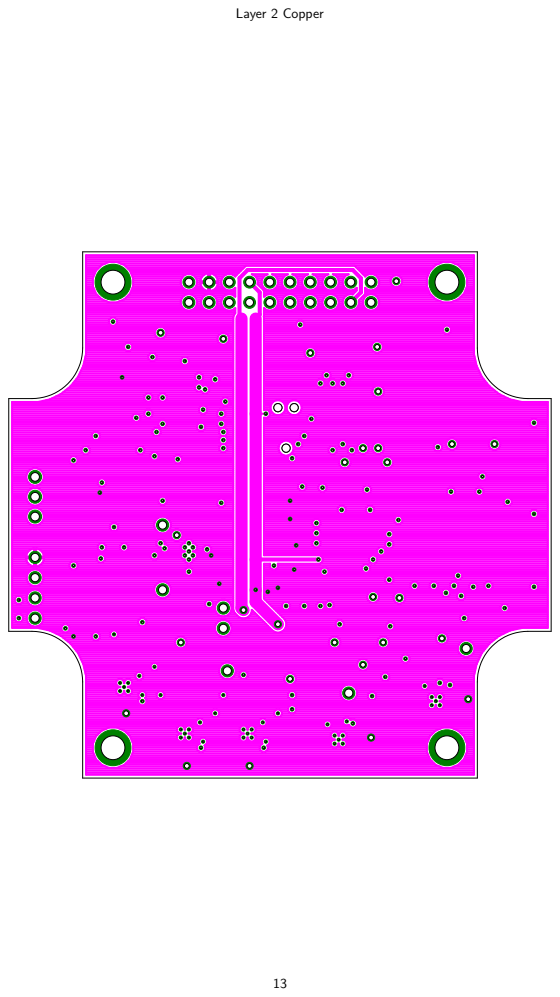
[picture p150: page 13]

## Layer 3 Copper

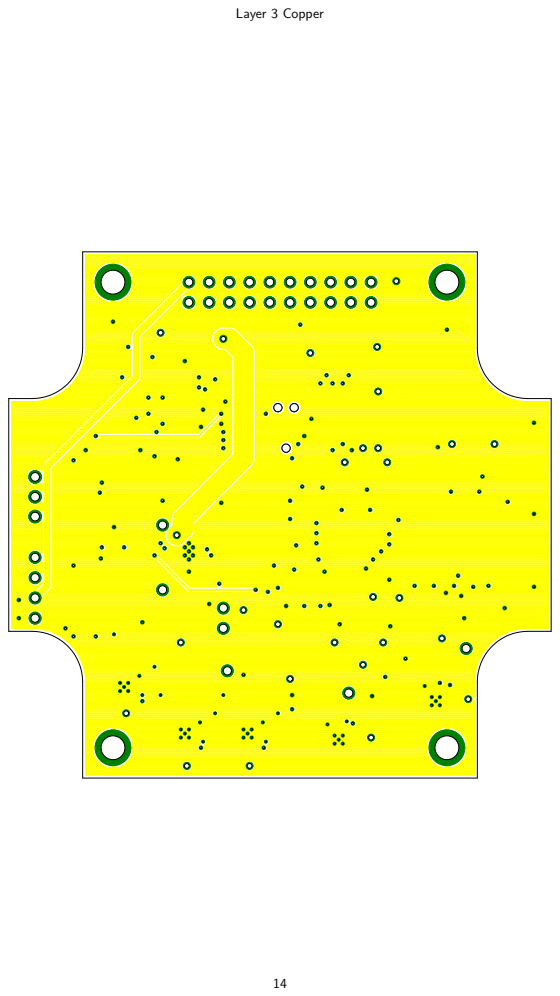
[picture p151: page 14]

## Bottom Copper Layer

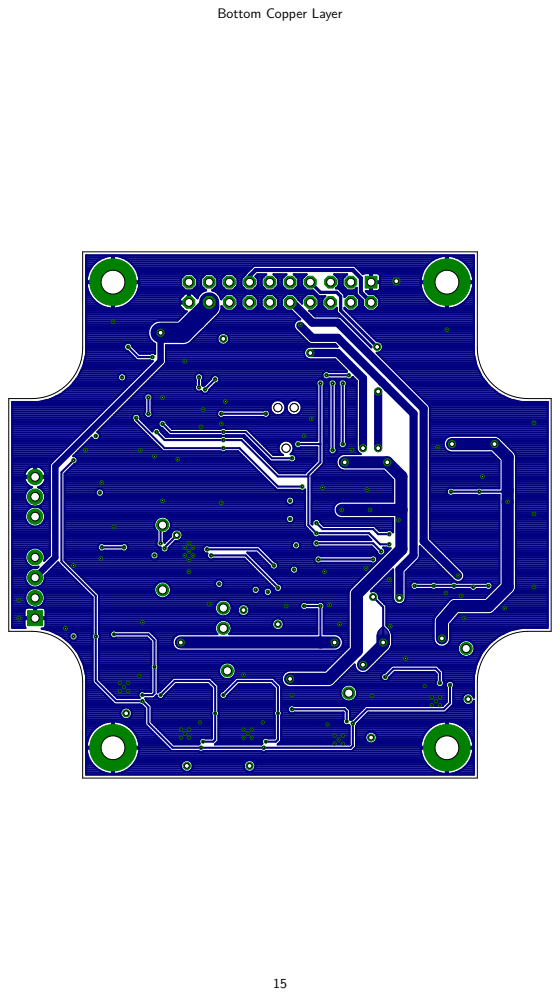
[picture p152: page 15]

## Top Paste Layer with Silkscreen

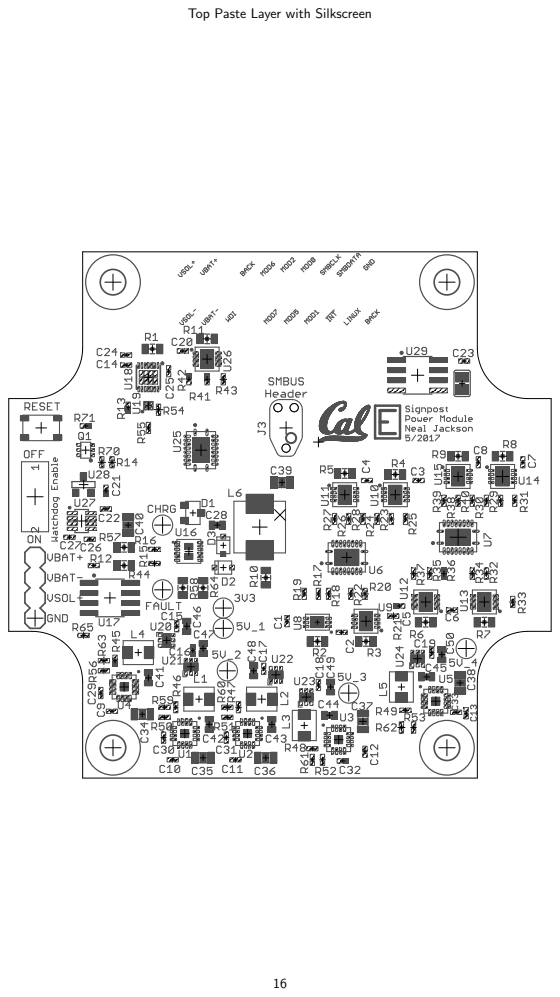
[picture p153: page 16]

## Bottom Paste Layer with Silkscreen


## Top and Bottom Layers 1:1 Scale

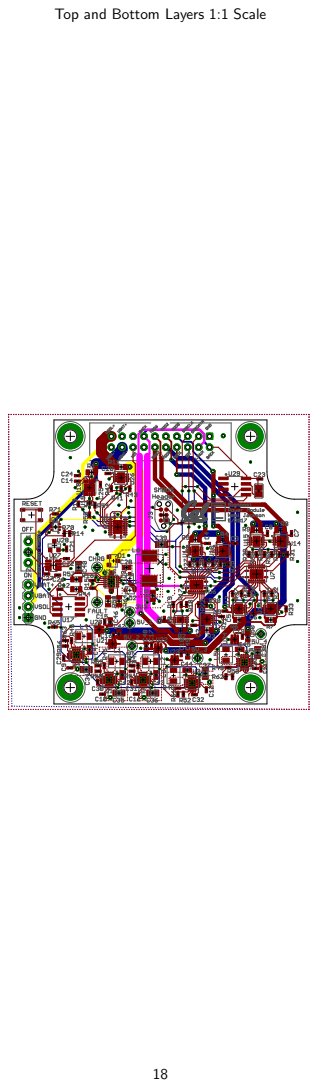
[picture p154: page 18]

## Top Layer 1:1 Scale

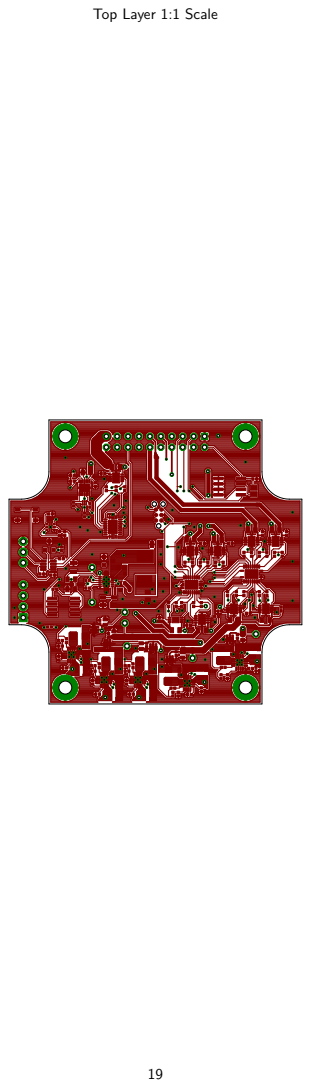
[picture p155: page 19]

## Layer 2 Copper 1:1 Scale

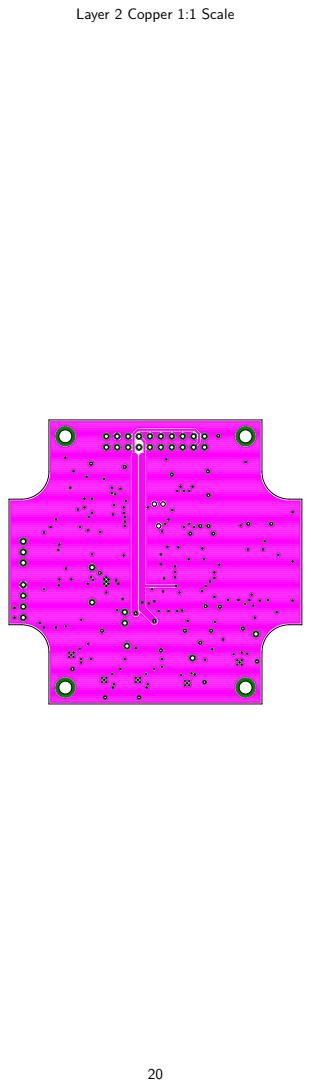
[picture p156: page 20]

## Layer 3 Copper 1:1 Scale

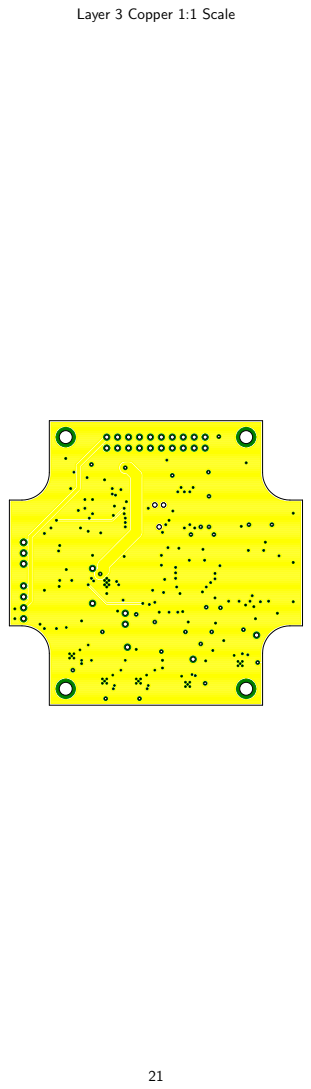
[picture p157: page 21]

## Bottom Copper Layer 1:1 Scale

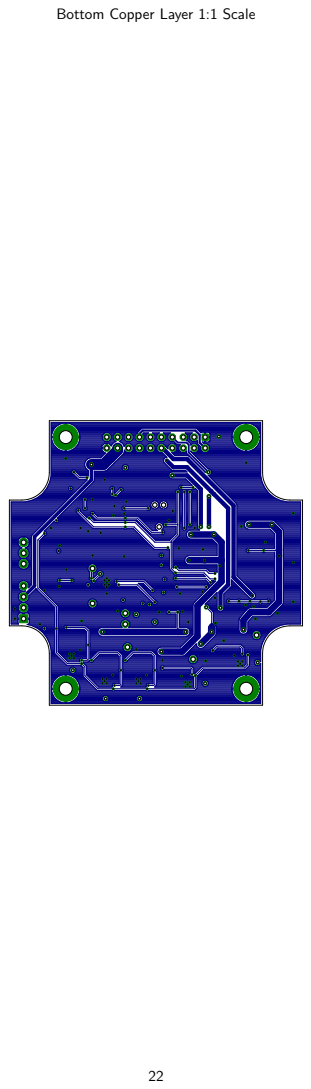
[picture p158: page 22]
