lab11/signpost/hardware/radio_module/rev_b/radio_module.pdf

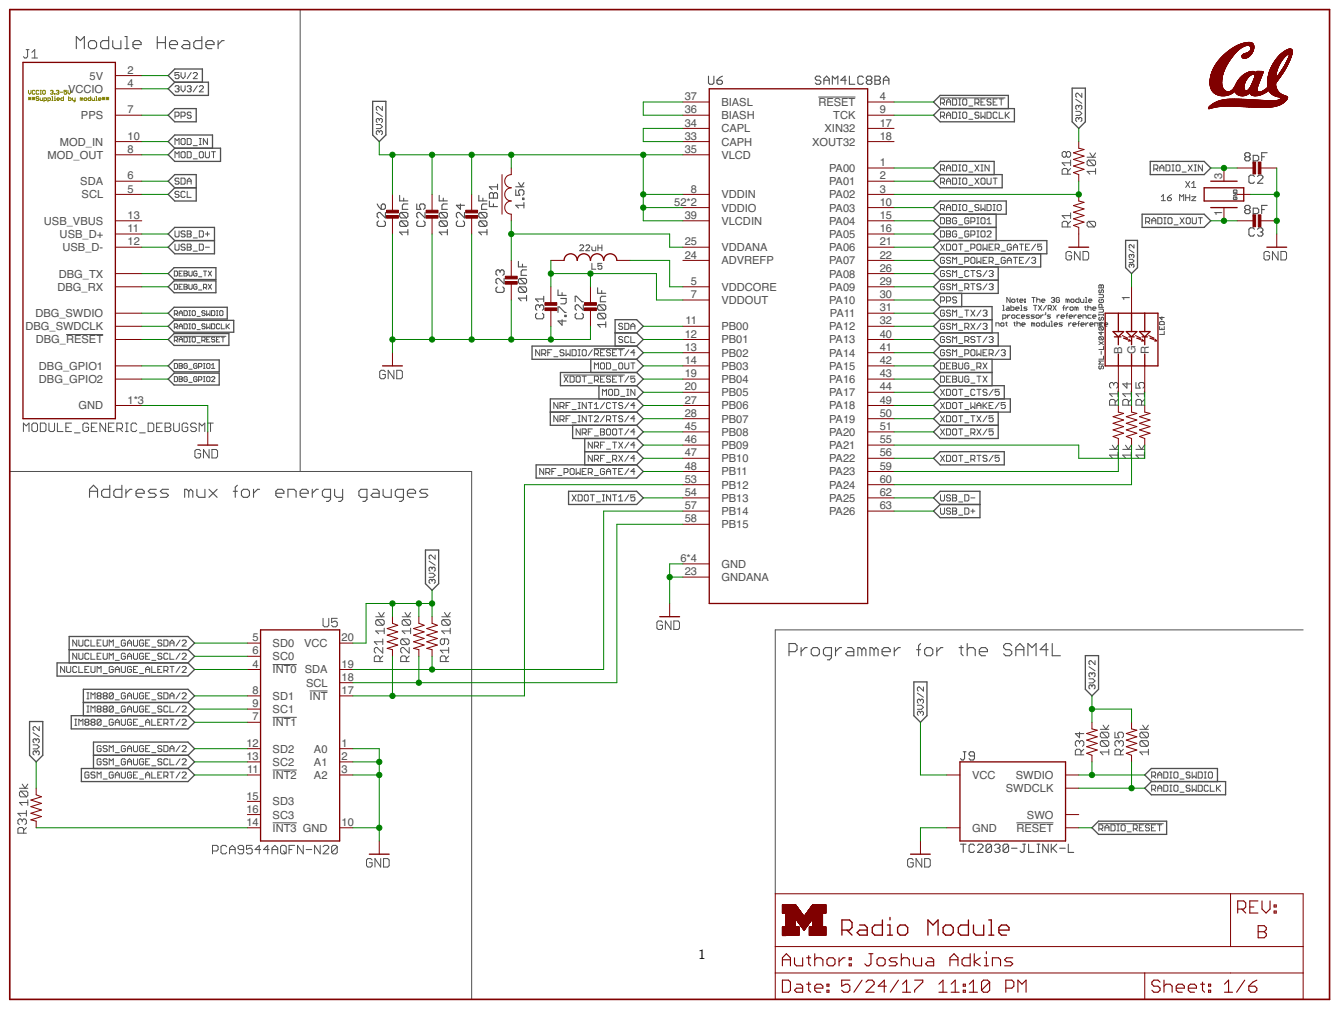
[picture p178: page 1]
2 GND; 1*3 MOD_OUT; 8 SDA; 6 SCL; 5 USB_D+; 11 USB_D-; 12 PPS; 7 USB_VBUS; 13 VCCIO; 4 MOD_IN; 10 DBG_TX DBG_RX DBG_GPIO1 DBG_GPIO2 DBG_RESET DBG_SWDCLK DBG_SWDIO; 1 3 GND 6*4; VDDCORE 5; VDDOUT 7; VDDIN 8; ADVREFP 24; VDDANA 25; VDDIO 52*2; GNDANA 23; RESET; 4 TCK; 9 XIN32; 17 XOUT32; 63 VLCDIN 39; VLCD 35; BIASL 37; BIASH 36; CAPL 34; CAPH 33; 3 INT0 4; INT1 7; GND; 10 INT2 11; INT3 14; INT; 17 SCL; 18 SDA; 19 VCC; SWDIO SWDCLK SWO RESET VCC GND; 1 BGR

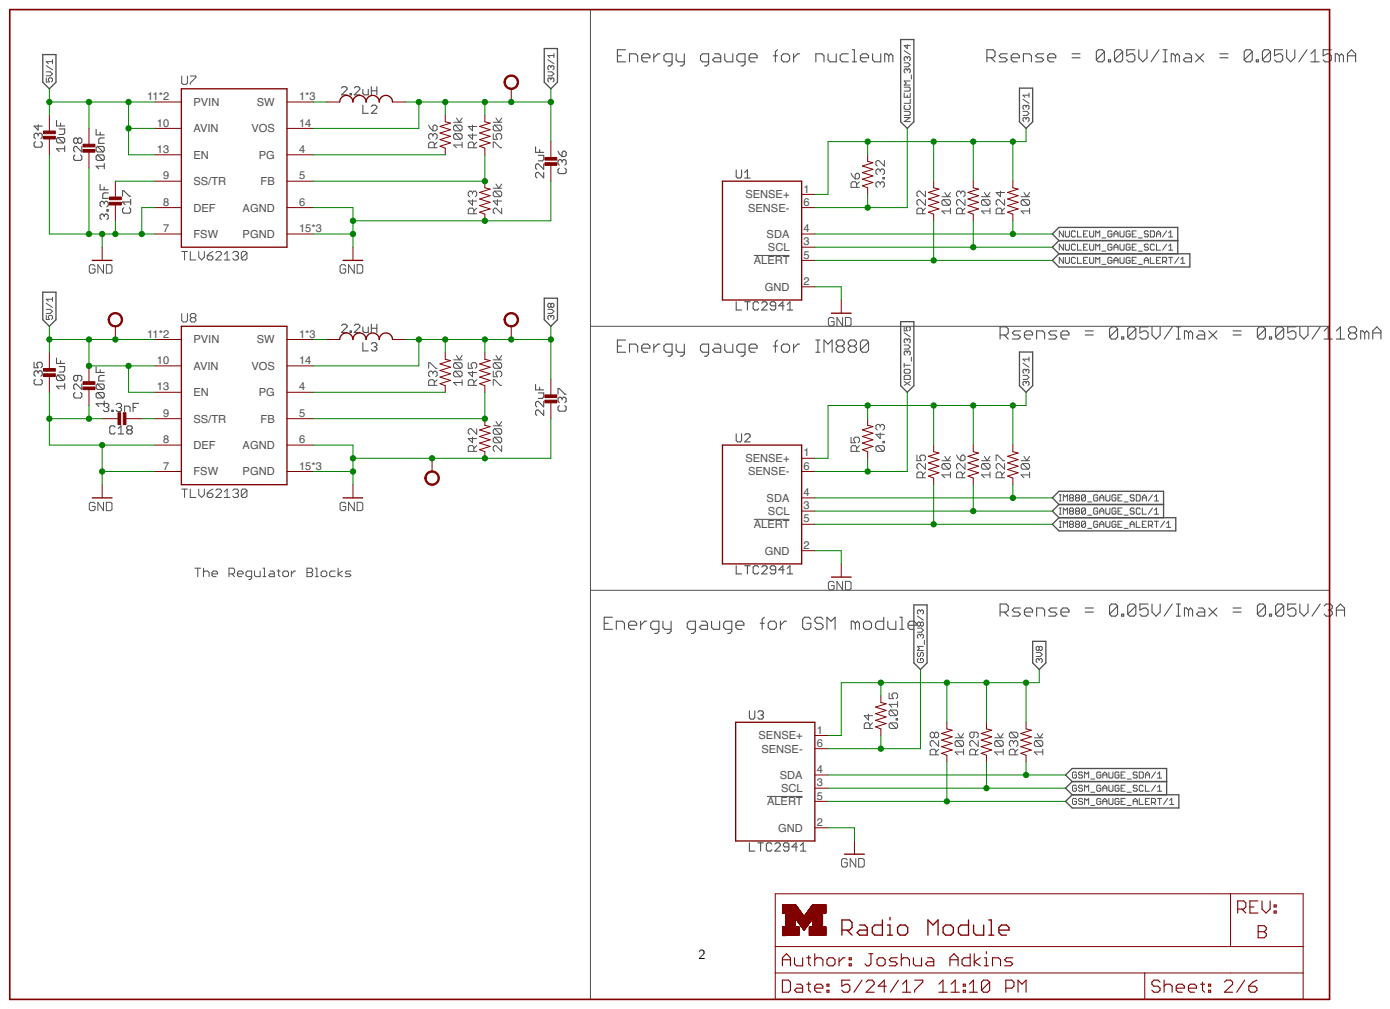
[picture p179: page 2]
2 PVIN 11*2; AVIN 10; DEF 8; FSW 7; 1*3 VOS; 5 AGND; 6 PGND; 15*3 PVIN 11*2; SENSE+; 1 SENSE-; 6 SDA; 4 SCL; 3 ALERT; 5 GND; 2 SENSE+

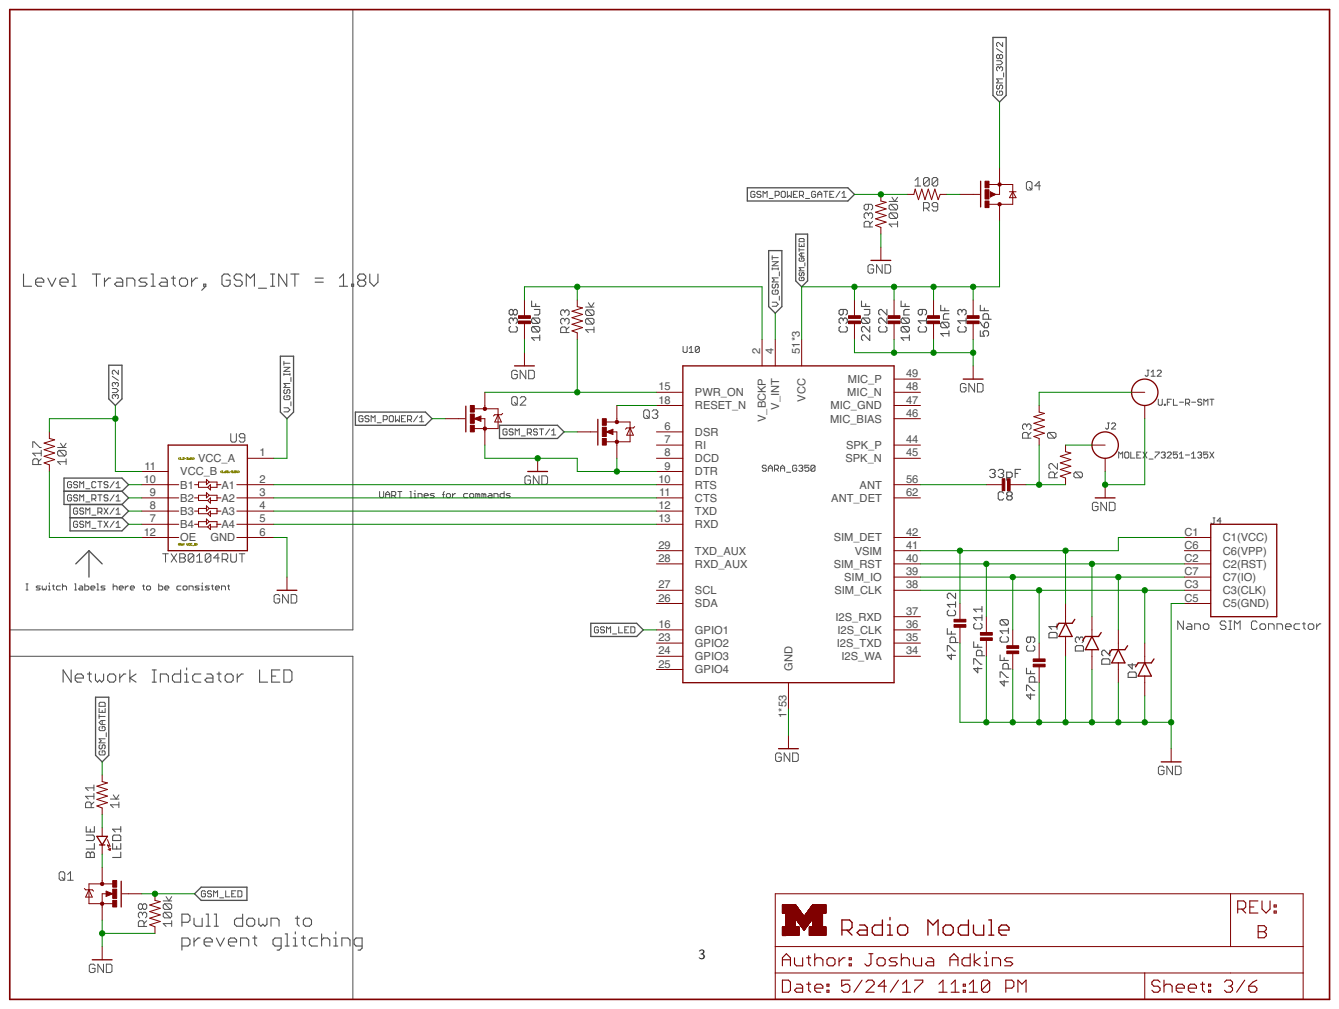
[picture p180: page 3]
GND 1*53; VCC ⁵¹*3; MIC_P; 49 MIC_N; 48 MIC_GND; 47 MIC_BIAS; 46 SPK_N; 45 SPK_P; 44 SIM_DET; 42 VSIM; 41 SIM_RST; 40 SIM_IO; 39 SIM_CLK; 38 I2S_RXD; 37 I2S_CLK; 36 I2S_TXD; 34 SCL 27; SDA 26; GPIO4 25; GPIO3 24; GPIO2 23; GPIO1 16; RXD 13; TXD 12; CTS 11; RTS 10; DTR 9; DCD 8; DSR 6; V_BCKP ² V_INT 4 RXD_AUX 28; TXD_AUX 29; ANT; 56 ANT_DET; 62 PWR_ON 15; RESET_N 18; C5(GND) C5; C6(VPP) C6; C3(CLK) C3; C2(RST) C2; C1(VCC) C1 VCC_A; 5 GND; VCC_B 11

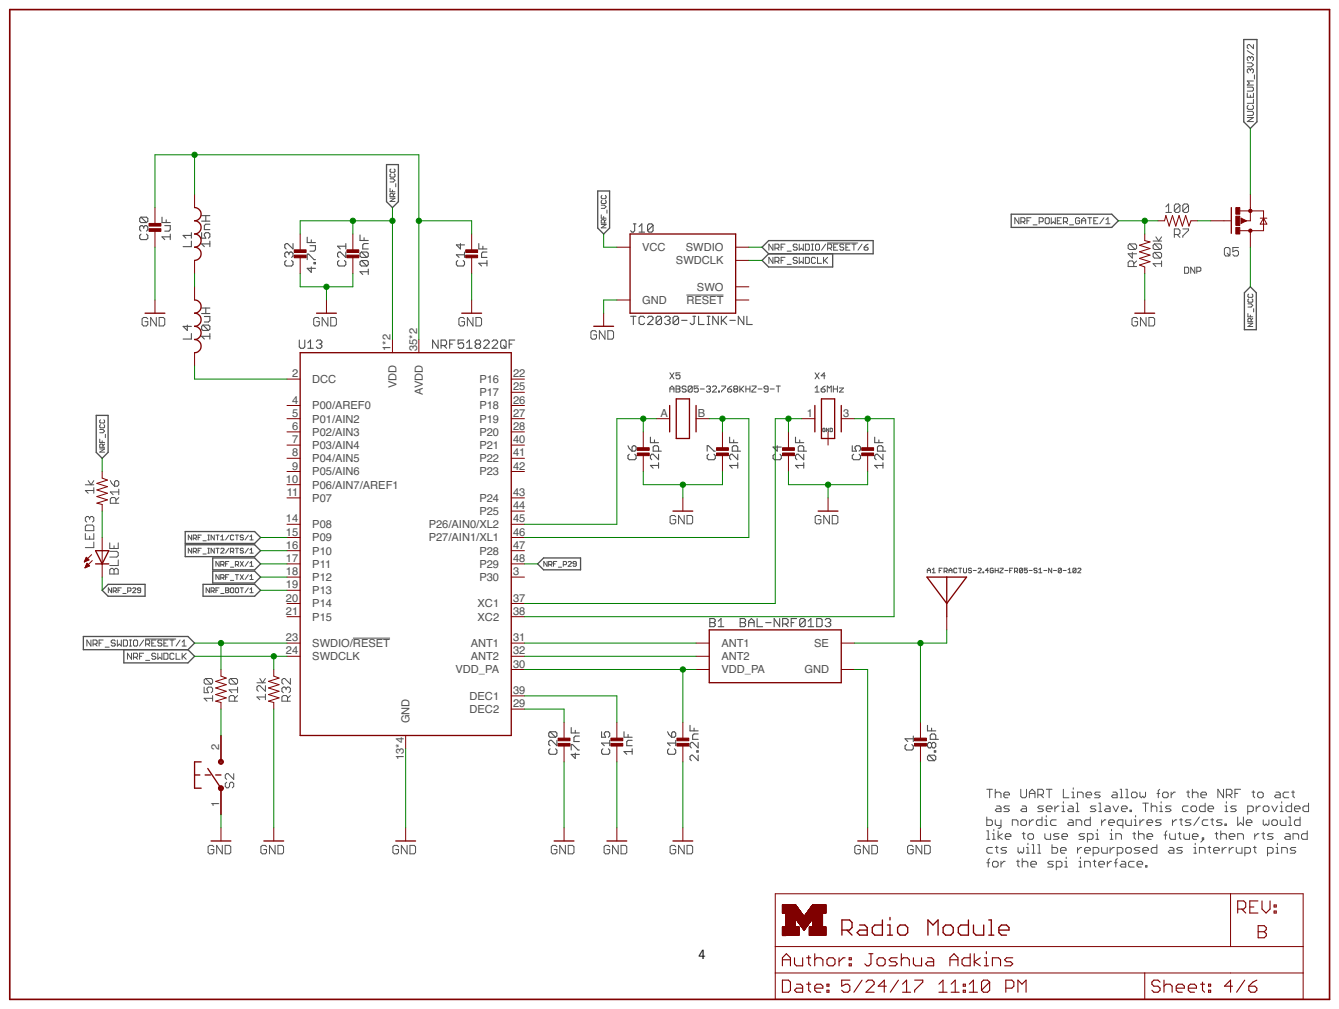
[picture p181: page 4]

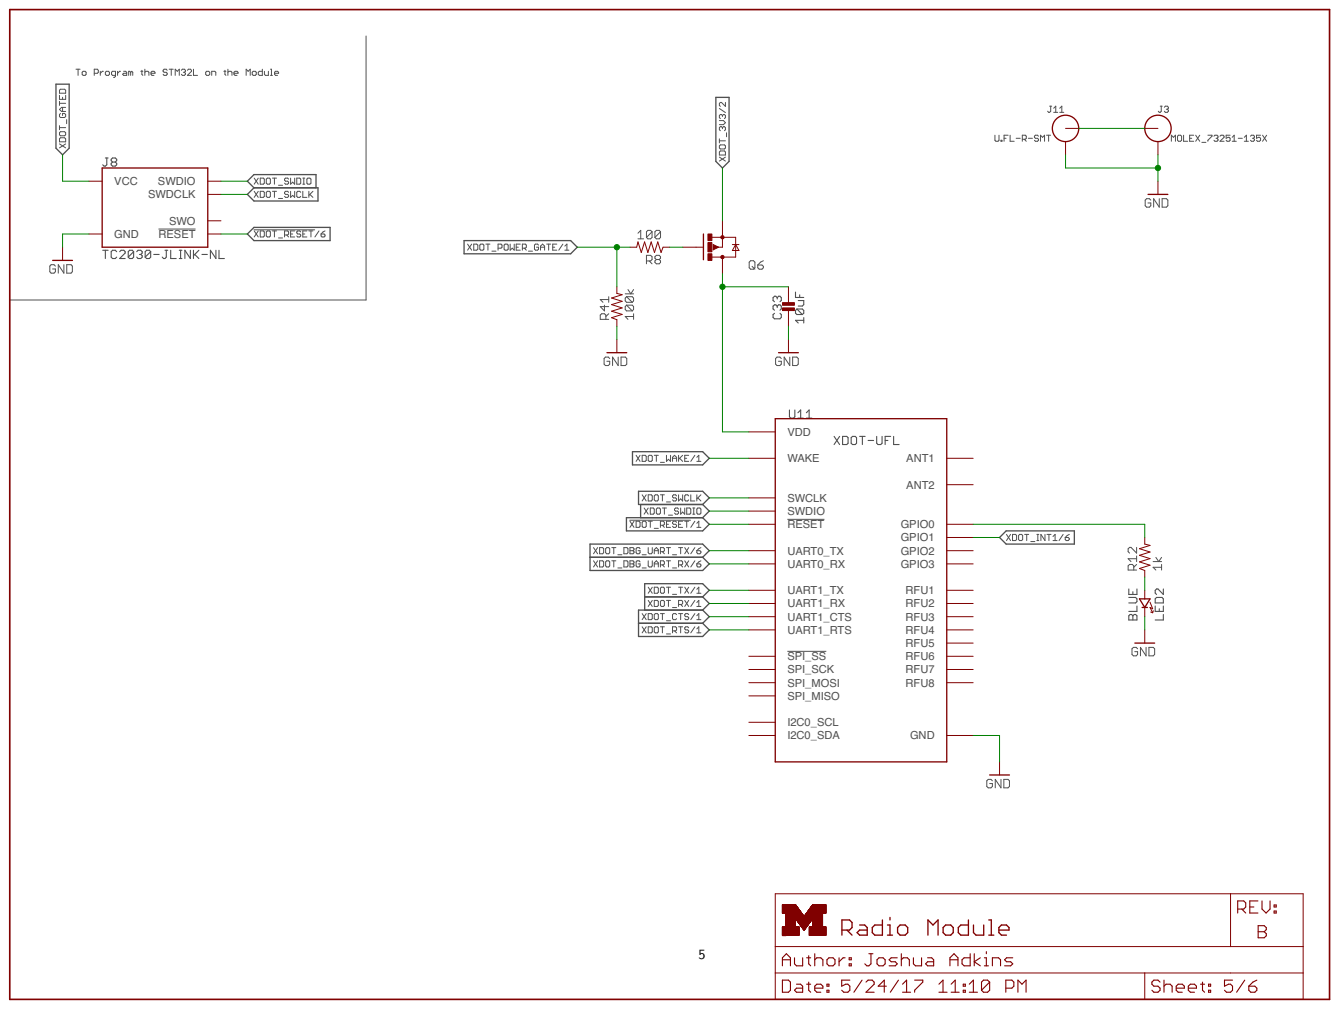
[picture p182: page 5]
5 SWDIO SWDCLK SWO RESET VCC GND; RFU1 VDD; RFU2 RFU3 RFU4 RFU5 RFU6 RFU7 RFU8 GPIO3 GPIO2 GPIO1 GPIO0 UART1_TX UART1_RX UART0_TX UART0_RX SPI_SS SPI_MOSI SPI_SCK SPI_MISO I2C0_SCL I2C0_SDA SWCLK SWDIO UART1_RTS UART1_CTS RESET WAKE; ANT1 ANT2 GND

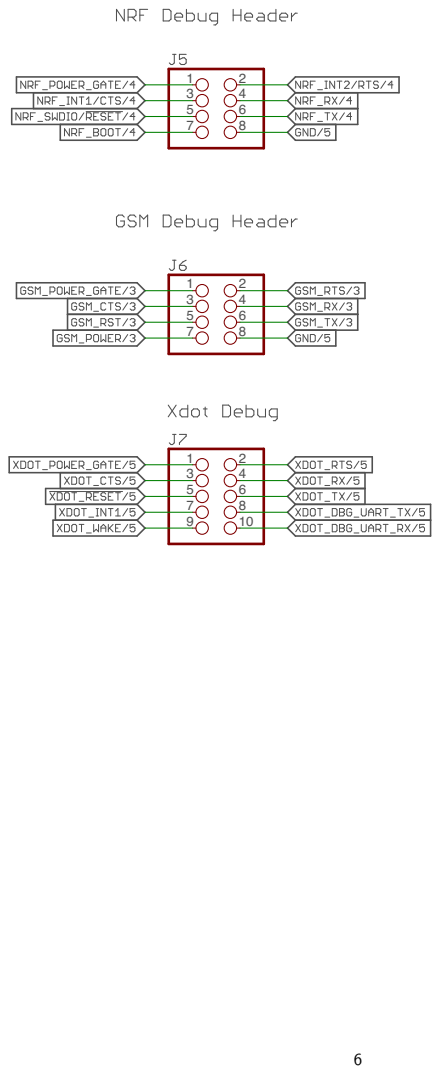
[picture p183: page 6]

## Top and Bottom Layers

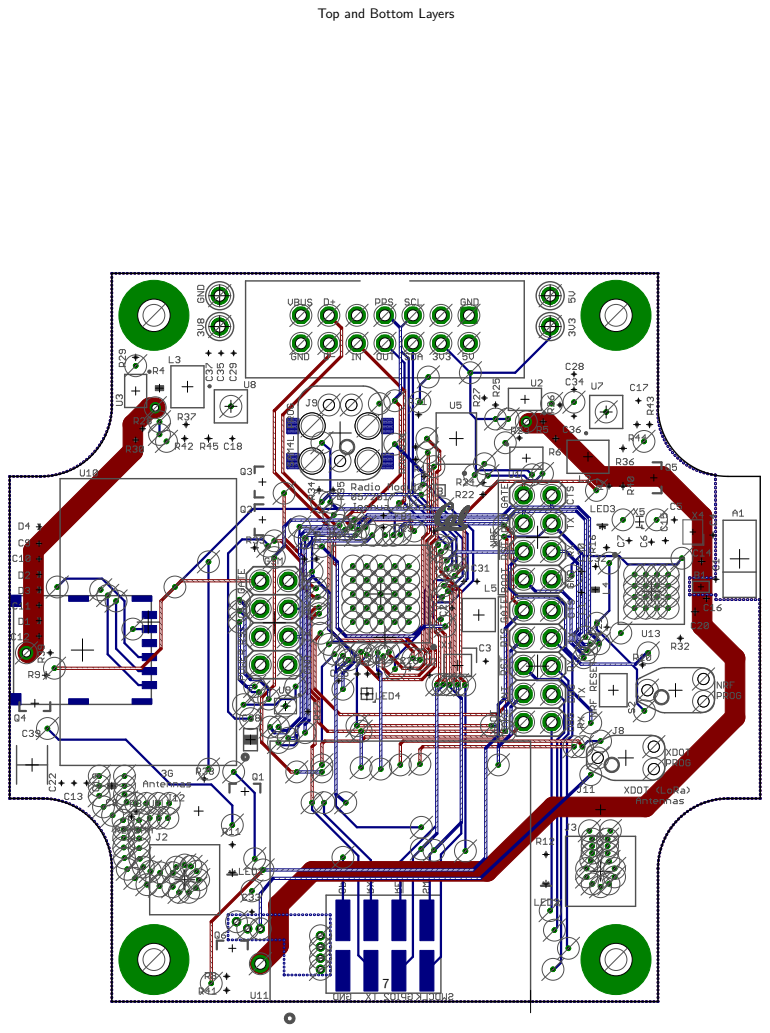
[picture p184: page 7]

## Top Layer

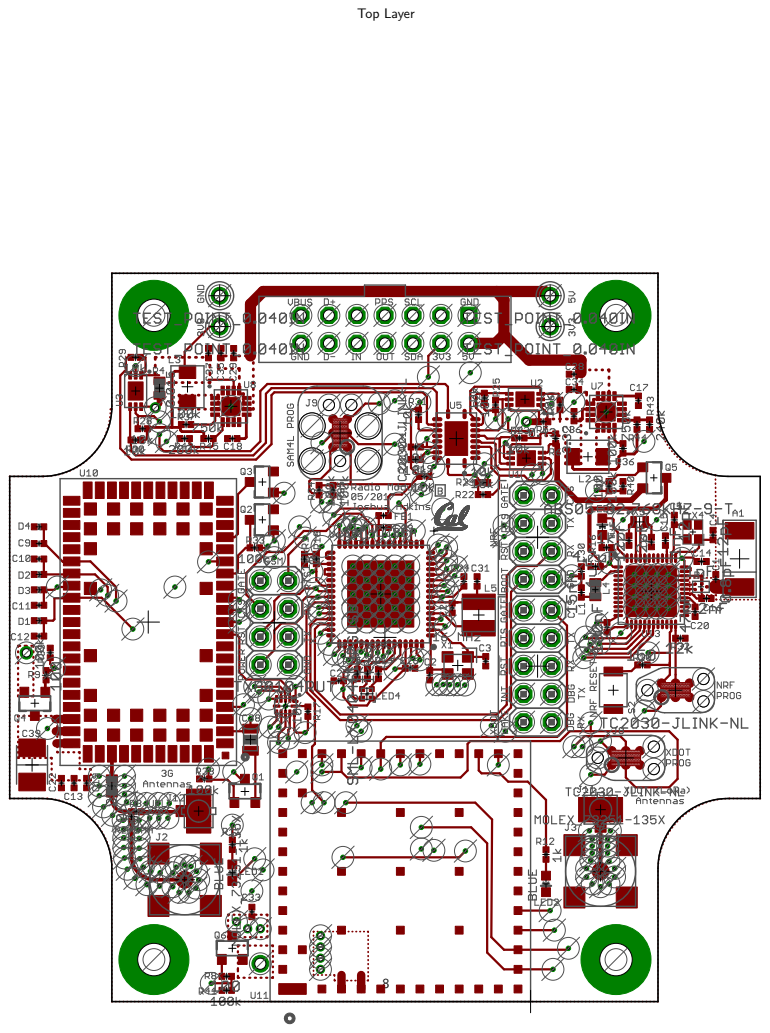
[picture p185: page 8]

## Bottom Layer

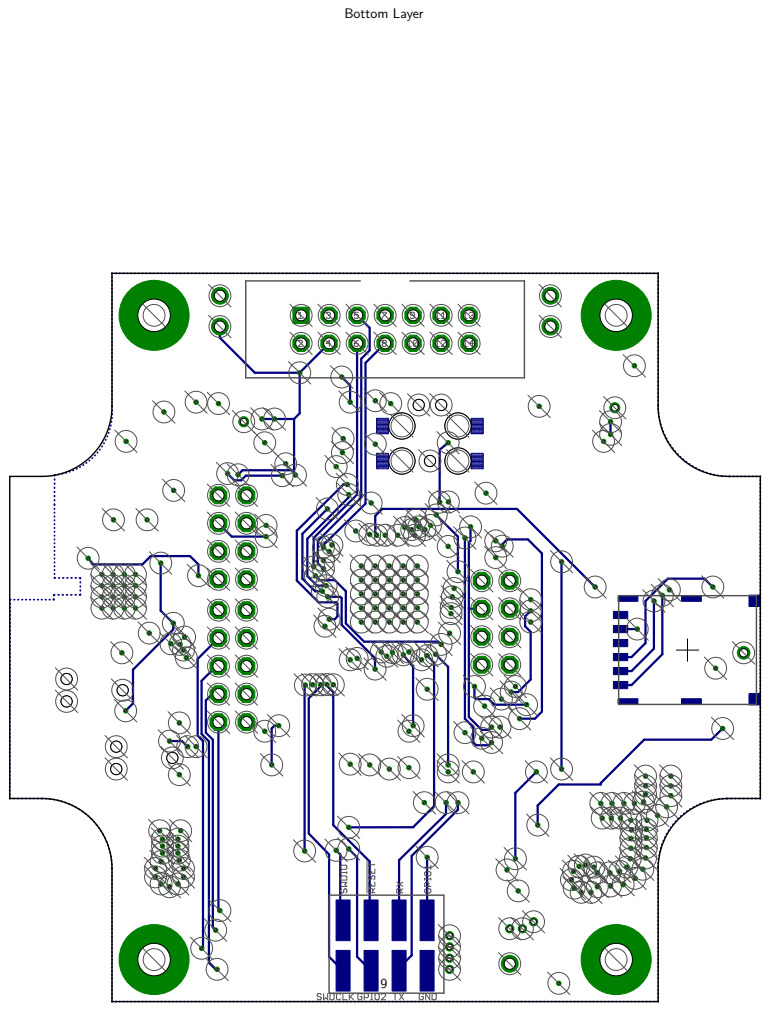
[picture p186: page 9]

## Top Copper Layer

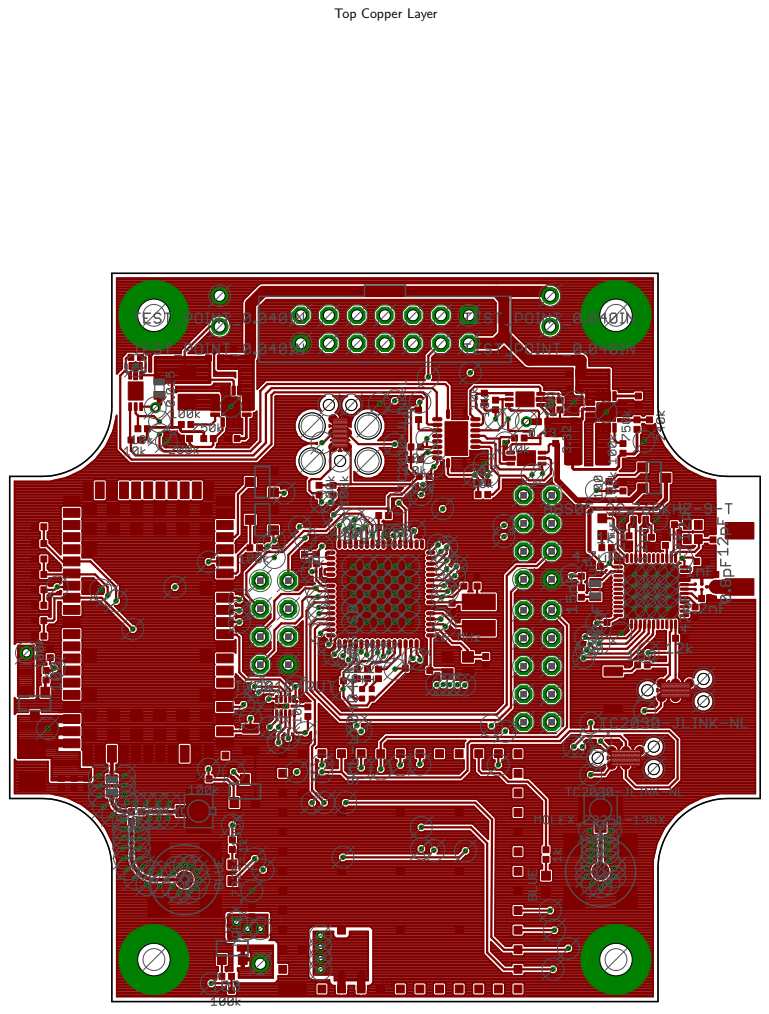
[picture p187: page 10]

## Layer 2 Copper

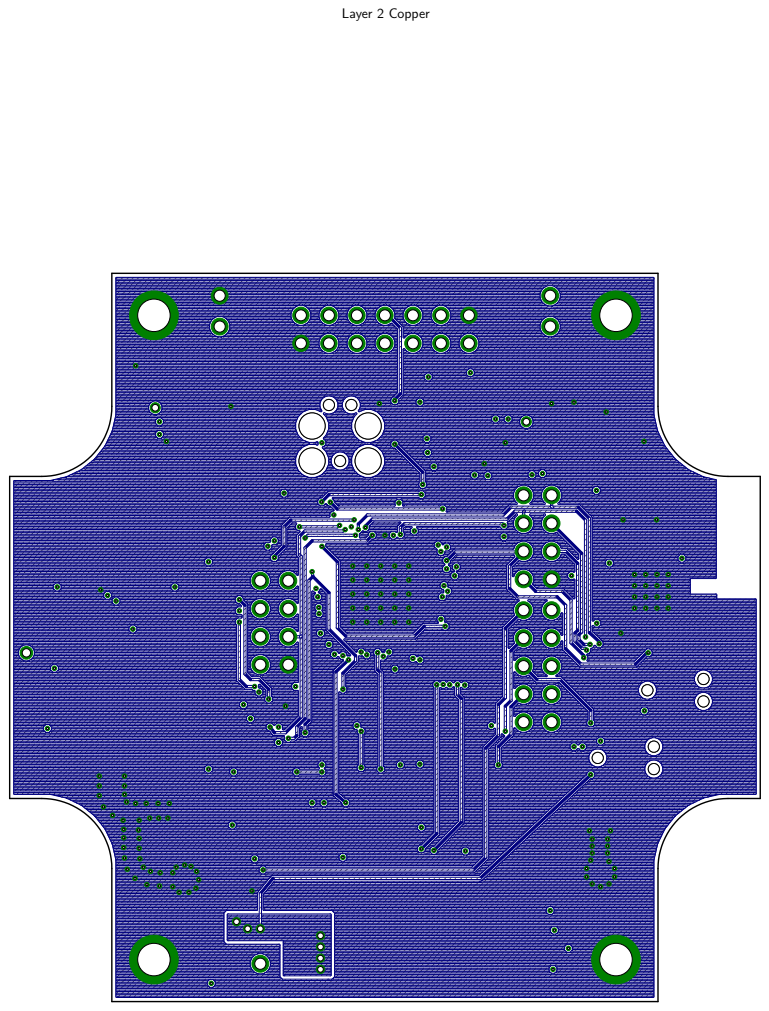
[picture p188: page 11]

## Layer 3 Copper

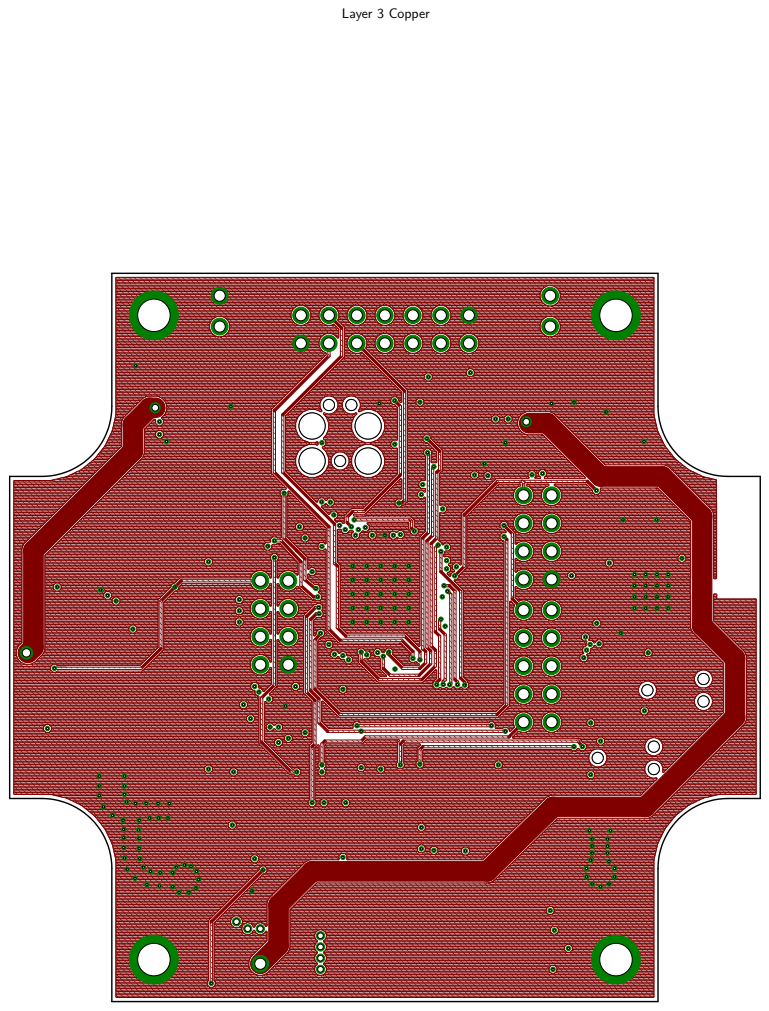
[picture p189: page 12]

## Bottom Copper Layer

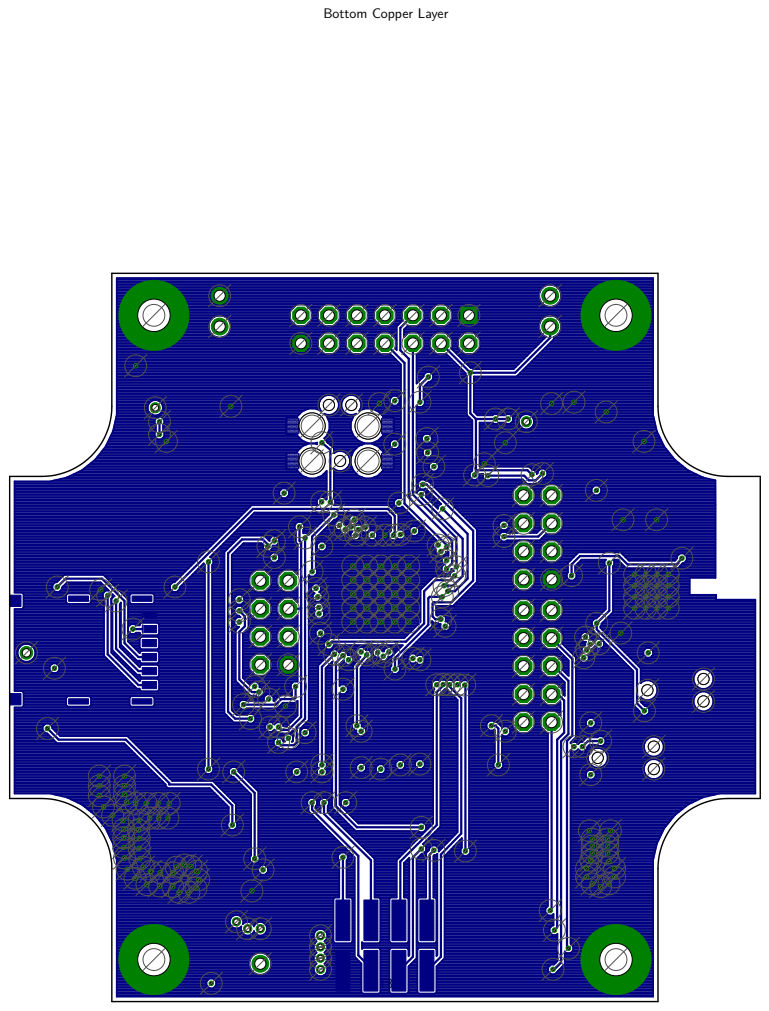
[picture p190: page 13]

## Top Paste Layer with Silkscreen

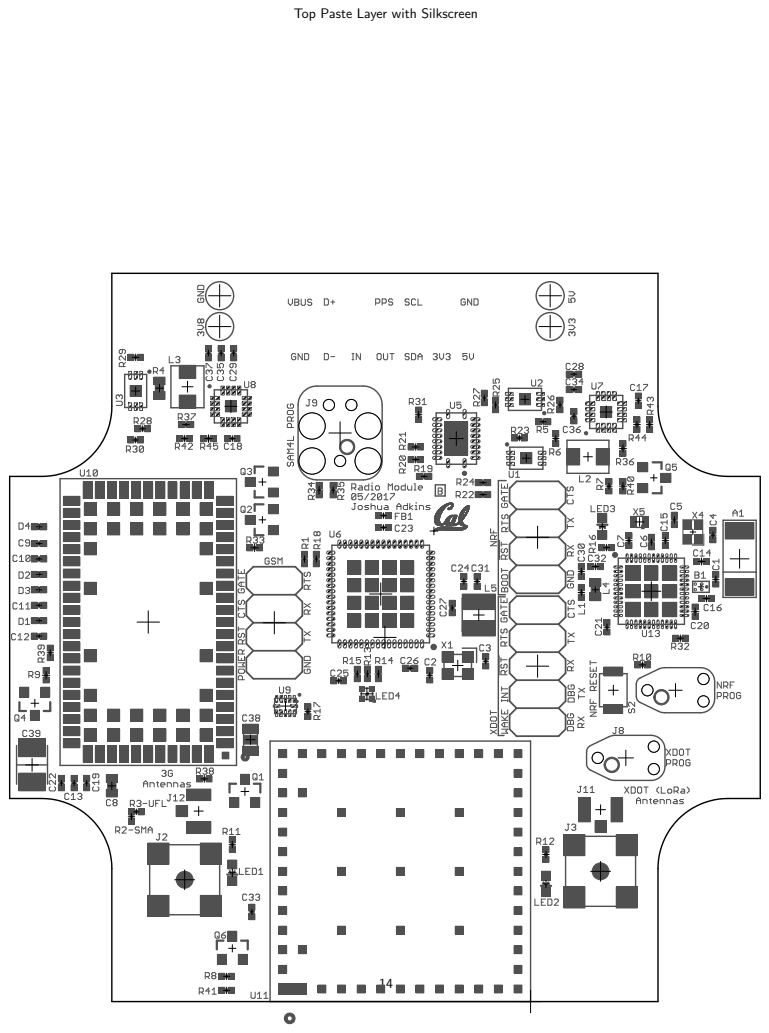
[picture p191: page 14]

## Bottom Paste Layer with Silkscreen

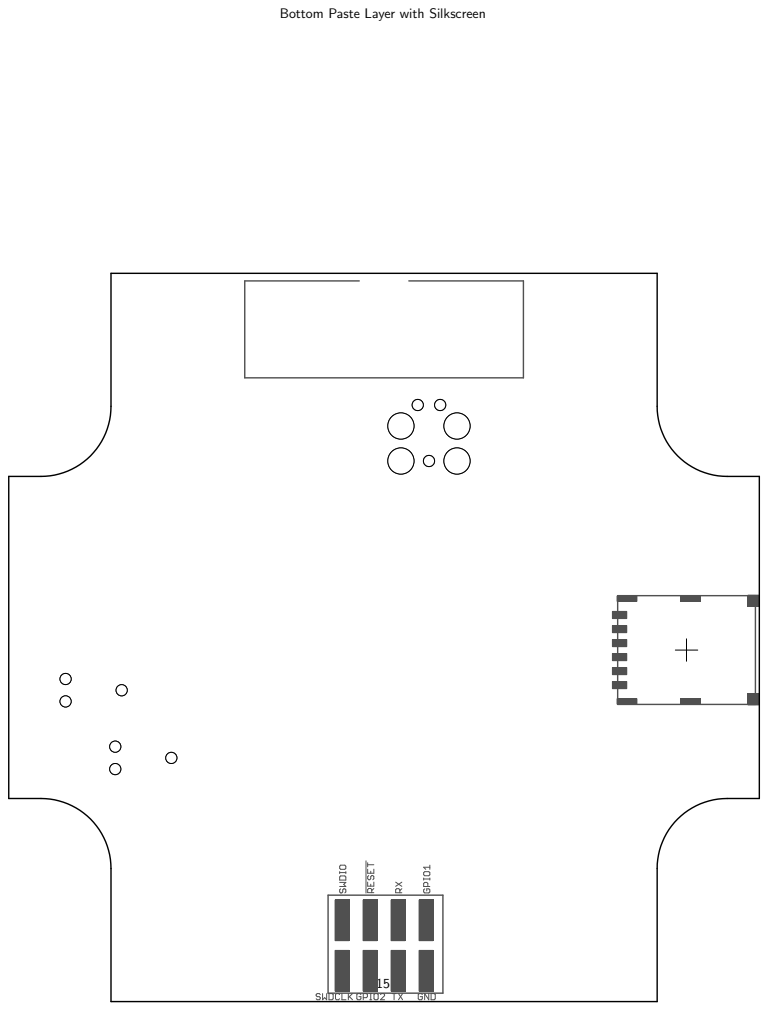
[picture p192: page 15]

## Top and Bottom Layers 1:1 Scale

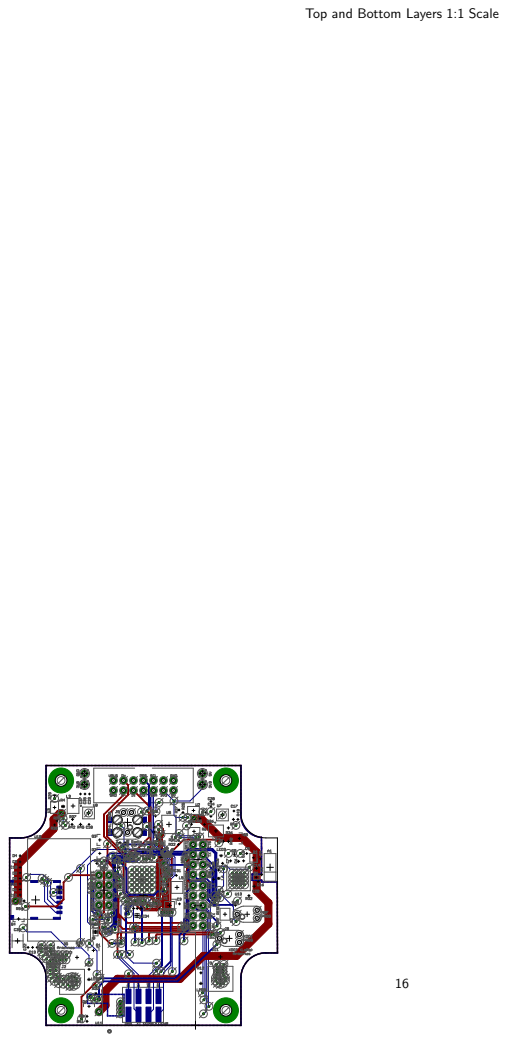
[picture p193: page 16]

## Top Layer 1:1 Scale

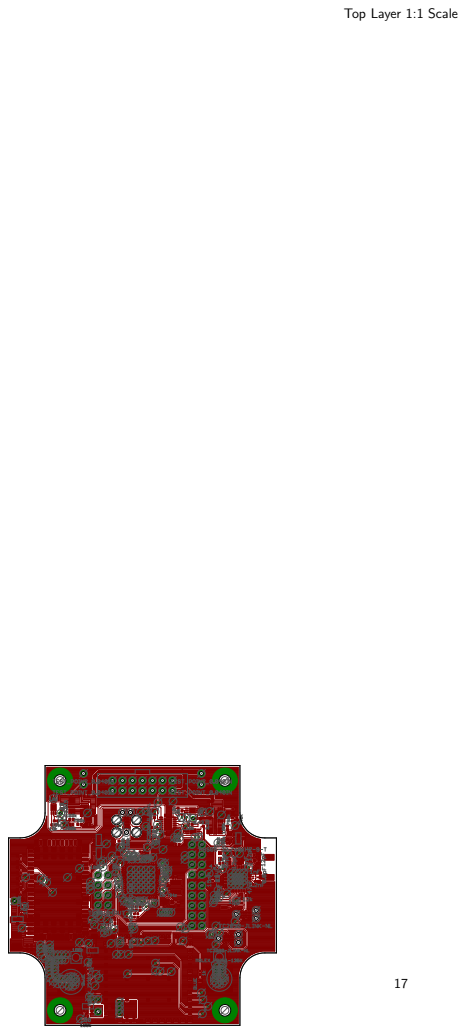
[picture p194: page 17]

## Layer 2 Copper 1:1 Scale

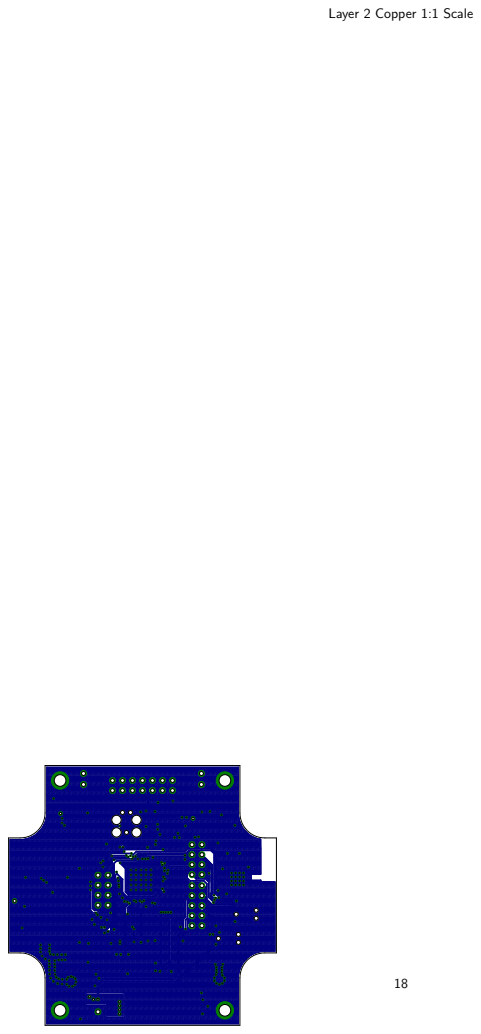
[picture p195: page 18]

## Layer 3 Copper 1:1 Scale

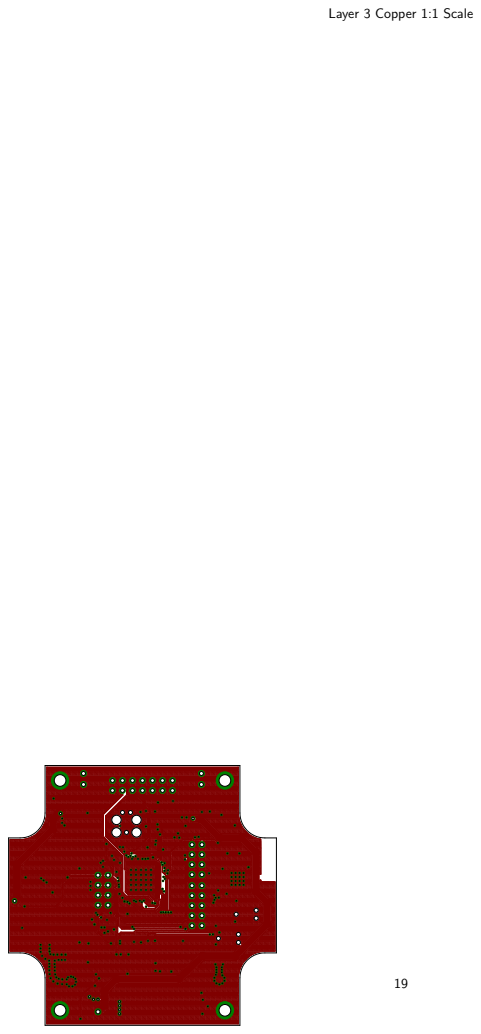
[picture p196: page 19]

## Bottom Copper Layer 1:1 Scale

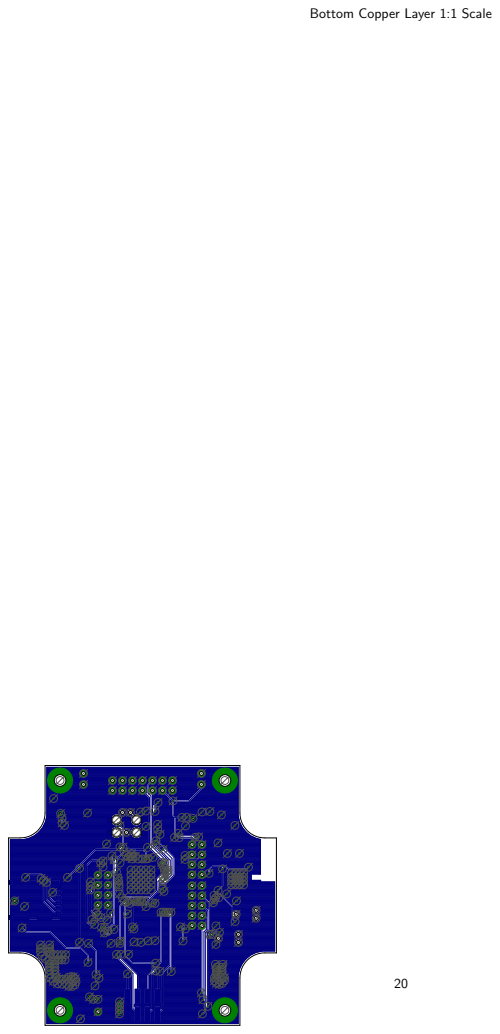
[picture p197: page 20]
