lab11/signpost/modules/rf_spectrum/rev_a/rf_spectrum.pdf

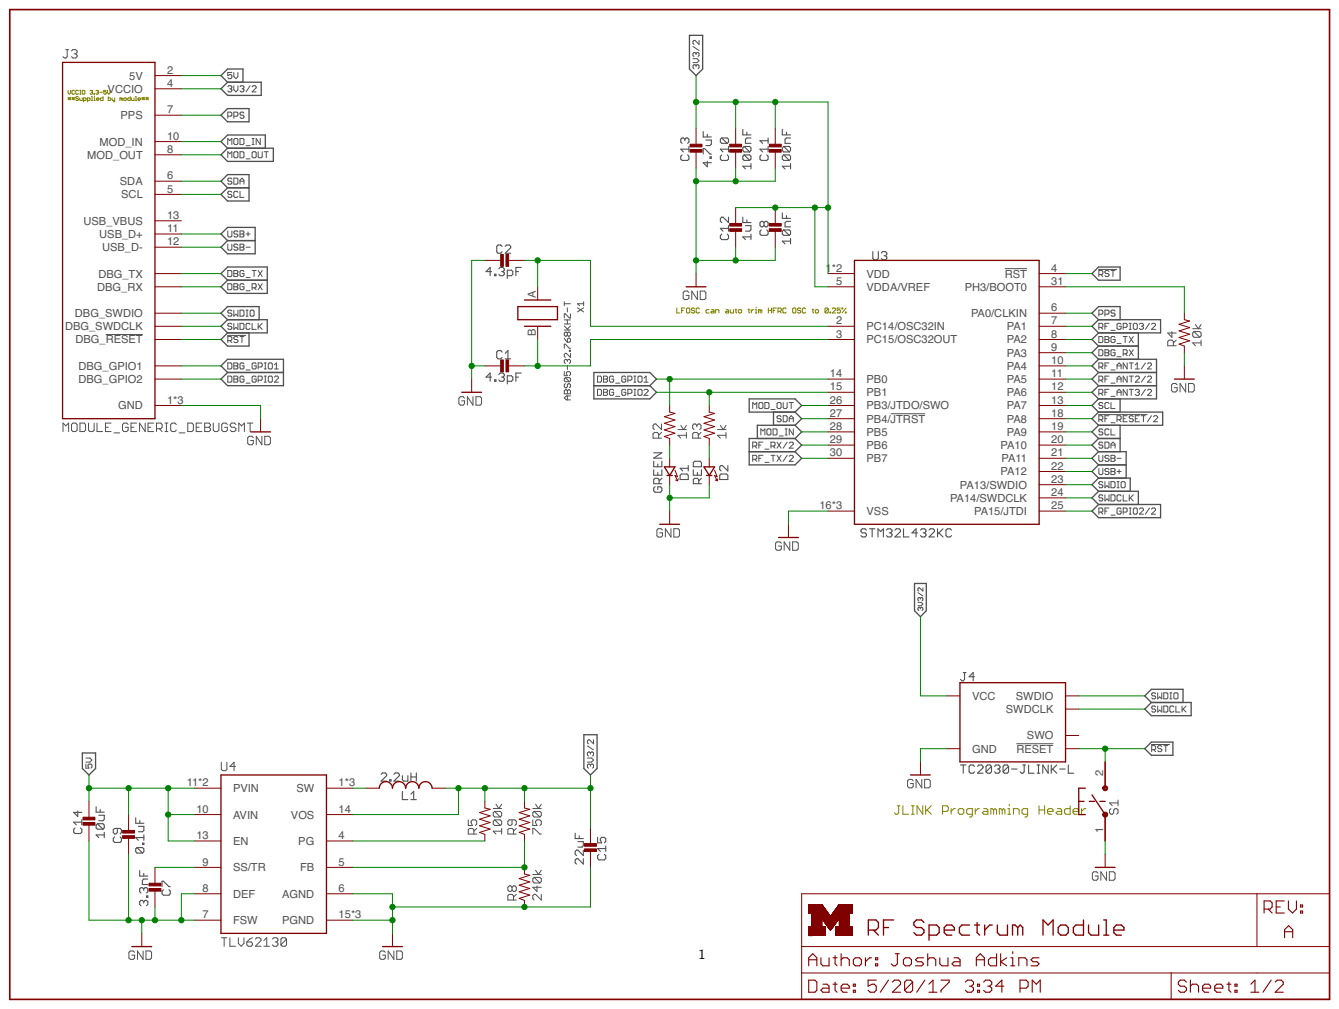
[picture p198: page 1]
SWDIO SWDCLK SWO RESET VCC GND 5V; 2 GND; 1*3 MOD_OUT; 8 SDA; 6 SCL; 5 USB_D+; 11 USB_D-; 12 PPS; 7 USB_VBUS; 13 VCCIO; 4 MOD_IN; 10 DBG_TX DBG_RX DBG_GPIO1 DBG_GPIO2 DBG_RESET DBG_SWDCLK DBG_SWDIO; PVIN 11*2; AVIN 10; DEF 8; FSW 7; 1*3 VOS; 5 AGND; 6 PGND; 1 2 VDD 1*2; VSS 16*3; VDDA/VREF 5; PC14/OSC32IN 2; PC15/OSC32OUT 3; RST; 4 PH3/BOOT0; 31 PA0/CLKIN; 22 PA13/SWDIO; 23 PA14/SWDCLK; PB3/JTDO/SWO 26; PB4/JTRST 27; PA15/JTDI

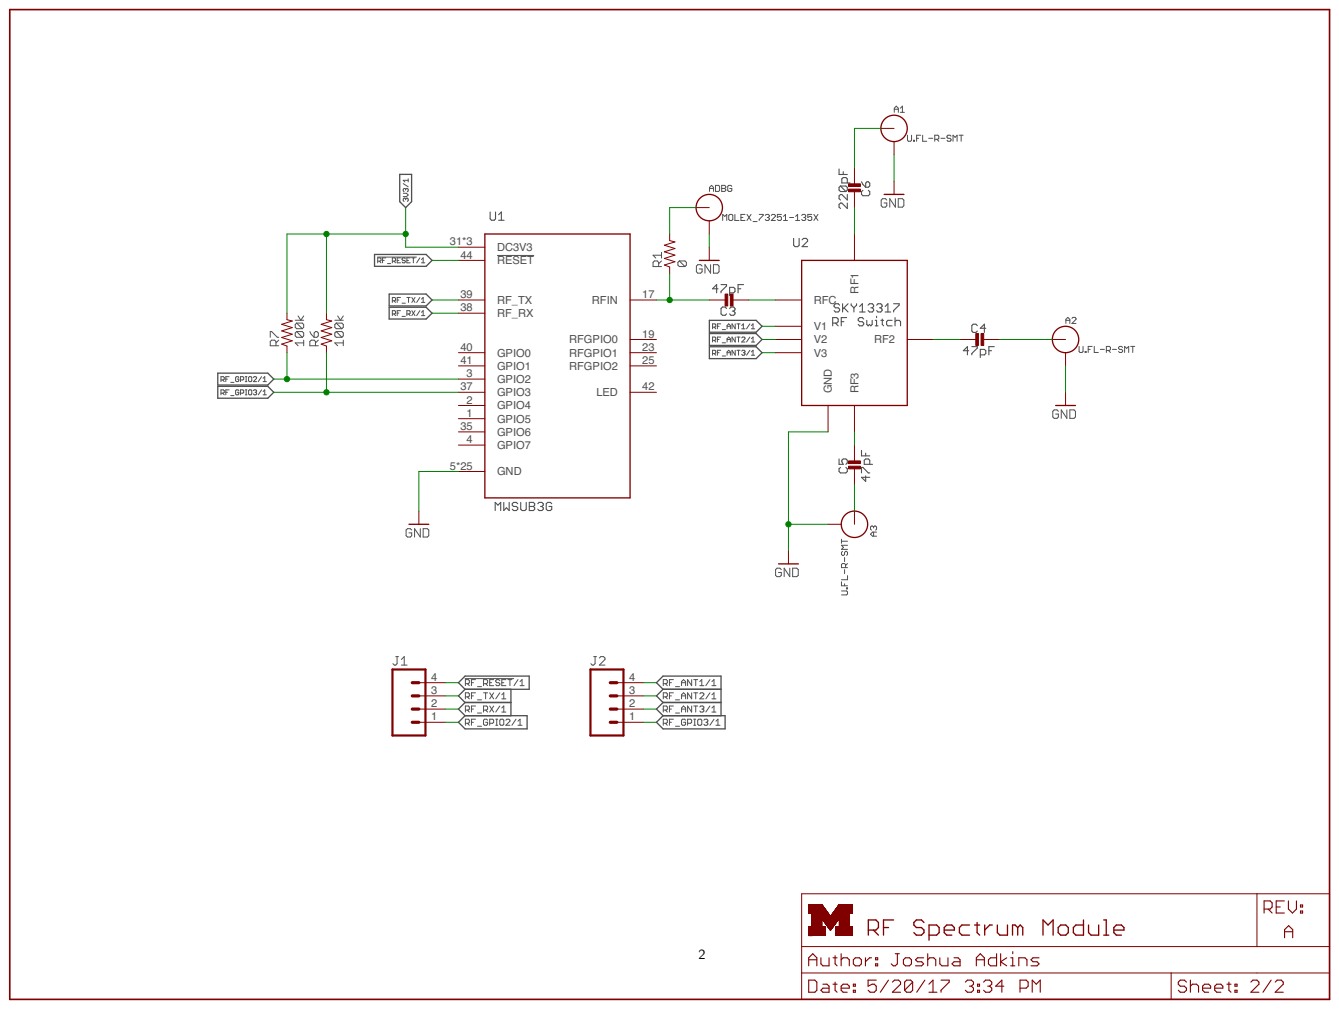
[picture p199: page 2]
2 GND 5*25; RFGPIO0; 19 RFIN; 17 RFGPIO1; 23 GPIO7 4; GPIO2 3; GPIO4 2; GPIO5 1; LED; 42 GPIO1 41; GPIO0 40; GPIO3 37; GPIO6 35; RESET 44; RFGPIO2; RFC V1V2V3; RF2 RF3 GND 1234 1234

## Top and Bottom Layers

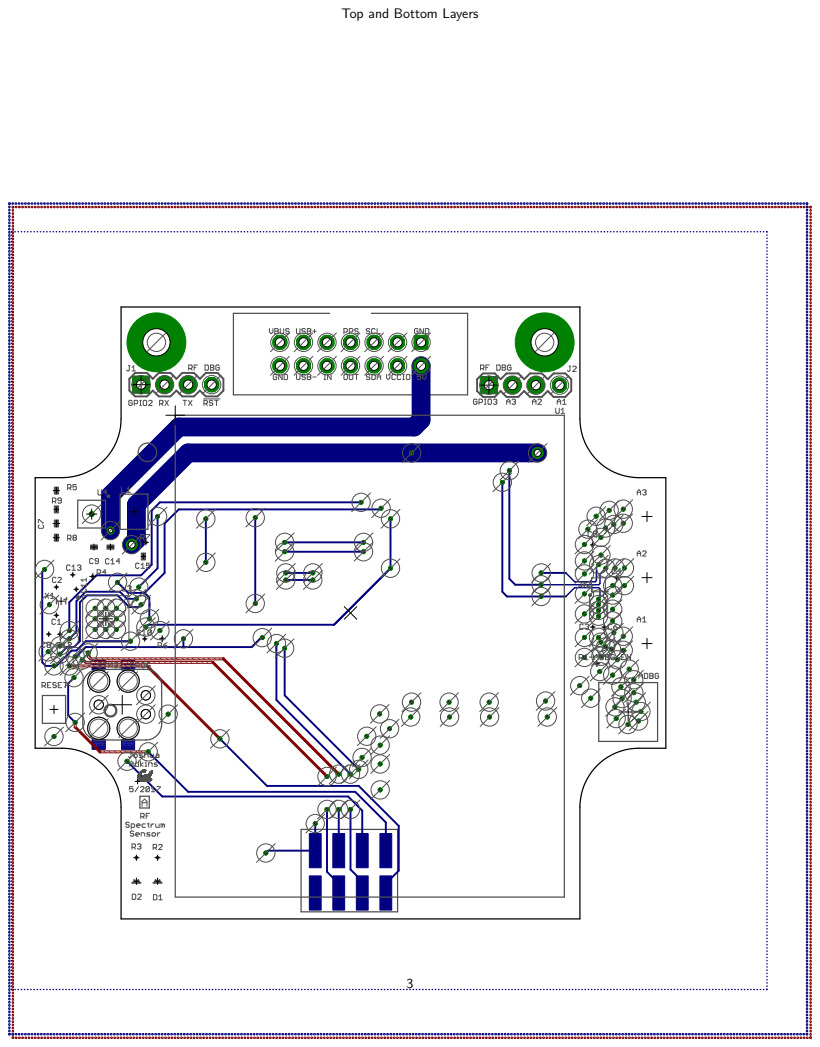
[picture p200: page 3]

## Top Layer

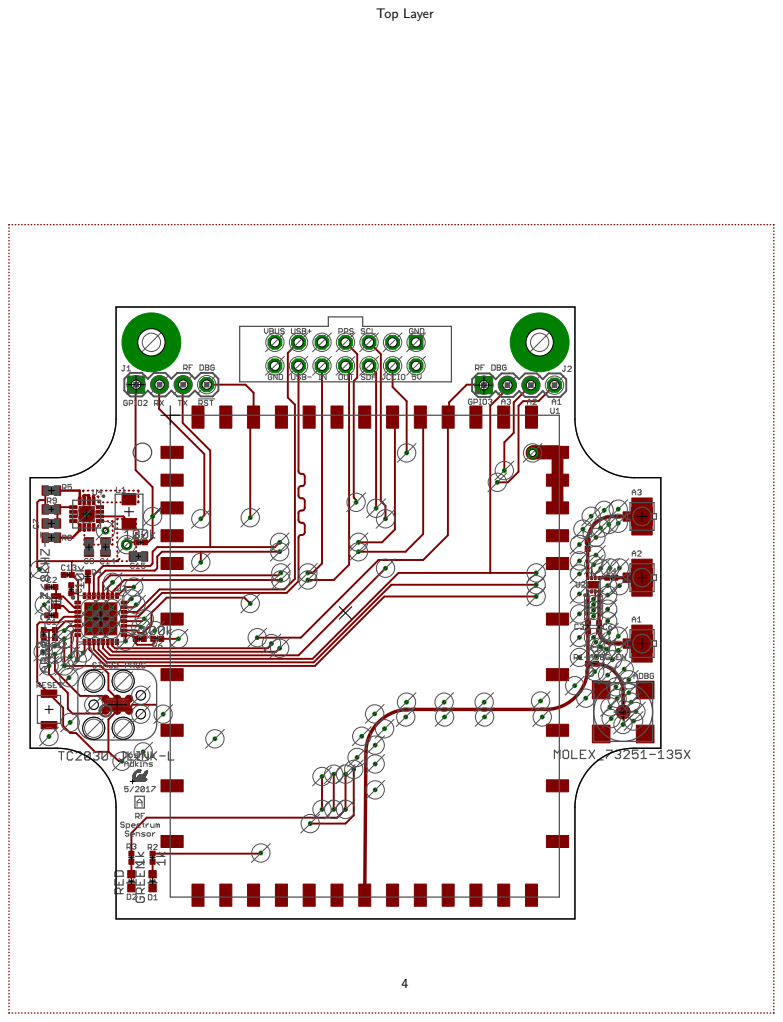
[picture p201: page 4]

## Bottom Layer

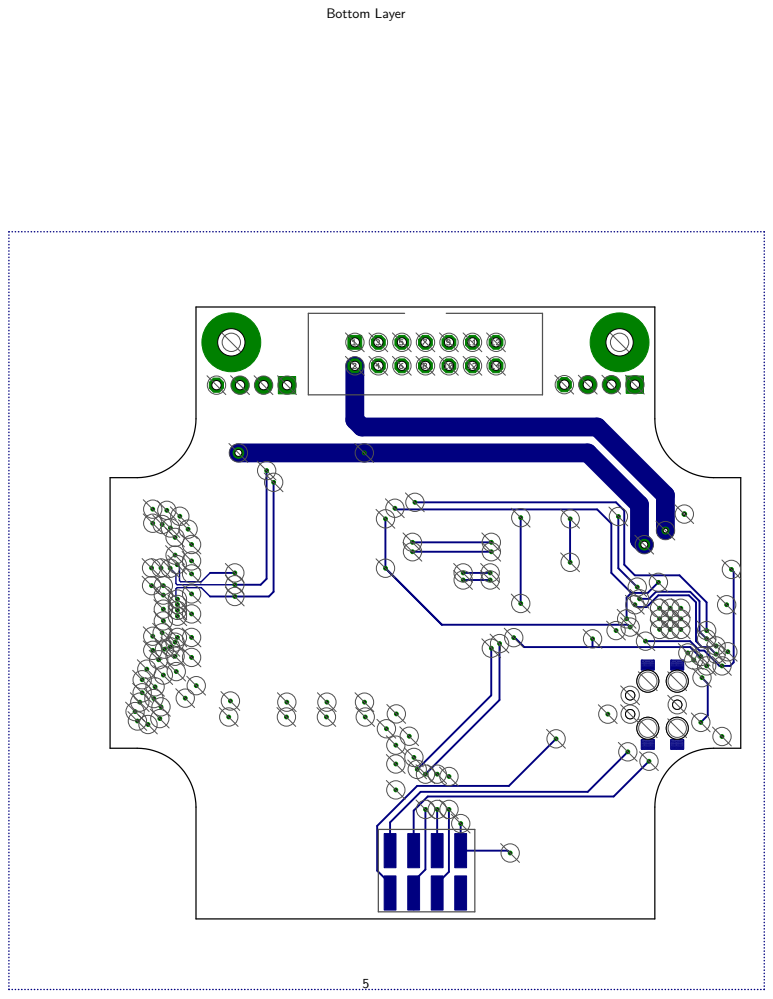
[picture p202: page 5]

## Top Copper Layer

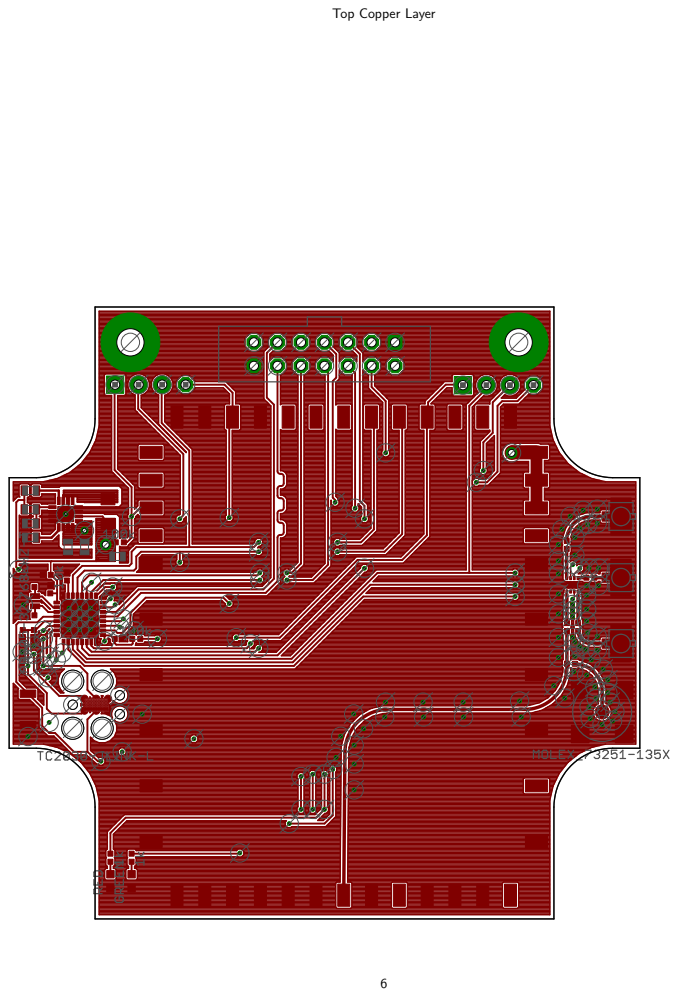
[picture p203: page 6]

## Layer 2 Copper

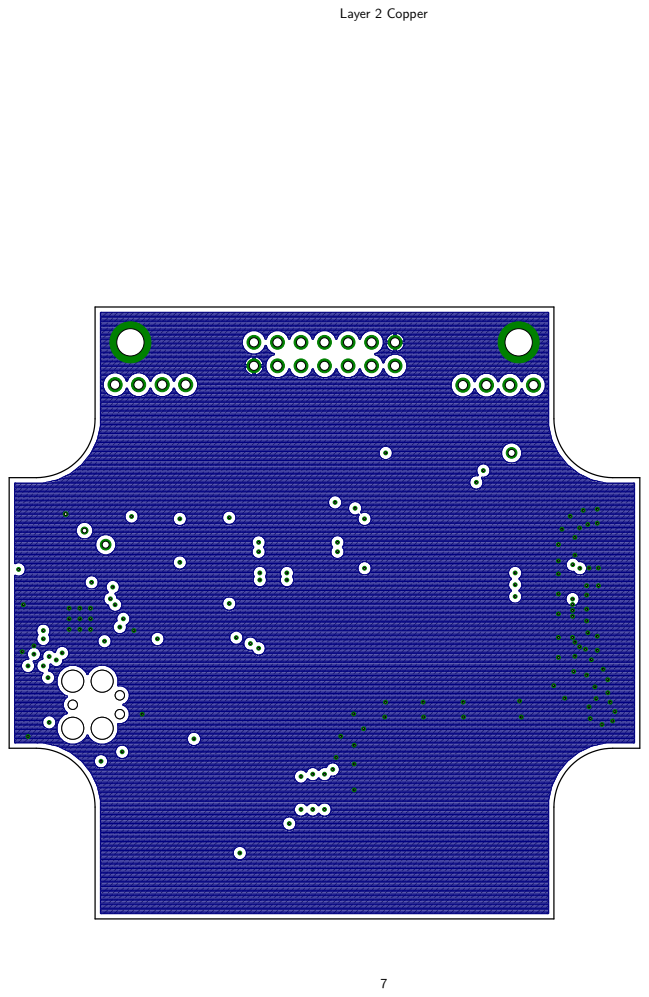
[picture p204: page 7]

## Layer 3 Copper

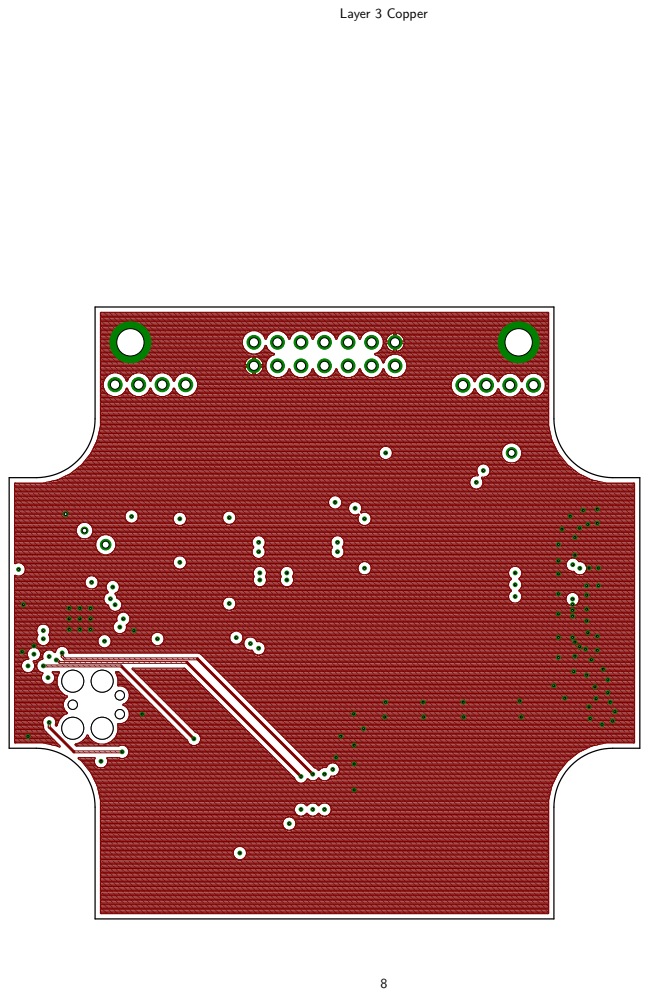
[picture p205: page 8]

## Bottom Copper Layer

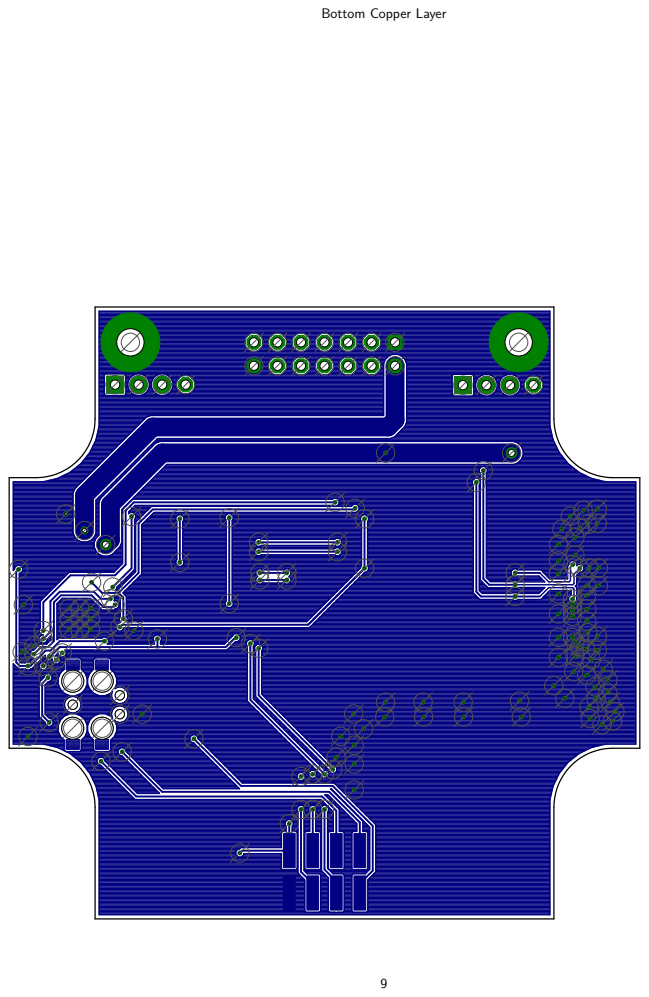
[picture p206: page 9]

## Top Paste Layer with Silkscreen

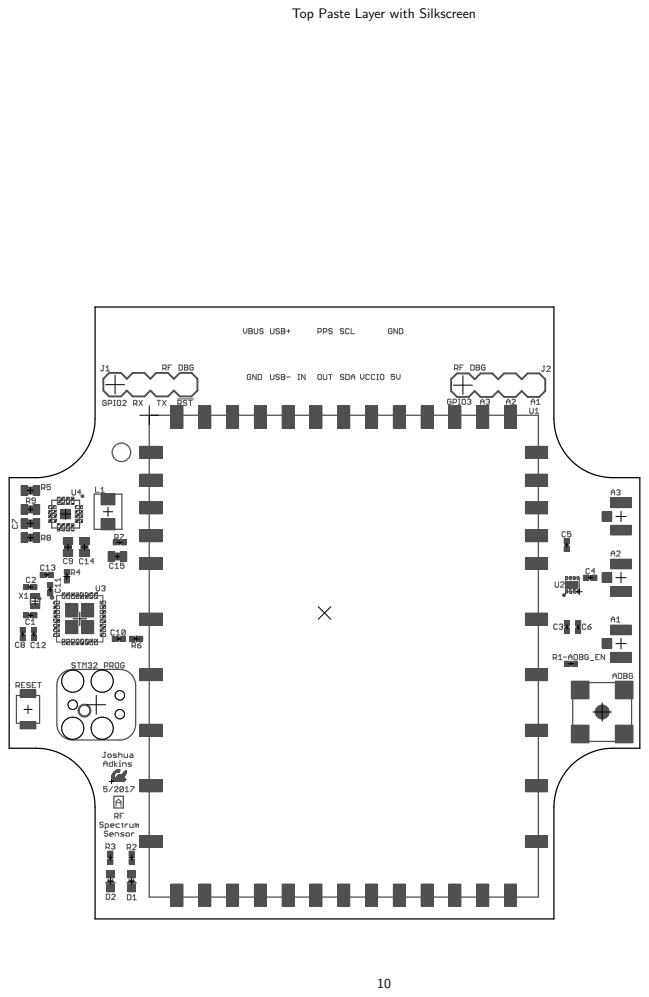
[picture p207: page 10]

## Bottom Paste Layer with Silkscreen

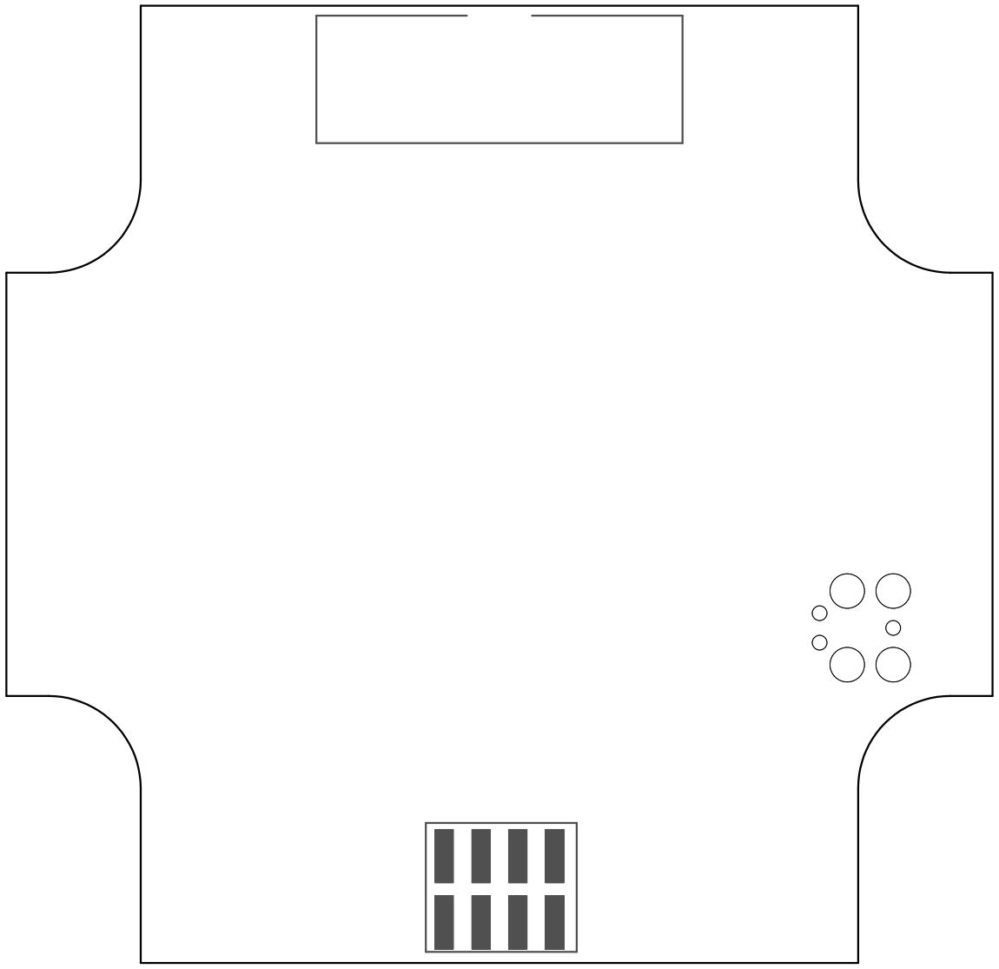
[picture p208: figure]

## Top and Bottom Layers 1:1 Scale

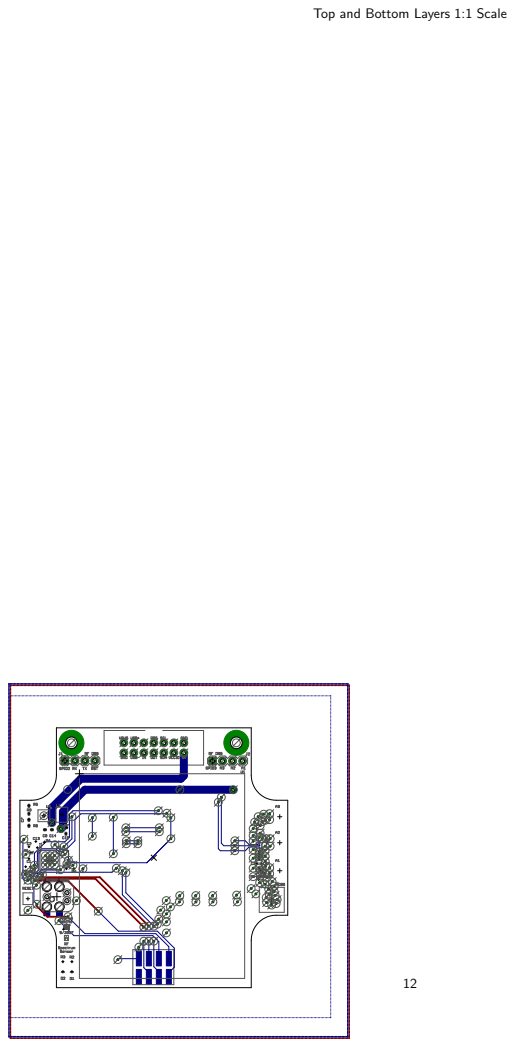
[picture p209: page 12]

## Top Layer 1:1 Scale

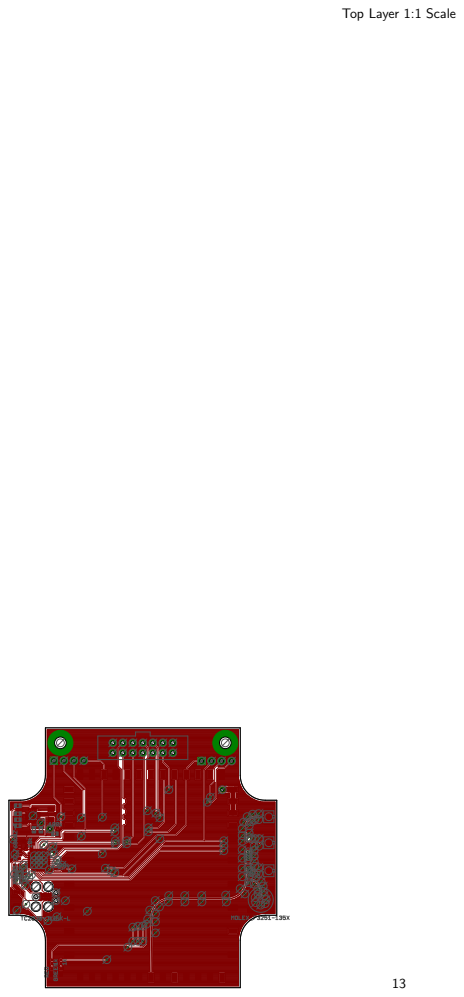
[picture p210: page 13]

## Layer 2 Copper 1:1 Scale

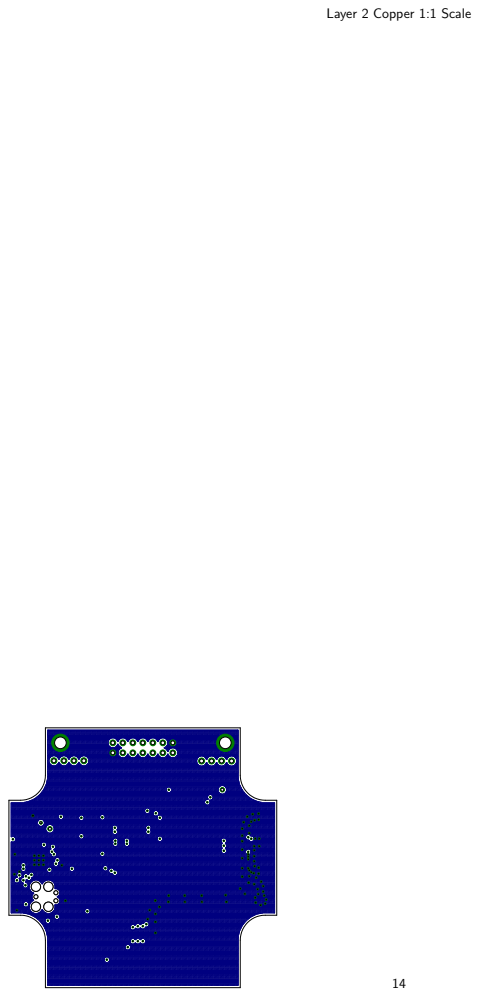
[picture p211: page 14]

## Layer 3 Copper 1:1 Scale

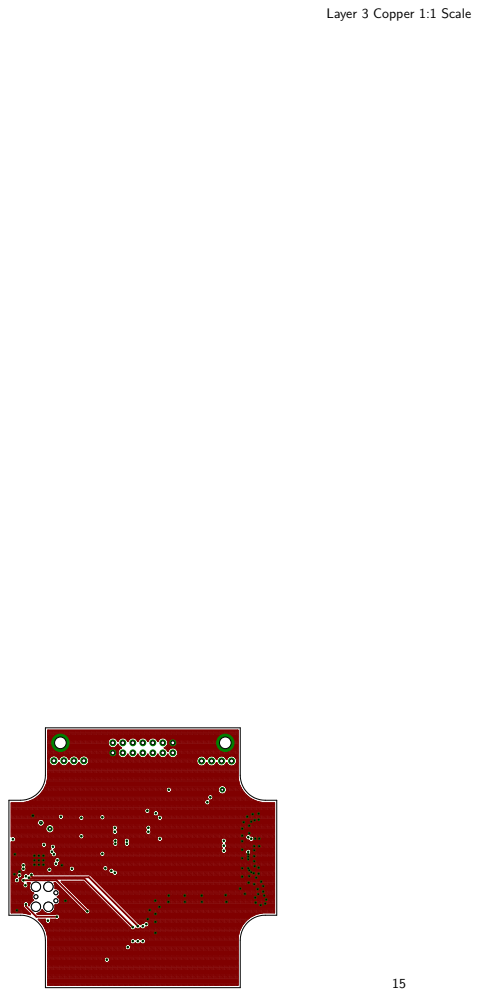
[picture p212: page 15]

## Bottom Copper Layer 1:1 Scale

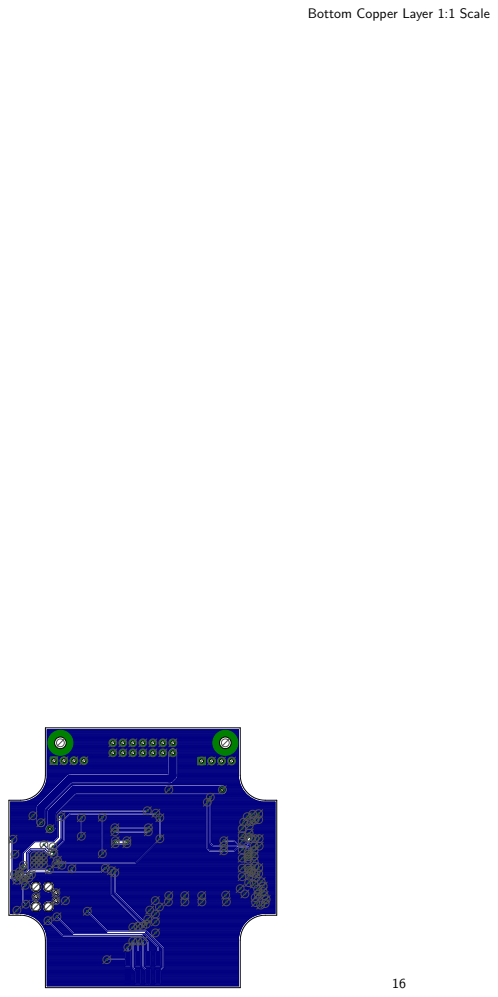
[picture p213: page 16]
