lab11/signpost/hardware/radio_module/rev_a/radio_module.pdf

Address mux for energy gauges



Configured to be Normally off. Can switch R37/R36

to make Normally on.

UART lines for commands

UART AUX Lines for Programming

P$39 SIM_CLK

Connector for FW upgrade


Configured to be normally off. Switch R38/R39 to be normally on.

NUCLEUM_RX/1 NUCLEUM_TX/1
The UART Lines allow for the NRF to act as a serial slave. This code is provided
by nordic and requires rts/cts. We would
like to use spi in the futue, then rts and
cts will be repurposed as interrupt pins
for the spi interface.


To Program the STM32L on the Module

Configured to be normally off. Switch R40/R41 to be normally on.

Q7 R³⁶ R³⁷ MISO/4 MOSI/4 SCLK/4

GND
A back-up interface incase the STM32 needs to go directly on the bus

To reprogram from the sam4L To receive radio packets

# Top and Bottom Layers 6 TX RX SDA SCL INT SMBUS


# Top Layer 7 TX RX SDA SCL INT SMBUS


Bottom Layer


Top Copper Layer

Layer 2 Copper

Layer 3 Copper


Bottom Copper Layer

SDA SCL INT SMBUS

Top Paste Layer with Silkscreen

Bottom Paste Layer with Silkscreen

SDA SCL INT SMBUS

Top and Bottom Layers 1:1 Scale


Top Layer 1:1 Scale


Layer 2 Copper 1:1 Scale


Layer 3 Copper 1:1 Scale


Bottom Copper Layer 1:1 Scale

### radio_module

Part Value | Device | Package
C1 | 8pF | CAPACITOR0402_CAP | 0402_CAP
C2 | 8pF | CAPACITOR0402_CAP | 0402_CAP
C3 | 33pF | CAPACITOR0603_CAP | 0603_CAP
C4 | 47pF | CAPACITOR0402_CAP | 0402_CAP
C5 | 47pF | CAPACITOR0402_CAP | 0402_CAP
C6 | 47pF | CAPACITOR0402_CAP | 0402_CAP
C7 | 47pF | CAPACITOR0402_CAP | 0402_CAP
C8 | 56pF | CAPACITOR0402_CAP | 0402_CAP
C9 | 3.3nF | CAPACITOR0402_CAP | 0402_CAP
C10 3.3nF | CAPACITOR0402_CAP | 0402_CAP
C11 10nF | CAPACITOR0402_CAP | 0402_CAP
C12 0.1uF | CAPACITOR0402_CAP | 0402_CAP
C13 0.1uF | CAPACITOR0402_CAP | 0402_CAP
C14 100nF | CAPACITOR0402_CAP | 0402_CAP
C15 100nF | CAPACITOR0402_CAP | 0402_CAP
C16 100nF | CAPACITOR0402_CAP | 0402_CAP
C17 100nF | CAPACITOR0402_CAP | 0402_CAP
C18 100nF | CAPACITOR0402_CAP | 0402_CAP
C19 100nF | CAPACITOR0402_CAP | 0402_CAP
C20 100nF | CAPACITOR0402_CAP | 0402_CAP
C21 1uF | CAPACITOR0402_CAP | 0402_CAP
C22 4.7uF | CAPACITOR0402_CAP | 0402_CAP
C23 10uF | CAPACITOR0402_CAP | 0402_CAP
C24 10uF | CAPACITOR0402_CAP | 0402_CAP
C25 22uF | CAPACITOR0402_CAP | 0402_CAP
C26 22uF | CAPACITOR0402_CAP | 0402_CAP
C27 220uF | CAPACITOR1210_CAP | 1210_CAP
D1 | | DIODE_ZENER | 0402_DIODE
D2 | | DIODE_ZENER | 0402_DIODE
D3 | | DIODE_ZENER | 0402_DIODE
D4 | | DIODE_ZENER | 0402_DIODE
FB4 1.5k | FERRITE_BEAD0402 | 0402_CAP
J1 | MODULE_GENERIC | MODULE_GENERIC | MODULE_GENERIC
J4 | NANO_SIM | NANO_SIM | WURTH_NANO_SIM
JP1 | | M02PTH | 1X02
L1 | 2.2uH | INDUCTORIHL | IHL-1212BZ-11
L2 | 2.2uH | INDUCTORIHL | IHL-1212BZ-11
L3 | 22uH | LHQ3NP | 1212
LED1LED0603 | LED0603 | LED-0603
LED2LED0603 | LED0603 | LED-0603
P1 | MOLEX_73251-135X | MOLEX_73251-135X | SMA-J/PCB
P2 | MOLEX_73251-135X | MOLEX_73251-135X | SMA-J/PCB
Q1 MOSFET-NCHANNELXFDN-3 MOSFET-NCHANNELXFDN-3 XFDFN-3 Q2 MOSFET-NCHANNELXFDN-3 MOSFET-NCHANNELXFDN-3 XFDFN-3 Q3 MOSFET-NCHANNELXFDN-3 MOSFET-NCHANNELXFDN-3 XFDFN-3 Q4 MOSFET-NCHANNELXFDN-3 MOSFET-NCHANNELXFDN-3 XFDFN-3
Q5 SI223DDS | SI223DDS | SOT23-3
Q6 SI223DDS | SI223DDS | SOT23-3

### radio_module

Q7 SI223DDS | SI223DDS | SOT23-3
R1 | | 0 RESISTOR0402_RES | 0402_RES
R2 | | 0 RESISTOR0402_RES | 0402_RES
R3 | | 0 RESISTOR0402_RES | 0402_RES
R4 | | 0 RESISTOR0402_RES | 0402_RES
R5 | | 0.015 RESISTOR0603_RES | 0603-RES
R6 | | 0.43 RESISTOR0402_RES | 0402_RES
R7 | | 3.32 RESISTOR0402_RES | 0402_RES
R8 | 1k | RESISTOR0402_RES | 0402_RES
R9 | 1k | RESISTOR0402_RES | 0402_RES
R10 10k | RESISTOR0402_RES | 0402_RES
R11 10k | RESISTOR0402_RES | 0402_RES
R12 10k | RESISTOR0402_RES | 0402_RES
R13 10k | RESISTOR0402_RES | 0402_RES
R14 10k | RESISTOR0402_RES | 0402_RES
R15 10k | RESISTOR0402_RES | 0402_RES
R16 10k | RESISTOR0402_RES | 0402_RES
R17 10k | RESISTOR0402_RES | 0402_RES
R18 10k | RESISTOR0402_RES | 0402_RES
R19 10k | RESISTOR0402_RES | 0402_RES
R20 10k | RESISTOR0402_RES | 0402_RES
R21 10k | RESISTOR0402_RES | 0402_RES
R22 10k | RESISTOR0402_RES | 0402_RES
R23 10k | RESISTOR0402_RES | 0402_RES
R24 10k | RESISTOR0402_RES | 0402_RES
R25 100k | RESISTOR0402_RES | 0402_RES
R26 100k | RESISTOR0402_RES | 0402_RES
R27 100k | RESISTOR0402_RES | 0402_RES
R28 100k | RESISTOR0402_RES | 0402_RES
R29 100k | RESISTOR0402_RES | 0402_RES
R30 100k | RESISTOR0402_RES | 0402_RES
R31 100k | RESISTOR0402_RES | 0402_RES
R32 100k | RESISTOR0402_RES | 0402_RES
R33 100k | RESISTOR0402_RES | 0402_RES
R34 100k | RESISTOR0402_RES | 0402_RES
R35 100k | RESISTOR0402_RES | 0402_RES
R36 100k | RESISTOR0402_RES | 0402_RES
R37 100k | RESISTOR0402_RES | 0402_RES
R38 200k | RESISTOR0402_RES | 0402_RES
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
High Efficient 3A switching st 296-35978-1-ND
I2C Battery Gas Gauge | LTC2941IDCB#TRMPBFCT-ND
I2C Battery Gas Gauge | LTC2941IDCB#TRMPBFCT-ND
Lora Radio module by IMST
1-4 I2C/SMBUS Multiplexer wit296-20960-1-ND
High Efficient 3A switching st 296-35978-1-ND

### radio_module

I2C Battery Gas Gauge | LTC2941IDCB#TRMPBFCT-ND
6 channel level translator | 296-23868-2-ND
SAM4L Microcontroller. 64QFATSAM4LC8BA-MURDKR-ND Sara G350 2.5G Radio Module
Pericom Type FH 16 MHz 2.5FH1600015CT-ND
