lab11/signpost/hardware/power_supply_module/rev_a/power_supply_module.pdf

# Power Module Header

SIGNPOST PO; WER M; ODULE; GND; MODULE_POWER; VSOL+; 19 VSOL-; 20 VBATT+; 17 VBATT-; VCC_CONTROLLER; 2 VCC_LINUX 4 VCC_BACKPLANE 13 SMBDATA; 3 SMBCLK 5 SMBALERT 6 VCC_MOD0; 7 VCC_MOD1 8 VCC_MOD2 9 VCC_MOD5 10 VCC_MOD6 11 VCC_MOD7 12; VBATT/2.4G; VCC_BACKPLANE/7.4G; VCC_LINUX/7.8F; VCC_MOD0/7.8I VCC_MOD2/8.8C; VCC_MOD5/8.8F VCC_MOD6/8.8I VCC_MOD7/8.8L; VCC_MOD1/7.8L; SDA/7.4G SCL/7.4G INT/7.4H

# 3v3 Rail

GND; 2.2u C¹⁹; C²⁴; L1 PVIN; AVIN; DEF; FSW; 1*3 VOS; 5 AGND; 6 PGND; TLV62130; VBATT/1.8G

# 5v Rail 1


# 5v Rail 2


# 5v Rail 3


# 5v Rail 4


7 Coulomb Counters For MOD0-2,5; PCA9544A; LTC2941 0.1u 0.017; LTC2941 GND A0 1; INT0; 6 INT1; 9 GND 10; INT2; 13 INT3; 16 INT 17; SCL 18; SDA 19; VCC 20 U6; C¹¹ R¹; SENSE+ 1; SENSE- 6; SDA 4; SCL 3; ALERT 5; GND 2; U8 C¹² R²; U9 C¹³ R³; U10 C¹⁴ R⁴; U11 VCC_BACKPLANE/1.7H; VCC_BACKPLANE/1.7H SDA/1.7H SCL/1.7I INT/1.7I; 5V_1/3.9G 3V3/2.9G VCC_LINUX/1.7H VCC_MOD0/1.7I VCC_MOD1/1.7J 5V_2/4.9G 5V_2/4.9G

8 Coulomb Counters For MOD6-7, LINUX, BACKPLANE/CONTROLLER PCA9544A; LTC2941 0.1u 0.017; LTC2941 GND A0 1; INT0; 6 INT1; 9 GND 10; INT2; 13 INT3; 16 INT 17; SCL 18; SDA 19; VCC 20 U7; C¹⁵ R⁵; SENSE+ 1; SENSE- 6; SDA 4; SCL 3; ALERT 5; GND 2; U12 C¹⁶ R⁶; U13 C¹⁷ R⁷; U14 C¹⁸ R⁸; U15 VCC_BACKPLANE/7.8C; SDA/7.4G SCL/7.4G INT/7.4H; 5V_3/5.9G 5V_3/5.9G 5V_4/6.9G 5V_4/6.9G VCC_MOD2/1.7J VCC_MOD5/1.7J VCC_MOD6/1.7J VCC_MOD7/1.7K

# Debugging



Top and Bottom Layers

Top Layer

Bottom Layer


Top Copper Layer


Bottom Copper Layer


Top Paste Layer with Silkscreen

Bottom Paste Layer with Silkscreen


Top and Bottom Layers 1:1 Scale


Top Layer 1:1 Scale


Bottom Copper Layer 1:1 Scale

## power_supply_module

Qty Value | Device | Package
8 | 0.017 RESISTOR0805_RES 0805_RES
5100k | RESISTOR0402_RES 0402_RES
4130k | RESISTOR0402_RES 0402_RES
1240k | RESISTOR0402_RES 0402_RES
4680k | RESISTOR0402_RES 0402_RES
1750k | RESISTOR0402_RES 0402_RES
53.3n | CAPACITOR0402_CAP 0402_CAP
130.1u | CAPACITOR0402_CAP 0402_CAP
510u | CAPACITOR0603_CAP 0805_CAP
522u | CAPACITOR0603_CAP 0603_CAP
52.2u | INDUCTORIHL | IHL-1212BZ-11
5 TLV62130 | TLV62130 | TQFN-16/3MM
2 PCA9544A | PCA9544A | SO20L
8LTC2941 | LTC2941 | DFN-6-2MMX3MM

## power_supply_module

### Parts R1, R2, R3, R4, R5, R6, R7, R8 R9, R10, R11, R12, R13 R14, R15, R16, R17

R18

### R19, R20, R21, R22

R23

### C1, C2, C3, C4, C5 C6, C7, C8, C9, C10, C11, C12, C13, C14, C15, C16, C17, C18 C19, C20, C21, C22, C23 C24, C25, C26, C27, C28 L1, L2, L3, L4, L5 U1, U2, U3, U4, U5

U6, U7

### U8, U9, U10, U11, U12, U13, U14, U15

## power_supply_module

Description | DIGIKEY
Resistor | WSLPB-.017CT-ND
Resistor | P100KJCT-ND
Resistor | P130KLCT-ND
Resistor | P240KLCT-ND
Resistor | P680KLCT-ND
Resistor | P750KLCT-ND
0402 Capacitor | 490-3248-1-ND
0402 Capacitor | 490-5920-1-ND
0805 Capacitor | 490-5523-1-ND
0603 Capacitor | 1276-1193-1-ND
A very specific inductor | 541-1322-1-ND
High Efficient 3A switching step-down regulator. 1V-5V out, 4V-17V in. | 296-35978-1-ND

### 1-4 I2C/SMBUS Multiplexer with interrupt for power supply coulomb counters296-20958-1-ND

I2C Battery Gas Gauge | LTC2941IDCB#TRMPBFCT-ND
