lab11/signpost/hardware/backplane/rev_c/quotes/invoice.pdf

Sold To.; University of Michigan; L/C ISSUING BANK; Ship To ( Same as Sold to unless indicated); SHIPPING MARK; Tel : 31-206-325789; Atten : Mr. Pa Pannuto; Carrier; By Air; Printed Circuit Board; Backplane c to assember; size; 254.00mmx381.00mm; Metal mask(two sheets); Incheon / Korea; G.T. HAN; Shipping Port; destination

U & I 301-1007, BucheonTechnopark SsangYoug 3-cha SamJung-dong, Ojung-gu, Bucheon-city, Kyunggi-do South-Korea Tel 82-32-624-4427 Fax. +82-32-624-4429 | Proforma INVOICE | INVICE NO # UI-170517-1-Pro | PAGE

DATE May. 17, 2017 | 1 OF 1

2260 Hayward 4908 BBB Ann Arbor
Michigan U.S.A 48109
University of Michigan

MADE IN KOREA

Remarks Notify : The same as above(Ship to) | TERMS OF PAYMENT T/Tl in advance

H.S. No. P/O. No. | D E S C R I P T I O N | Q'TY(pcs) | UNIT PRICE FOB KOREA | AMOUNT

FR-4 2.0mm(0.08") 2 layers Cu 1/1 oz ENIG black soldermask
Assembly boards

Components
shipping
14 working days delivery from payment

Bank information for your payment(wire transfer) as follows:
Bank Name : Industrial Bank of Korea, DoDang-Dong Branch
Bank address : 213 DoDang-Dong, Wonmi-ku Bucheon-City Kyunggi-Do, Korea
Account No. : 164-050-754-04-010
Beneficiary : U& I
Swift Code(Bank code) : IBKO KR SE
VAT No 130 05 41646

Payment by T/T in advance only
