lab11/signpost/modules/microwave_radar/hardware/rev_a/microwave.pdf

1SAM4L CHIP HEADER; JLINK PROGRAMMER; OSCILLATOR VCCIO 3.3-5V **Supplied by module**; SAM4LC8AA; 8pF 8pF GND GND; TC2030-JLINK-L GND; 10k MODULE_GENERIC; +3V³ ⁺³V³ ⁺³V ⁺; 3 5V GND; 1k GND ¹k; +3V³ LED⁰⁶⁰³ LED⁰⁶⁰³ ⁺³V³ GND 6*4; VDDCORE 5; VDDOUT 7; VDDIN 8; ADVREFP 18; VDDANA 19; VDDIO 40*2; GNDANA 17; RESET; 4 TCK; 9 XIN32; 13 XOUT32; 47 VLCDIN 31; VLCD 27; BIASL 29; BIASH 28; CAPL 26; CAPH 25 U1; GND; C1 C2 SWDIO SWDCLK SWO RESET VCC GND J2; R⁸ C¹¹; C¹²; C¹³L3; 1.5k C¹⁴; L2C¹⁵; C¹⁶; 2 GND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


3 Switching regulator from 5V to 3.3 V SEVEN BAND GRAPHIC EQUALIZER; 100k GND; 750k 240k GND; GND⁺³V³ GND; GND; +3V³ ¹⁰uF; 200k PVIN 11*2; AVIN 10; DEF 8; FSW 7; 1*3 VOS; 5 AGND; 6 PGND; 15*3 U2 TLV62130; R¹³ L1 C⁸; R¹⁷ R¹⁵ VDD; IN STROBE RESET OUT; CLK GND; VSS U3 MSGEQ7 C²¹; C²² C9; C¹⁰

Top and Bottom Layers 4 5V3V3 GND AMP_OUT MSGEQ_OUT IF | 5V³V3 I2C_D MOD_OUT MOD_IN | I2C_C PPS TXRX Power On | U5 JP²


Top Layer 5 5V3V3 GND AMP_OUT MSGEQ_OUT IF | 5V³V3 I2C_D MOD_OUT MOD_IN | I2C_C PPS TXRX Power On | U5 JP²


Bottom Layer


Top Copper Layer


Bottom Copper Layer

Top Paste Layer with Silkscreen 9 5V3V3 GND AMP_OUT MSGEQ_OUT IF | 5V³V3 I2C_D MOD_OUT MOD_IN | I2C_C PPS TXRX Power On | U5 JP²


Bottom Paste Layer with Silkscreen

11 ⁵V3V3 GND AMP_OUT MSGEQ_OUT IF; 5V³V3 I2C_D MOD_OUT MOD_IN; I2C_C PPS TXRX Power On; U5 JP²

Top and Bottom Layers 1:1 Scale


Top Layer 1:1 Scale


Bottom Copper Layer 1:1 Scale
