lab11/signpost/modules/microwave_radar/simulation/hb100_thir-PSpiceFiles/SCHEMATIC1/sim/sim.cir

** Profile: "SCHEMATIC1-sim"  [ C:\Users\apple\AppData\Roaming\SPB_Data\hb100_thir-pspicefiles\schematic1\sim.sim ] 

** Creating circuit file "sim.cir" 
** WARNING: THIS AUTOMATICALLY GENERATED FILE MAY BE OVERWRITTEN BY SUBSEQUENT SIMULATIONS

*Libraries: 
* Profile Libraries :
* Local Libraries :
* From [PSPICE NETLIST] section of C:\Users\apple\AppData\Roaming\SPB_Data\cdssetup\OrCAD_PSpice\17.2.0\PSpice.ini file:
.lib "nomd.lib" 

*Analysis directives: 
.TRAN  0 100m 0 10u 
.OPTIONS ADVCONV
.PROBE64 V(alias(*)) I(alias(*)) W(alias(*)) D(alias(*)) NOISE(alias(*)) 
.INC "..\SCHEMATIC1.net" 


.END
