lab11/signpost/software/apps/message_test/main.c

#include <string.h>
#include <stdio.h>
#include <stdlib.h>
#include <unistd.h>
#include <stdint.h>
#include <stdbool.h>

#include <tock.h>
#include <firestorm.h>
#include <console.h>
#include "message.h"
#include "gpio.h"
#include "i2c_master_slave.h"

//#define SENDER

int main (void) {


    uint8_t data[1024];

#ifdef SENDER
    message_init(0x25);
    i2c_master_slave_listen();

    //send some messages
    for(uint16_t i = 0; i < 1024; i++) {
        data[i] = i;
    }

    //a short message
    delay_ms(1000);
    message_send(0x19, data, 25);
    message_recv(data,1024,data);

    //a longer message
    delay_ms(1000);
    message_send(0x19, data, 1024);

    //a message that hits a data limit (single packet)
    delay_ms(1000);
    message_send(0x19, data, 247);

    //a message that hits a data limit (>1 packet)
    delay_ms(1000);
    message_send(0x19, data, 494);
#else

    for(uint16_t i = 0; i < 1024; i++) {
        data[i] = ((i % 256) & 0x00FF);
    }

    message_init(0x19);
    message_set_read_buffer(data,1024);

    while(1) {
        yield();
    }

    //receive and echo those messages
    uint8_t src;
    uint16_t len;
    len = message_recv(data,1024,&src);
    message_send(src,data,len);

    len = message_recv(data,1024,&src);
    message_send(src,data,len);

    len = message_recv(data,1024,&src);
    message_send(src,data,len);

    len = message_recv(data,1024,&src);
    message_send(src,data,len);
#endif



}
