lab11/signpost/software/apps/fm25cl_test/main.c

#include <string.h>
#include <stdio.h>
#include <stdlib.h>
#include <unistd.h>
#include <stdint.h>
#include <stdbool.h>

#include "tock.h"
#include "console.h"
#include "fm25cl.h"

uint8_t read_buf[256];
uint8_t write_buf[256];

void print_status (status) {
  char buf[64];
  sprintf(buf, "\tStatus: 0x%02x\n\n", status);
  putstr(buf);
}

void print_buf () {
  char buf[64];
  sprintf(buf, "\tData: 0x%02x 0x%02x 0x%02x 0x%02x 0x%02x\n\n", read_buf[0], read_buf[1], read_buf[2], read_buf[3], read_buf[4]);
  putstr(buf);
}

int main () {
  putstr("[FM25CL] Test\n");

  fm25cl_set_read_buffer(read_buf, 256);
  fm25cl_set_write_buffer(write_buf, 256);

  int status = fm25cl_read_status_sync();
  print_status(status);

  write_buf[0] = 0x02;
  write_buf[1] = 0x06;
  write_buf[2] = 0x0a;
  write_buf[3] = 0x0e;
  write_buf[4] = 0x9f;

  // Write buf to FRAM and then read it back
  fm25cl_write_sync(0x24, 5);
  fm25cl_read_sync(0x24, 5);
  print_buf();
}
