lab11/signpost/modules/spectrum154/contiki/apps/scanner154/project-conf.h

#ifndef PROJECT_CONF_H_
#define PROJECT_CONF_H_

/*
 * @author: Brad Campbell <bradjc@umich.edu>
 */

#define NETSTACK_CONF_MAC nullmac_driver
#define NETSTACK_CONF_RDC nullrdc_driver
#define UIP_CONF_ROUTER 0

#define STARTUP_CONF_VERBOSE 1
#define UART_CONF_ENABLE 1

#endif /* PROJECT_CONF_H_ */

/** @} */
